axtar/Nixie-Calculator/Docs/Flashing the bootloader and the firmware.pdf

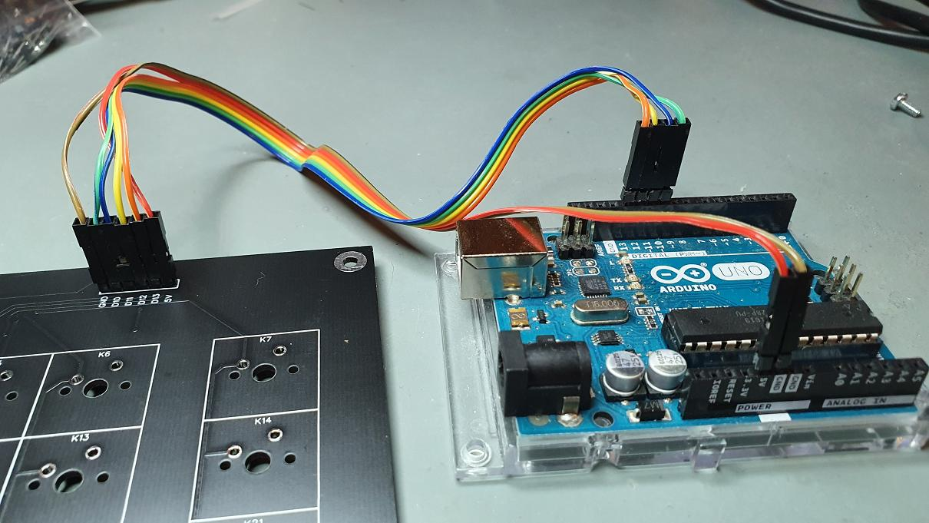
[picture p14: figure]

August 27, 2026 | Draft - Version 0.6 | Page 1 of 3

## Flashing the bootloader and the firmware

Note: the pictures are only intended for a better understanding of the instructions and may not correspond to the latest hardware revision.

### Burning the keyboard bootloader

The keyboard uses an ATmega328p-AU. The bootloader must be burned before flashing the firmware. With an Arduino UNO and the Arduino IDE, the bootloader can be burned directly on the keyboard. I recommend doing this before soldering the switches.

Remove all connections from the keyboard. Then connect the BOOTLOADER header pins to the Arduino UNO (see silkscreen).

Connect the Arduino UNO to your PC and start the Arduino IDE.

Select the Arduino UNO board:

Tools->Board

Select the com port:

Tools->Port->(your com port)

Open the ArduinoISP example:

File->Examples->11ArduinoISP->ArduinoISP

Upload the sketch to the Arduino UNO:

Sketch->Upload

Select the programmer:

Tools->Programmer->Arduino as ISP

Flash the bootloader:

Tools->Burn Bootloader

Check output for errors

### Flashing the keyboard firmware

For the keyboard I use either the Arduino IDE or Visual Studio Code with the PlatformIO extension.

(see Firmware/Keyboard/README_HowToBuild.md).

Power off the calculator and connect a 3.3V or 5V FTDI adapter to the FTDI header on the keyboard. Make sure you connect your adapter the correct way around by checking the ground pin (GND). Then compile and flash the firmware. Check output for errors.

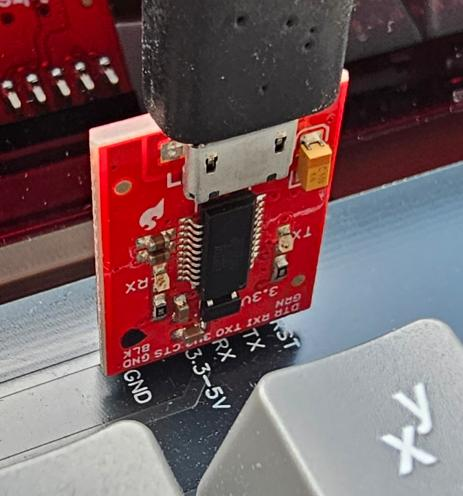
[picture p15: figure]

### Flashing the controller firmware

For the controller, I use Visual Studio Code with the ESP-IDF extension.

(see Firmware/Controller/README_HowToBuild.md)

Power off the calculator and connect a 3.3V FTDI adapter to the controller board. Make sure you connect your adapter the correct way around by checking the ground pin (GND).

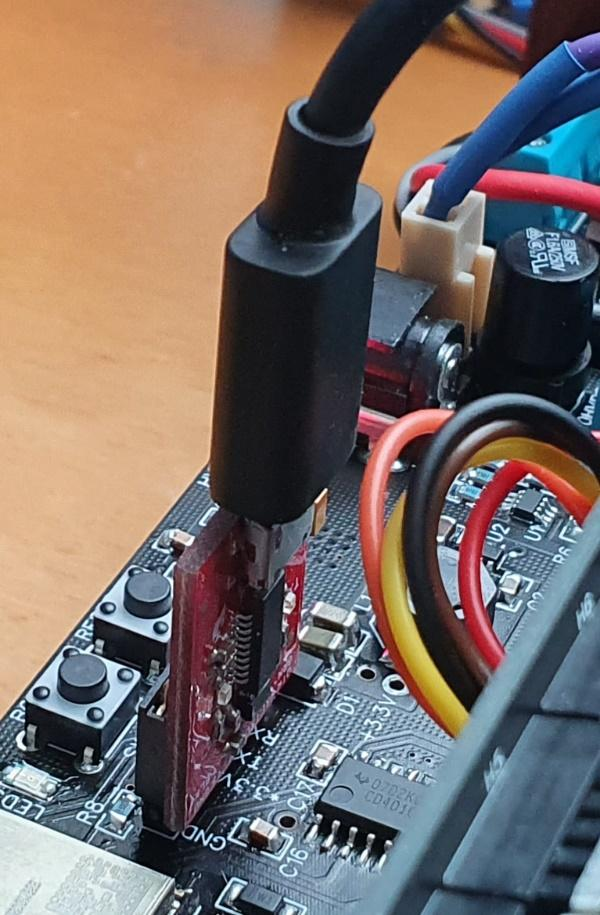
[picture p16: figure]

Build and start flashing the firmware. Once you get the “Connecting…” message, press and hold the “boot” button on the controller board, then press and release the “reset” button and finally release the “boot” button. This should start the flash process. Check output for errors.

### Check firmware versions

After flashing the controller and the keyboard firmware, remove the FTDI adapter and power on the calculator. During start-up, the calculator briefly shows the controller firmware version on the left and the keyboard firmware version on the right.
