axtar/Nixie-Calculator/Docs/Gerber and EasyEDA project files.pdf

August 27, 2026 | Draft – Version 0.3 | Page 1 of 1

## Gerber and EasyEDA project files

Please note that the Gerber files have been regenerated and are untested!

If you use the EasyEDA project files you can make changes and generate your own Gerber files.

You can open the project zip files directly in the EasyEDA designer (Std Edition)

File->Open->EasyEDA

You will get a schematic and a PCB and you can save them to a new project.

You can also import the project zip file into Kicad (8.0.6 or higher) and continue from there.

The case has been designed for 1.6mm boards. For this project I recommend ENIG black for the label board and lead-free (RoHS) black for the other boards. Black boards look better behind the acrylic panel.
