axtar/Nixie-Calculator/Docs/High Voltage Power Supply.pdf

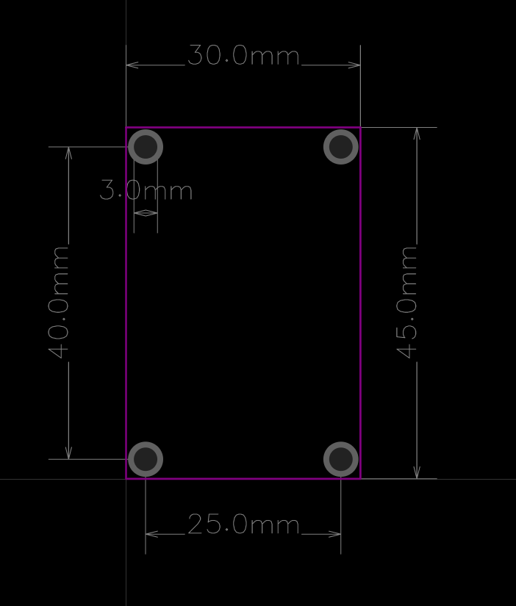
[picture p17: figure]

August 27, 2026 | Draft – Version 0.6 | Page 1 of 2

## High Voltage Power Supply

Although an experimental design for a high-voltage power supply is provided, the use of a good quality and well-tested commercial HV PSU is strongly recommended. Make sure to use genuine power supplies only!

If you decide to design your own HV PSU, you can find the suggested dimensions below.

The HV PSU must be able to deliver at least 50 mA at 170V DC with an input voltage of 12V DC without generating a lot of heat.

Add an appropriate fuse for the HV rail to protect your device from overcurrent!

The voltage should be stable for the entire current range. A calculator is not like a clock, the number of turned-on nixies is not constant. Also check the PSU for audible noise - you don’t want to have a noisy device on your desk.

You may need to change the firmware to correctly drive the enable/shutdown pin of your HV PSU. Currently the firmware sets the HVENABLE pin to HIGH (+3.3V) to enable the HV.

Suggested dimensions:

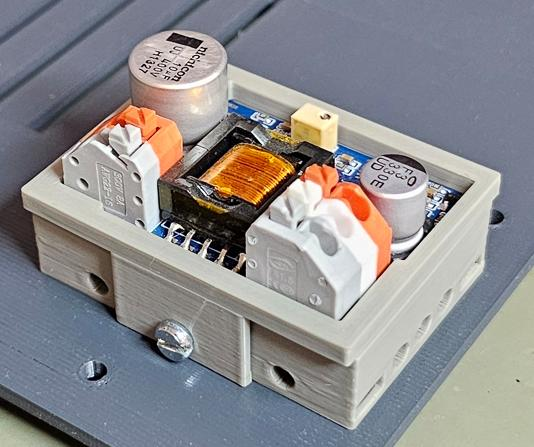
[picture p18: figure]

August 27, 2026 | Draft – Version 0.6 | Page 2 of 2

I’ve designed a 3D printed adapter for the popular NCH6300HV nixie power supply from Omnixie. Maybe the adapter is useful for someone, it provides the missing mounting holes. Use at your own risk.

The adapter consists of 2 parts: 3DPrints/STL/HVFIX Part 1.stl and 3DPrints/STL/HVFIX Part 2.stl. Additionally, you will need 6 x M3 square nuts and 6 x M3 6mm screws.
