axtar/Nixie-Calculator/Docs/Keyboard layout and keycaps.pdf

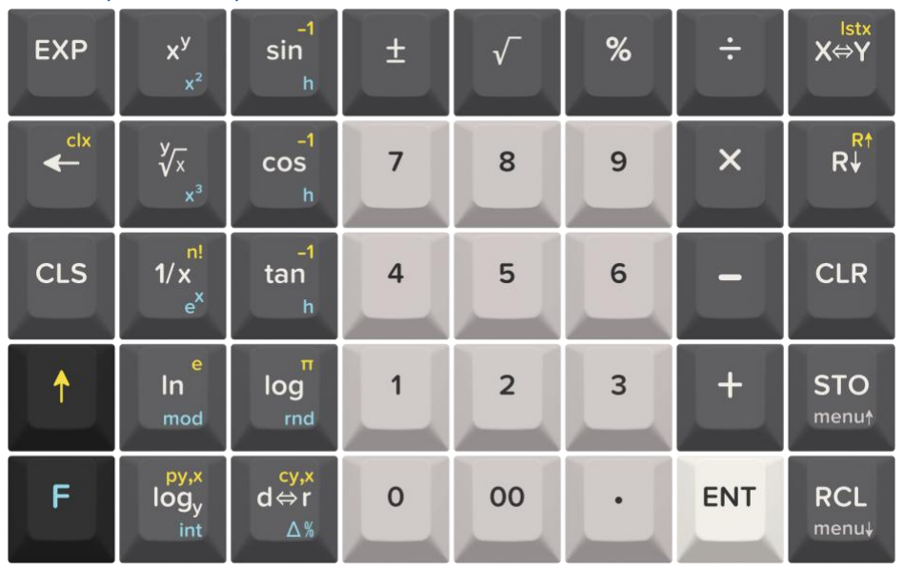
[picture p19: figure]
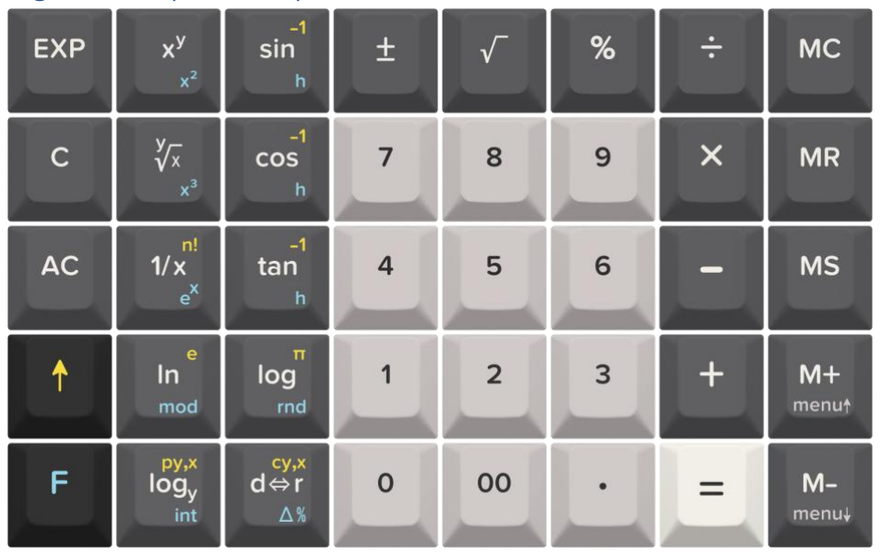
[picture p20: figure]

July 12, 2026 | Draft - Version 0.8 | Page 1 of 1

## Keyboard layout and keycaps

For this project we need some custom Cherry MX keycaps. I came up with the keyboard layouts as shown in the pictures. All keycaps are 1x1.

### RPN keyboard layout

### Algebraic keyboard layout

### Keycaps

If you prefer commercial keycaps, you may use the json design files in the Keycaps directory as a starting point for your own design. You can import the “tf” file into the Thockfactory configurator or the “yz” files into the Yuzu Keycaps advanced editor.

You can also use transparent keycaps (e.g. from X-keys) and print your own legends. I created the Keycaps/keycaps.svg file with Inkscape, then printed the “Legends” and the “Background” layers on glossy photo paper and finally cut out the “Keys” layer with a cutting plotter.
