axtar/Nixie-Calculator/Docs/Mounting the  nixies.pdf

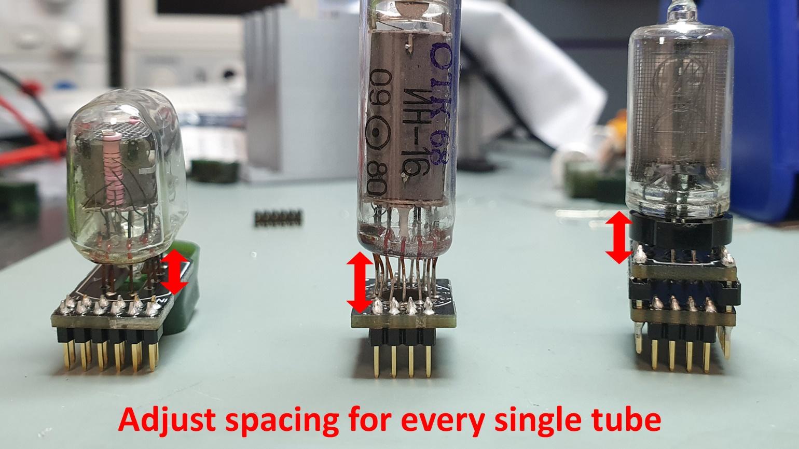
[picture p21: figure]

July 1, 2025 | Draft – Version 0.2 | Page 1 of 10

## Mounting the nixies

Note: the pictures are only intended for a better understanding of the instructions and may not correspond to the latest hardware revision.

The dimensions of tubes of the same type, as well as the position of the digits within the tube, can vary significantly. There are also different spacers for the B-5870. For this reason, I cannot provide the exact spacing for mounting the nixies on the socket boards.

- For the IN-16, IN-17 and B-5870 versions, don’t use nixies wider than 13mm if you cannot compensate the difference with the adjacent tubes. Also check, that the exhaust tips are not too long to fit in the case.
However, I haven't had any problems with any of my (unmatched) tubes so far.
- Correctly adjust the distance between the end of the tube and the top of the socket board to have all digits at the same level and to make sure that they fit into the case. A good starting point is 5mm for the IN-16 and 4mm for the IN-17. For the B-5870, I just used the plastic spacer, my tubes have a small one. However, it is up to you to find the correct spacing.
- Always check that everything is correct before soldering the nixies to the socket boards.
- Don’t stress the leads/pins of the nixies.

### IN-12/IN-15A version

The nixies are mounted on appropriate socket pins.

- Display board with the socket pins

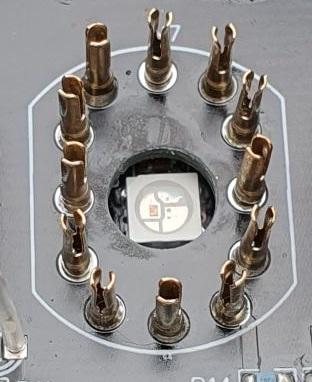
[picture p22: figure]

- Insert the nixie and check orientation, pin order and alignment

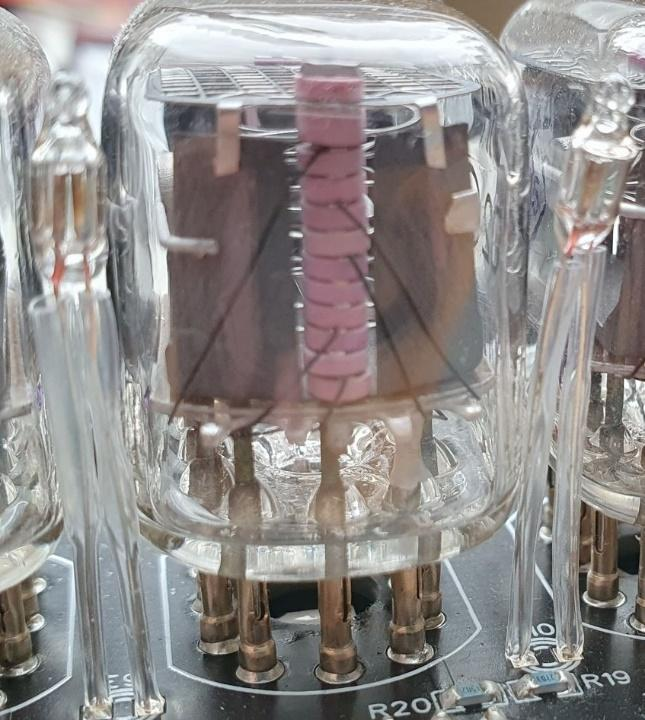
[picture p23: figure]

### IN-16 version

The nixies are soldered on a socket board without the plastic spacer to allow underlighting. The calculator uses the right decimal point of the nixie. A = anode.

- IN-16 socket board

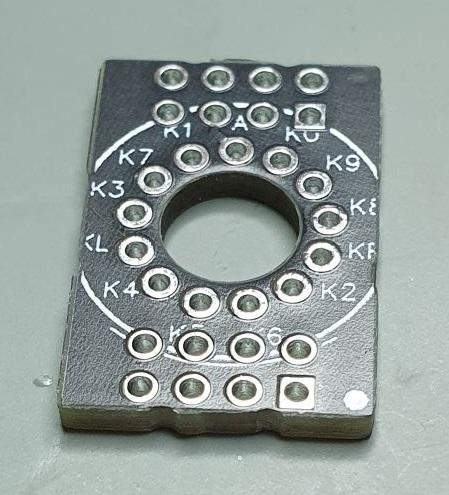
[picture p24: figure]

- Insert the nixie leads into the socket board

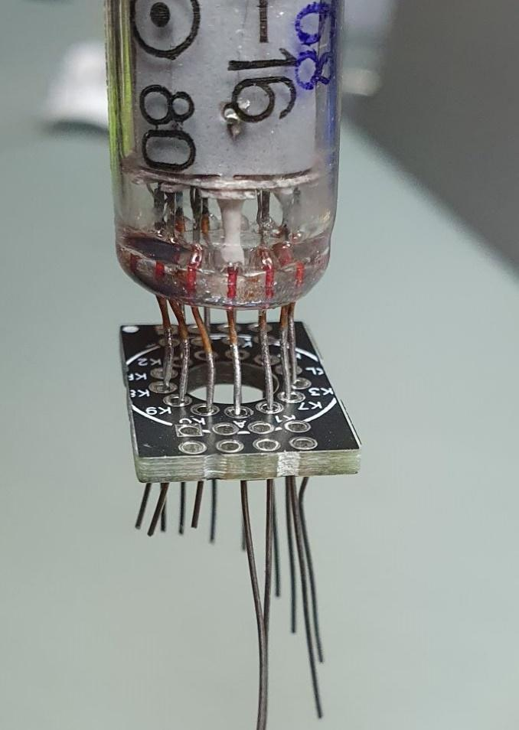
[picture p25: figure]

- Check orientation, pin order, alignment and spacing
- Solder the nixie leads and cut off the excess

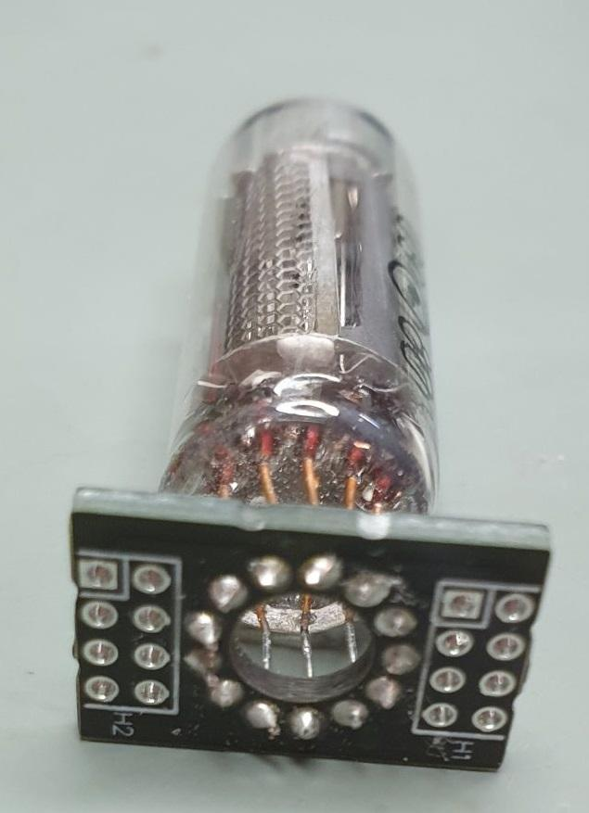
[picture p26: figure]

- Mount and solder the headers

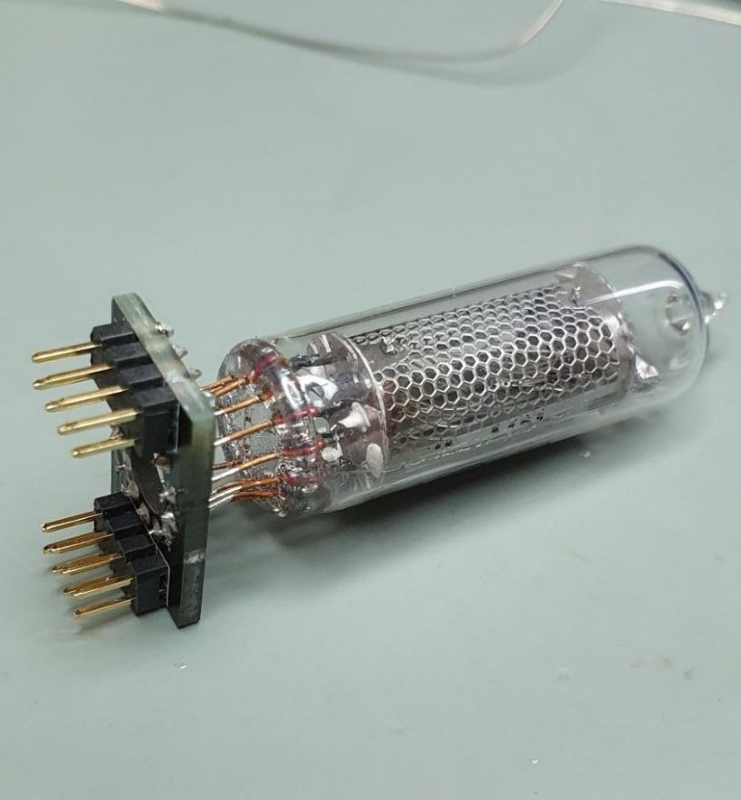
[picture p27: figure]

### IN-17 version

The IN-17 nixies are soldered on a socket board without the plastic spacer to allow backlighting. A = anode.

- IN-17 socket board

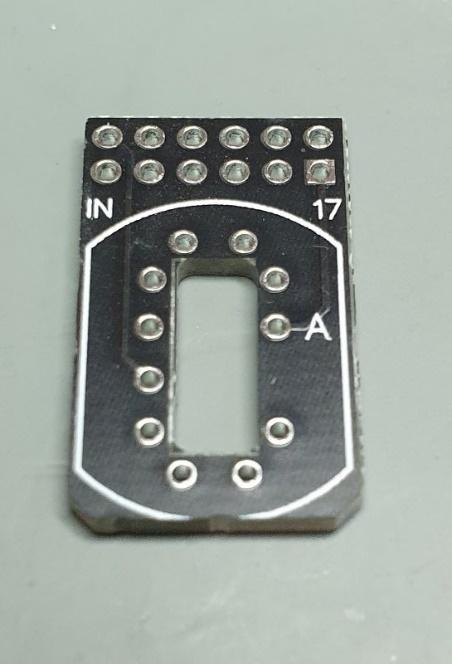
[picture p28: figure]

- Insert the nixie leads into the socket board

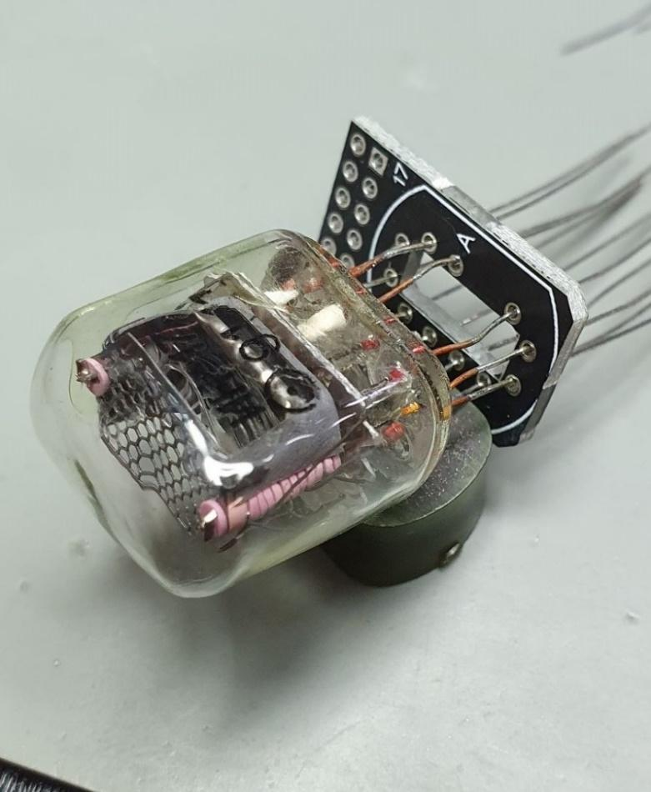
[picture p29: figure]

- Check orientation, pin order, alignment and spacing
- Solder the nixie leads and cut off the excess

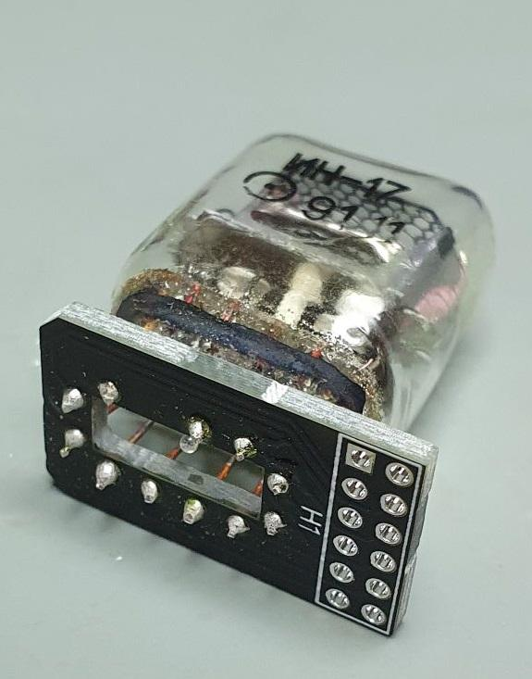
[picture p30: figure]

- Mount and solder the header

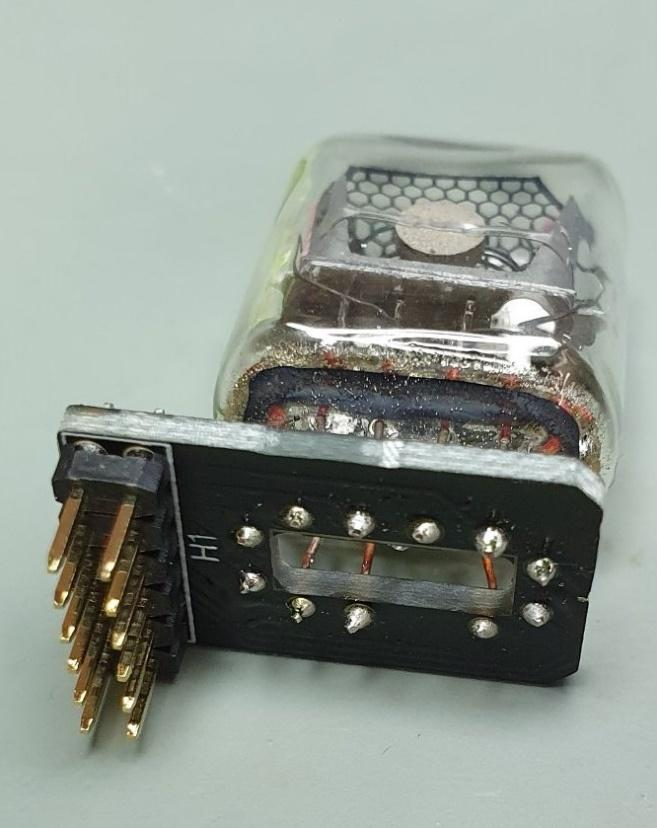
[picture p31: figure]

### B-5870 version

The nixies are soldered on a socket board. Since there is no underlighting available for the B-5870 version, it is up to you to decide whether you use the plastic spacer or not. Please note that there are different sizes of spacers for these tubes. The socket board is mounted on an additional adaptor board. The calculator uses the right decimal point of the nixie.

- B-5870 socket board

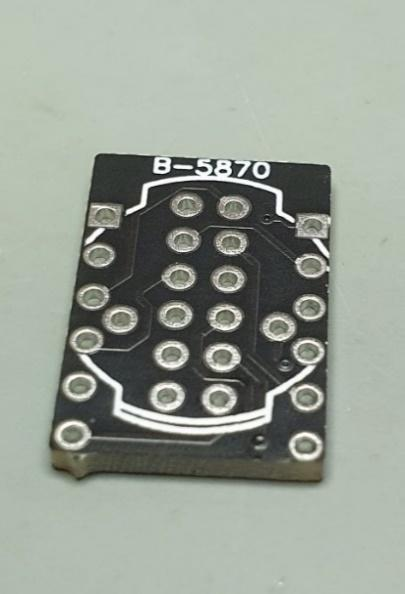
[picture p32: figure]

- Mount and solder the headers

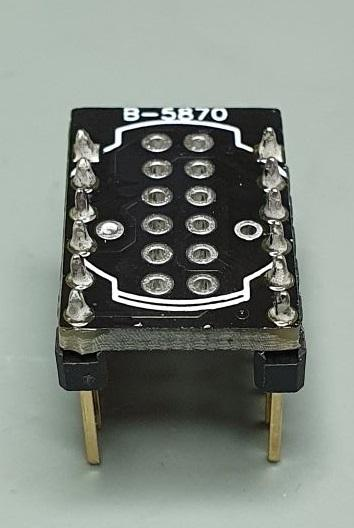
[picture p33: figure]

- Insert the nixie leads into the socket board

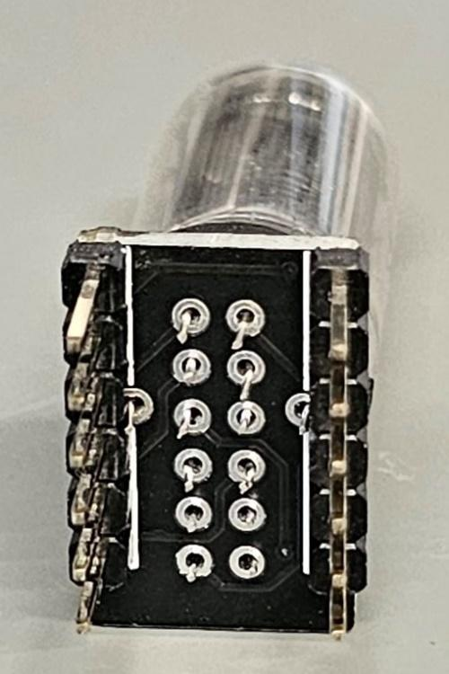
[picture p34: figure]

- Check orientation, pin order, alignment and spacing
- Solder the nixie leads and cut off the excess

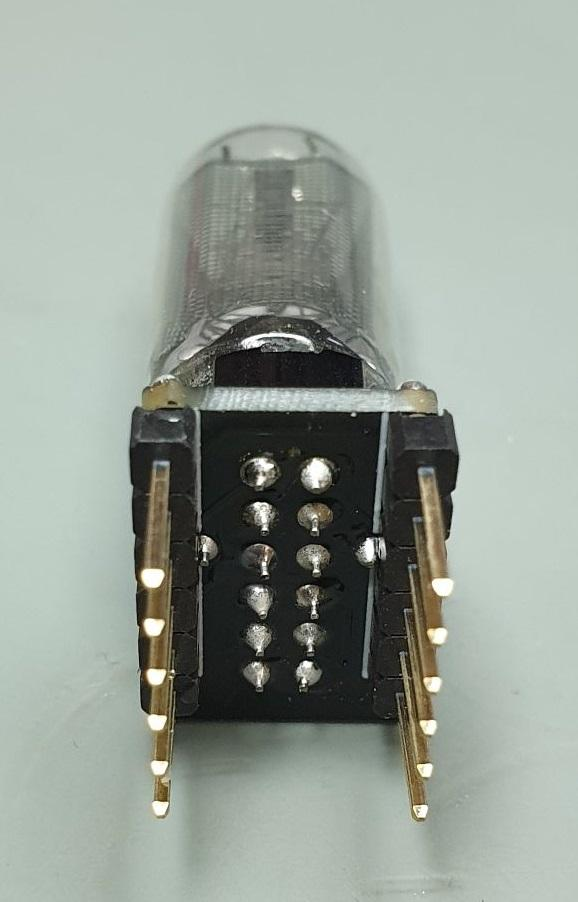
[picture p35: figure]

- B-5870 socket adaptor board

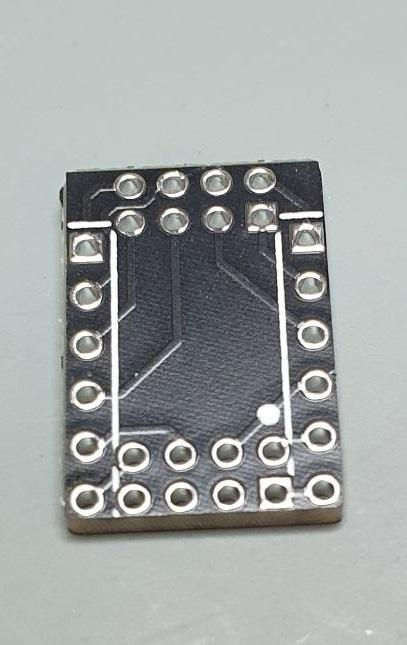
[picture p36: figure]

- Mount and solder the headers

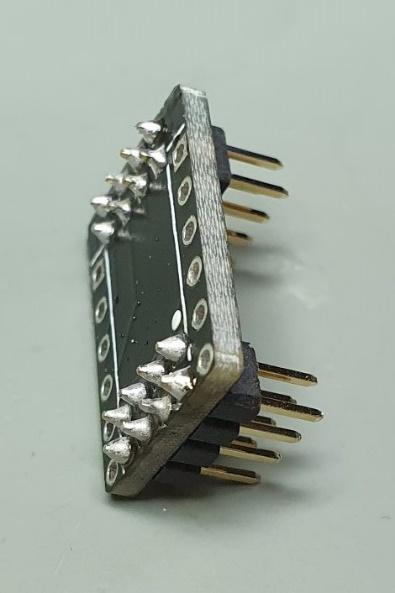
[picture p37: figure]

- Solder the socket board to the socket adaptor board leaving a gap between them

Make sure, that there are no shorts between the socket board and the adaptor board!

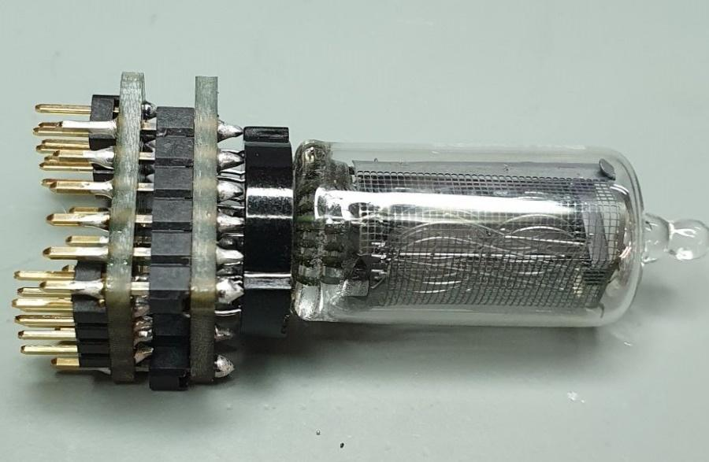
[picture p38: figure]
