axtar/Nixie-Calculator/Docs/PCB List.pdf

September 1, 2026 | Draft – Version 0.3 | Page 1 of 2

## PCB List

IN-12 Version
Qty | Board | Comment
1 | Controller_Rev2a
1 | Keyboard_Rev2
1 | IN-12_Display_Rev2
1 | IN-12_Driver_Rev2
1 | IN-12_LEDs_Rev2
1 | High_Voltage_PSU_Rev2 | only required if not using a commercial PSU
1 | Label_Rev2

IN-16 Version
Qty | Board | Comment
1 | Controller_Rev2a
1 | Keyboard_Rev2
1 | IN-16_Display_Rev2
1 | IN-16_Driver_Rev2
1 | IN-16_LEDs_Rev2 | for underlighting only (recommended)
14 | IN-16_Socket_Rev2
1 | High_Voltage_PSU_Rev2 | only required if not using a commercial PSU
1 | Label_Rev2

IN-17 Version
Qty | Board | Comment
1 | Controller_Rev2a
1 | Keyboard_Rev2
1 | IN-17_Display_and_Driver_Rev2
14 | IN-17_Socket_Rev2
1 | High_Voltage_PSU_Rev2 | only required if not using a commercial PSU
1 | Label_Rev2

B-5870 Version
Qty | Board | Comment
1 | Controller_Rev2a
1 | Keyboard_Rev2
1 | IN-16_Display_Rev2
1 | IN-16_Driver_Rev2
14 | B-5870_Socket_Rev2
14 | B-5870_Socket_Adaptor_Rev2
1 | High_Voltage_PSU_Rev2 | only required if not using a commercial PSU
1 | Label_Rev2

September 1, 2026 | Draft – Version 0.3 | Page 2 of 2

7-seg LED version
Qty | Board | Comment
1 | Controller_Rev2a
1 | Keyboard_Rev2
1 | LED7SEG_Display_Rev1
1 | LED7SEG_Driver_Rev1
1 | Label_Rev2

Peripherals
Qty | Board | Comment
1 | Peripherals_Rev2
