axtar/Nixie-Calculator/BOM/BOM_Nixie_Calculator_7SEGLED_Display_Rev1.pdf

BOM Nixie Calculator 7SEGLED Display Rev.1 | 30/06/2025
ID | Quantity | Value | Additional | Designator | Footprint | Type | Manufacturer Part | Manufacturer
1 | 2 | SC36-11SURKWA | | LED0,LED15 | | 7-seg LED display | SC36-11SURKWA | Kingbright
2 | 14 | SC56-11SURKWA | | LED1-LED14 | | 7-seg LED display | SC56-11SURKWA | Kingbright
3 | 1 | 2x17 box header, 2.54mm | | P1 | | Box header
