axtar/Nixie-Calculator/BOM/BOM_Nixie_Calculator_7SEGLED_Driver_Rev1.pdf

BOM Nixie Calculator 7SEGLED Driver Rev.1 | 30/06/2025
ID | Quantity | Value | Additional | Designator | Footprint | Type | Manufacturer Part | Manufacturer
1 | 2 100n | | 50V | C1,C2 | 0805 | Capacitor | C0805C104M5RACTU | KEMET
2 | 2 39k | | | R1,R2 | 0805 | Resistor | RK73H2ATTD3902F | KOA Speer
3 | 2 MAX7219CWG+ | | | U0,U1 | SOIC-24 | LED driver | MAX7219CWG+ | Analog Devices
4 | 1 1x6 header, 2.54mm | | | J1 | | Locking header
5 | 1 2x17 box header, 2.54mm | | | P1 | | Box header
