axtar/Nixie-Calculator/BOM/BOM_Nixie_Calculator_IN-12_Display_Rev2.pdf

BOM Nixie Calculator IN-12 Display Rev.2 | 19/07/2025
ID | Quantity | Value | Additional | Designator | Footprint | Type | Manufacturer Part | Manufacturer
1 | 16 | 15k | 1/4W | R0-R15 | 0805 | Resistor | RK73H2ATTD1502F | KOA Speer
2 | *14 | 270k | 1/4W | R16-R29 | 0805 | Resistor | RK73H2ATTD2703F | KOA Speer
3 | **14 | 82k | 1/4W | R30-R43 | 0805 | Resistor | RK73H2ATTD8202F | KOA Speer
4 | 2 | IN-15A Nixie | | N0,N15 | | Nixie tube
5 | 14 | IN-12A or IN-12B Nixie | | N1-N14 | | Nixie tube
6 | *14 | Neon 4mm | | E1-14 | | Neon lamp
7 | 1 | 2 poles terminal block | | HV | | Fixed Terminal Block | TB006-508-02BE | CUI Devices
8 | 32 | 1x6 Header | female, 200V | H1-H32 | | Header
9 | 192 | Single receptacle contacts | for 1mm pins
* if using neon bulbs as decimal point
** if using IN-12B decimal point
