axtar/Nixie-Calculator/BOM/BOM_Nixie_Calculator_IN-12_Driver_Rev2.pdf

BOM Nixie Calculator IN-12 Driver Rev.2 | 30/06/2025
ID | Quantity | Value | Additional | Designator | Footprint | Type | Manufacturer Part | Manufacturer
1 | 6 | 100n | 50V | C1-C6 | 0805 | Capacitor | C0805C104M5RACTU | KEMET
2 | 6 | HV5622 | | U1-U6 | PQFP-44 | IC | HV5622PG-G | Microchip Technology
3 | 32 | 1x6 header 2.54mm | male, 200V | J1-J32 | | Header
4 | 1 | 1x6 header, 2.54mm | male, right angle | H1 | | Locking header
