axtar/Nixie-Calculator/BOM/BOM_Nixie_Calculator_IN-12_LEDs_Rev2.pdf

BOM Nixie Calculator IN-12 LEDs Rev.2 | 30/06/2025
ID | Quantity | Value | Additional | Designator | Footprint | Type | Manufacturer Part | Manufacturer
1 | 1 | 330 | 1/4W | R1 | 0805 | Resistor | RK73H2ATTD3300F | KOA Speer
2 | 16 | 100n | 50V | C1-C16 | 0805 | Capacitor | C0805C104M5RACTU | KEMET
3 | 1 | 47uF | 25V | C17 | 1206 | Capacitor | C3216X5R1E476M160AC | TDK
4 | 16 | Neopixel RGB SK6812 | | D1-D16 | 5050 | RGB LED | SK6812
5 | 1 | 1x3 header, 2.54mm | male, right angle | H1 | | Locking header
