axtar/Nixie-Calculator/BOM/BOM_Nixie_Calculator_IN-16_LEDs_Rev2.pdf

BOM Nixie Calculator IN-16 LEDs Rev.2 | 30/06/2025
ID | Quantity | Value | Additional | Designator | Footprint | Type | Manufacturer Part | Manufacturer
1 | 1 | 330 | 1/4W | R1 | 0805 | Resistor | RK73H2ATTD3300F | KOA Speer
2 | 1 | 47uF | 25V | C1 | 1206 | Capacitor | C3216X5R1E476M160AC | TDK
3 | 14 | Neopixel RGB SK6812 | | D1-D14 | 5050 | RGB LED | SK6812
* | H1: there is no space for a header, solder the wires directly to the board
