axtar/Nixie-Calculator/3DPrints/STL/Nixie Calculator Keyboard Cover.stl

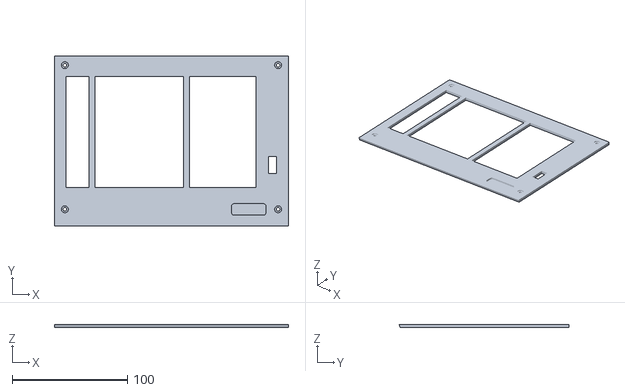
[picture p55: CAD file, 2026-09-16]
3DPrints/STL/Nixie Calculator Keyboard Cover.stl
203.0 x 147.5 x 3.00
