axtar/Nixie-Calculator/3DPrints/STL/Nixie Calculator IN-12 Back Shield.stl

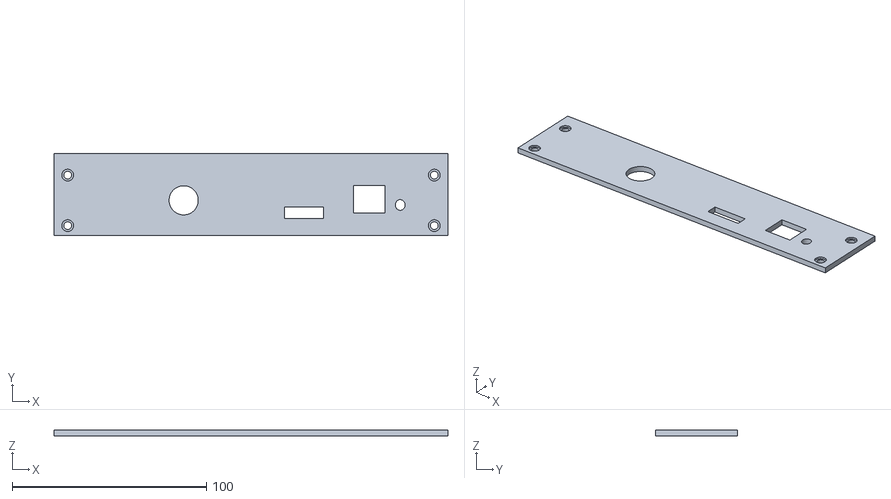
[picture p56: CAD file, 2026-09-16]
3DPrints/STL/Nixie Calculator IN-12 Back Shield.stl
202.8 x 42.0 x 3.00
