axtar/Nixie-Calculator/3DPrints/STL/Nixie Calculator IN-12 Tube Holder Part 2.stl

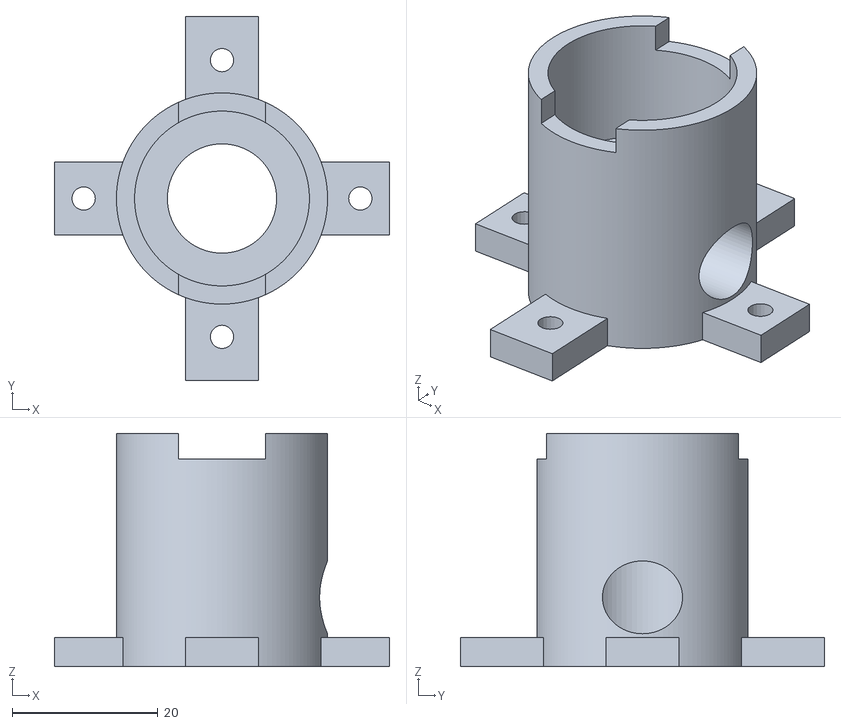
[picture p57: CAD file, 2026-09-16]
3DPrints/STL/Nixie Calculator IN-12 Tube Holder Part 2.stl
46.0 x 50.0 x 32.0
