axtar/Nixie-Calculator/3DPrints/STL/Nixie Calculator IN-12 Top.stl

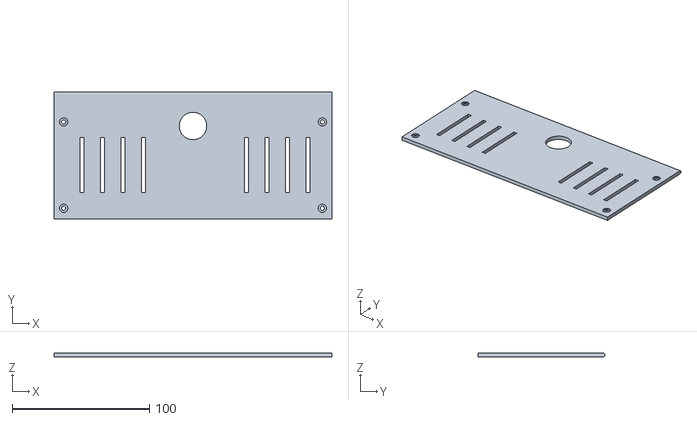
[picture p58: CAD file, 2026-09-16]
3DPrints/STL/Nixie Calculator IN-12 Top.stl
202.8 x 93.0 x 3.00
