axtar/Nixie-Calculator/3DPrints/STL/Nixie Calculator IN-12 Left.stl

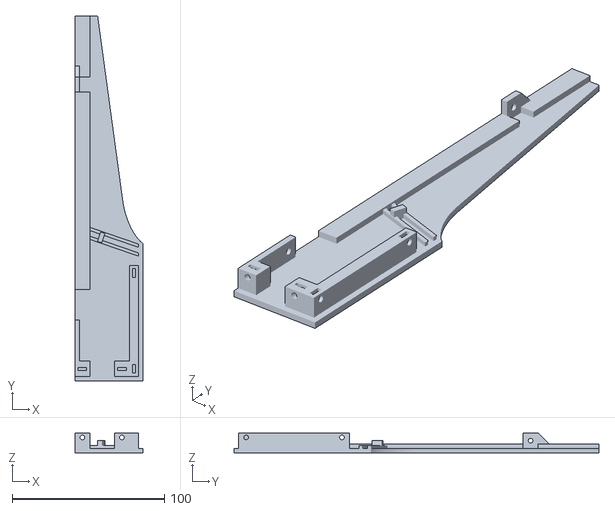
[picture p59: CAD file, 2026-09-16]
3DPrints/STL/Nixie Calculator IN-12 Left.stl
45.0 x 240.0 x 13.0
