axtar/Nixie-Calculator/3DPrints/STL/Nixie Peripherals RJ45 Part3.stl

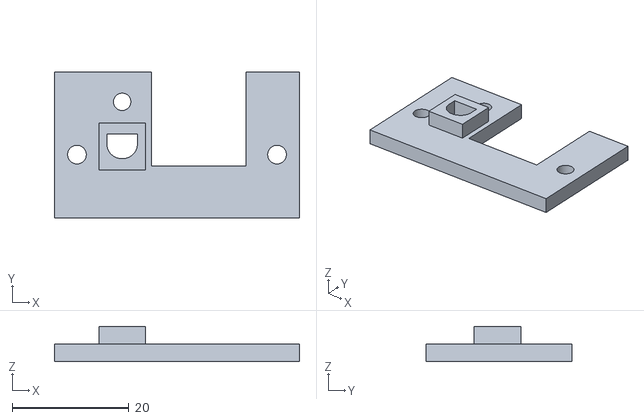
[picture p60: CAD file, 2026-09-16]
3DPrints/STL/Nixie Peripherals RJ45 Part3.stl
42.0 x 25.0 x 6.00
