axtar/Nixie-Calculator/3DPrints/STL/Nixie Calculator Back Shield.stl

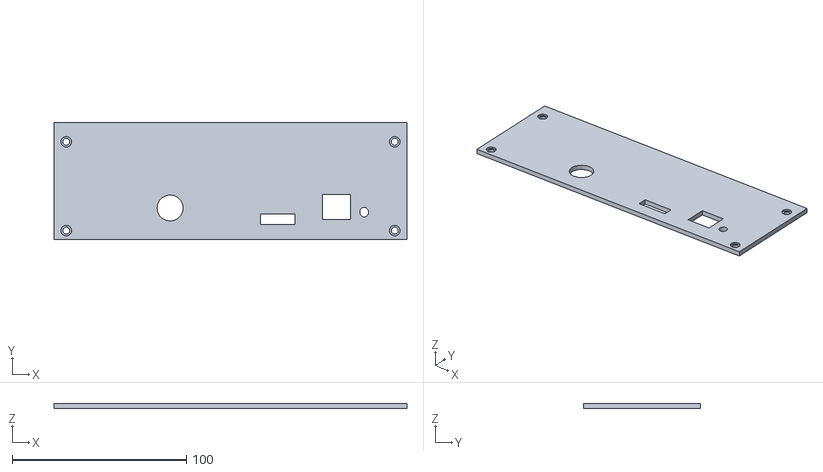
[picture p61: CAD file, 2026-09-16]
3DPrints/STL/Nixie Calculator Back Shield.stl
202.8 x 67.0 x 3.00
