axtar/Nixie-Calculator/3DPrints/STL/Nixie Peripherals RJ45 Part 2.stl

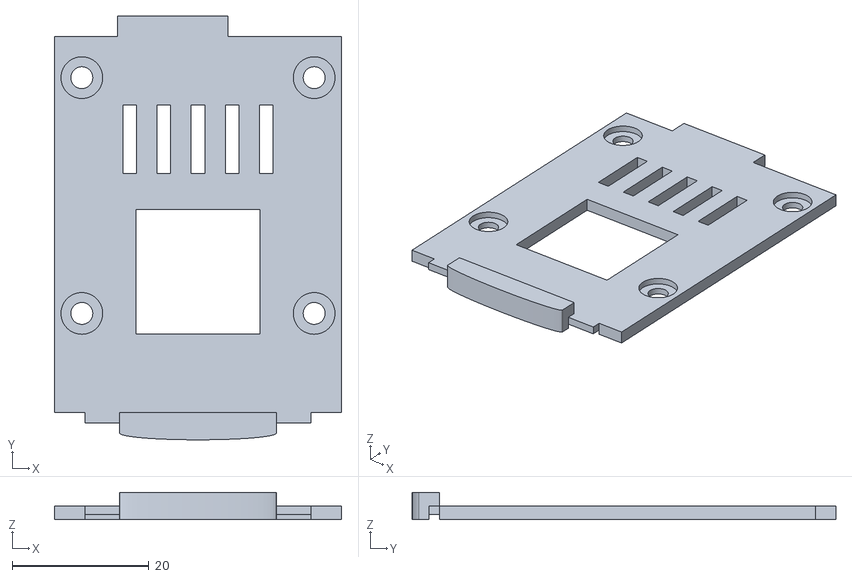
[picture p62: CAD file, 2026-09-16]
3DPrints/STL/Nixie Peripherals RJ45 Part 2.stl
42.0 x 62.0 x 4.00
