axtar/Nixie-Calculator/3DPrints/STL/Nixie Calculator Front V2.stl

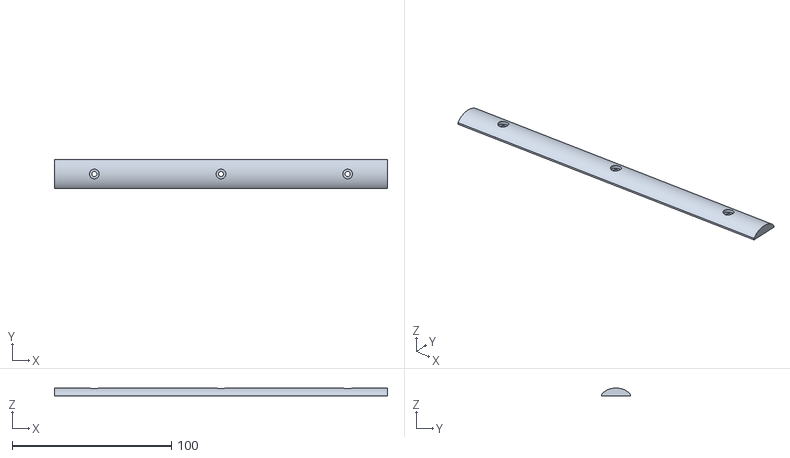
[picture p63: CAD file, 2026-09-16]
3DPrints/STL/Nixie Calculator Front V2.stl
209.0 x 18.0 x 5.00
