axtar/Nixie-Calculator/3DPrints/STL/HVFIX Part 2.stl

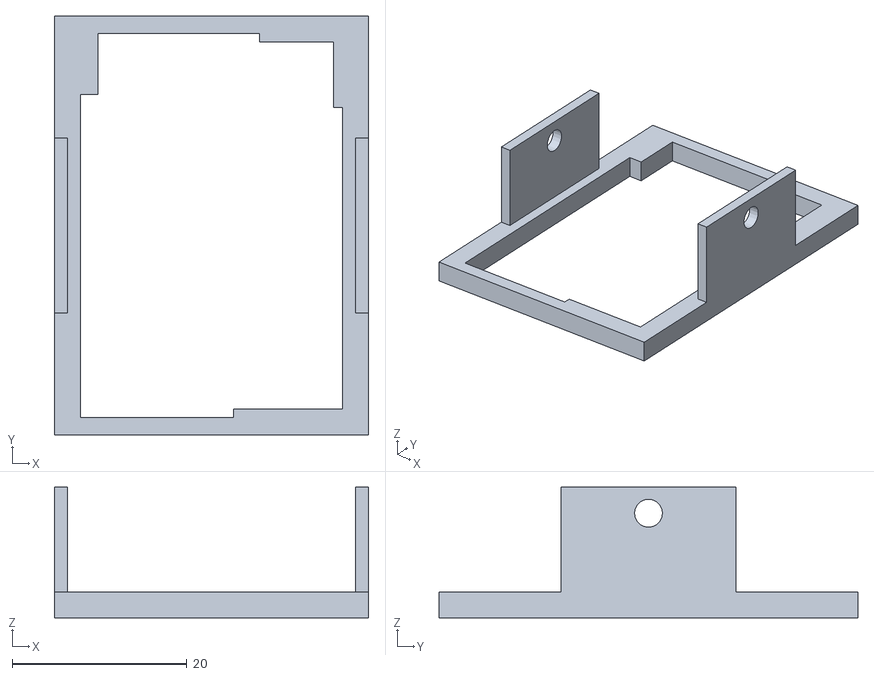
[picture p64: CAD file, 2026-09-16]
3DPrints/STL/HVFIX Part 2.stl
36.0 x 48.0 x 15.0
