axtar/Nixie-Calculator/3DPrints/STL/Nixie Calculator IN-17 Display Frame.stl

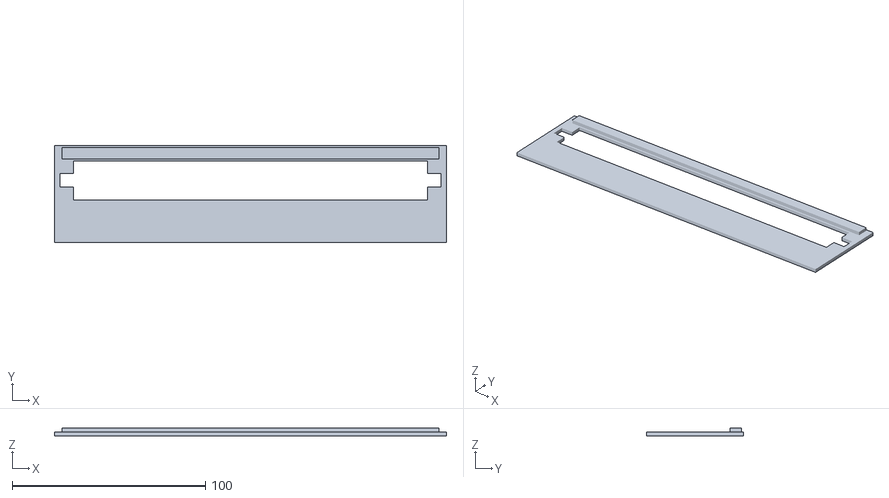
[picture p65: CAD file, 2026-09-16]
3DPrints/STL/Nixie Calculator IN-17 Display Frame.stl
203.0 x 50.0 x 4.00
