axtar/Nixie-Calculator/3DPrints/STL/Nixie Calculator Top.stl

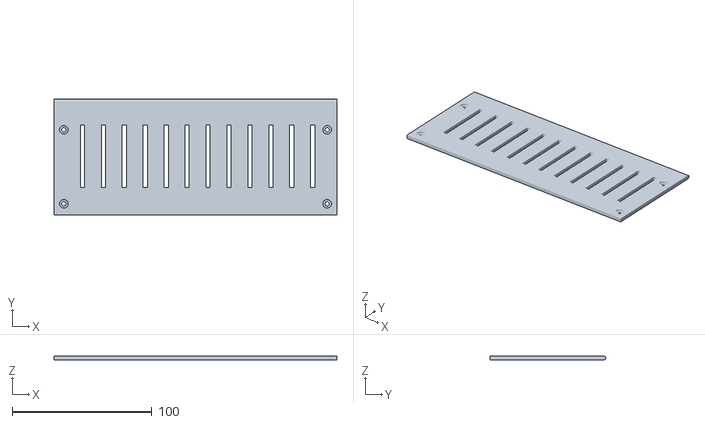
[picture p66: CAD file, 2026-09-16]
3DPrints/STL/Nixie Calculator Top.stl
202.8 x 83.0 x 3.00
