axtar/Nixie-Calculator/3DPrints/STL/Nixie Calculator B-5870 Socket Cover.stl

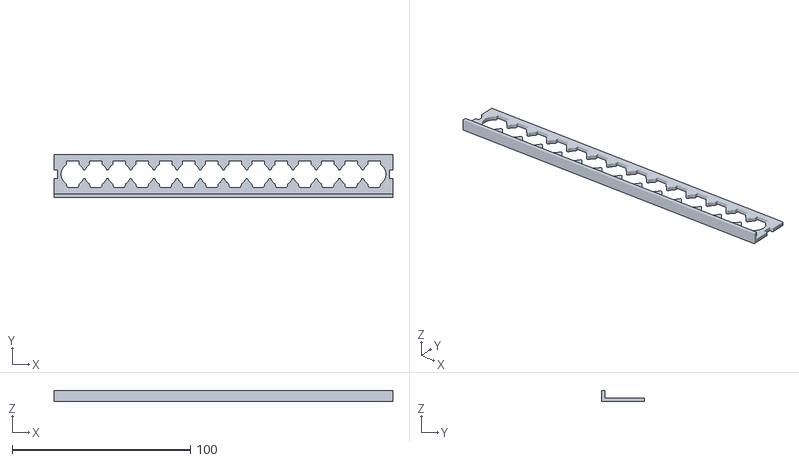
[picture p67: CAD file, 2026-09-16]
3DPrints/STL/Nixie Calculator B-5870 Socket Cover.stl
190.0 x 24.0 x 6.00
