axtar/Nixie-Calculator/3DPrints/STL/Nixie Peripherals RJ45 Part 1.stl

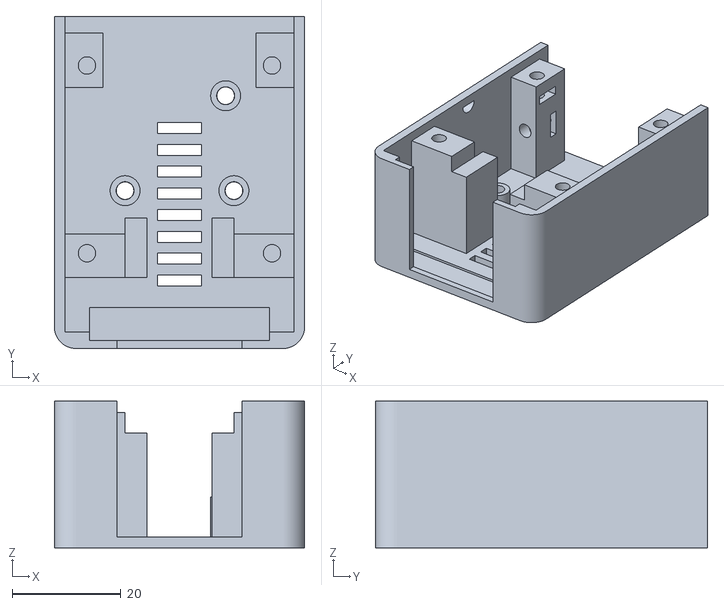
[picture p68: CAD file, 2026-09-16]
3DPrints/STL/Nixie Peripherals RJ45 Part 1.stl
46.0 x 61.0 x 27.0
