axtar/Nixie-Calculator/3DPrints/STL/Nixie Calculator IN-12 Union Tube V2.stl

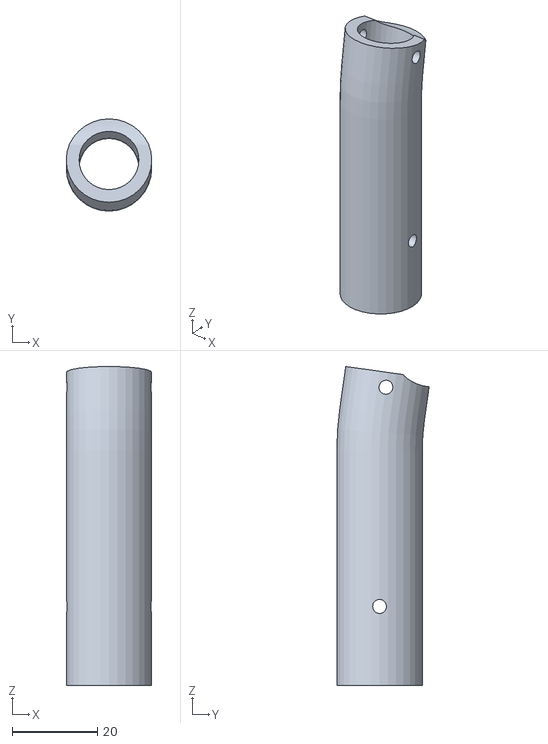
[picture p69: CAD file, 2026-09-16]
3DPrints/STL/Nixie Calculator IN-12 Union Tube V2.stl
20.0 x 21.6 x 74.6
