axtar/Nixie-Calculator/Docs/Assembling the calculator - 7-seg LED - version.pdf

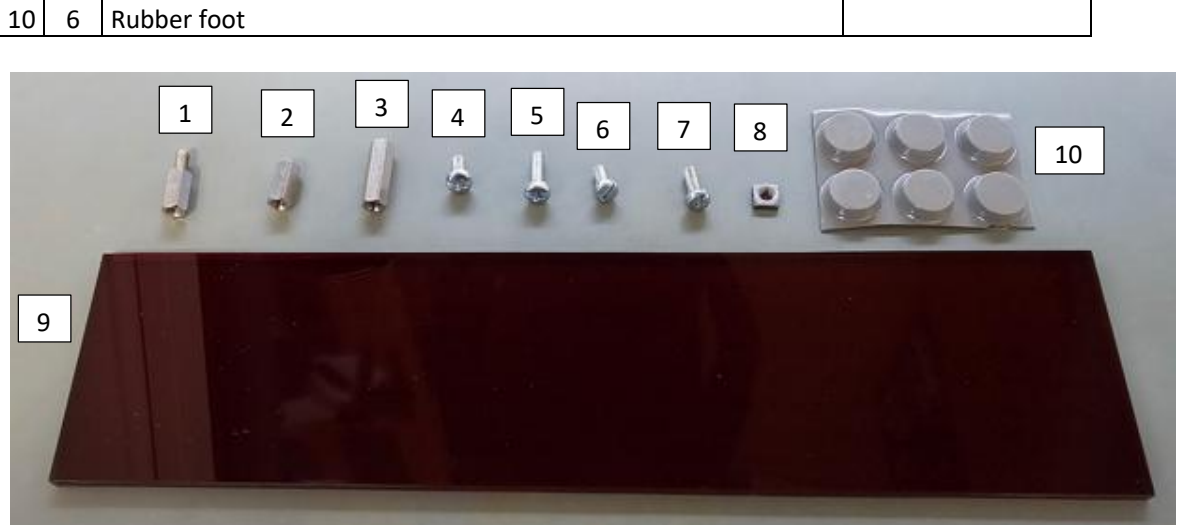
[picture p70: figure]
Rubber foot

August 27, 2026 | Draft - Version 0.5 | Page 1 of 9

## Assembling the calculator – 7-seg LED - version

Note: the pictures are only intended for a better understanding of the instructions and may not correspond to the latest hardware revision.

### Things you will need

- Assembled boards
- Keycaps
- Cables and connectors:
ID | Qty | Wires | Mode | Comment
SWITCH | 1 | 2 | straight | Mount connectors on both ends
KEYBOARD | 1 | 5 | straight | Mount connectors on both ends
DRIVER | 1 | 6 | straight | Mount connectors on both ends
P1 | 1 | 34 | straight | Ribbon cable, mount connectors on both ends
Double-check the pin order and polarity of all connections before you power up the device.
- 3D printed case parts
- Additional parts:
ID | Qty | Description | Comment
1 | 6 | Standoff, 10mm, female/male
2 | 10 | Standoff, 10mm, M3, female/female
3 | 3 | Standoff, 16mm, M3, female/female
4 | 4 | Pan head screw, 6mm, M3
5 | 11 | Pan head screw, 10mm, M3
6 | 17 | Screw, 6mm, M3
7 | 10 | Screw, 8mm, M3
8 | 16 | Square nut, M3, 5.5 x 5.5 x 1.8mm, DIN562
9 | 1 | Piece of transparent acrylic 203mm x 50mm x 3mm (red)

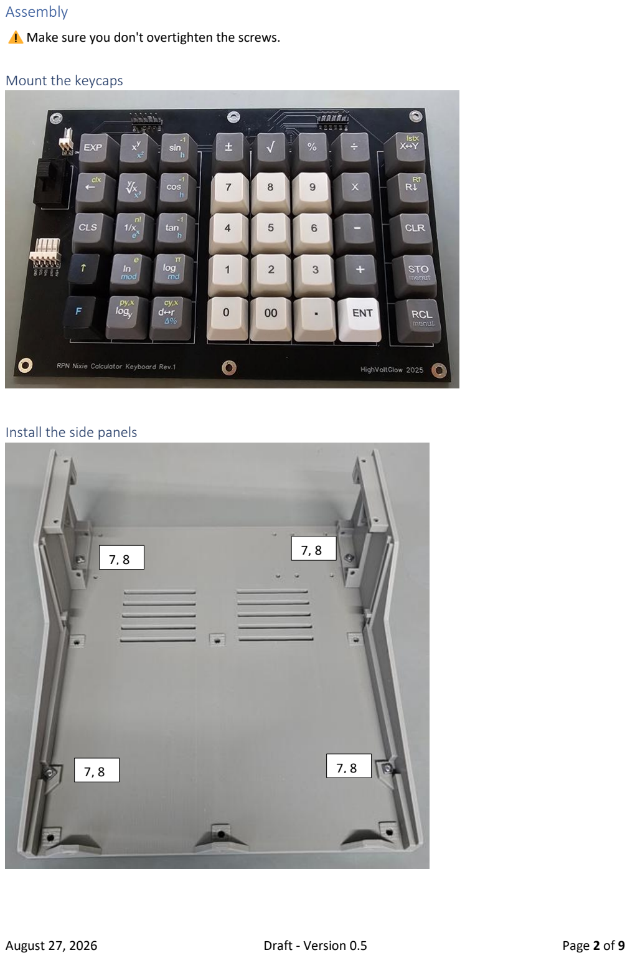
[picture p71: page 2]

### Assembly

Make sure you don't overtighten the screws.

Mount the keycaps

Install the side panels

7, 8

7, 8 | 7, 8

7, 8

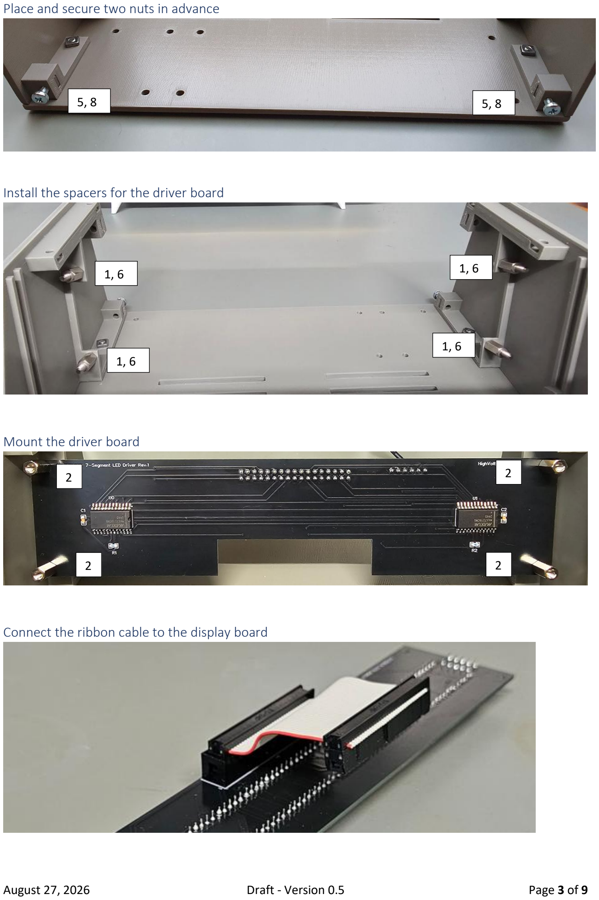
[picture p72: page 3]

Place and secure two nuts in advance

Install the spacers for the driver board

Mount the driver board

Connect the ribbon cable to the display board

5, 8 | 5, 8
1, 6 | 1, 6

1, 6

1, 6

2

2

2 | 2

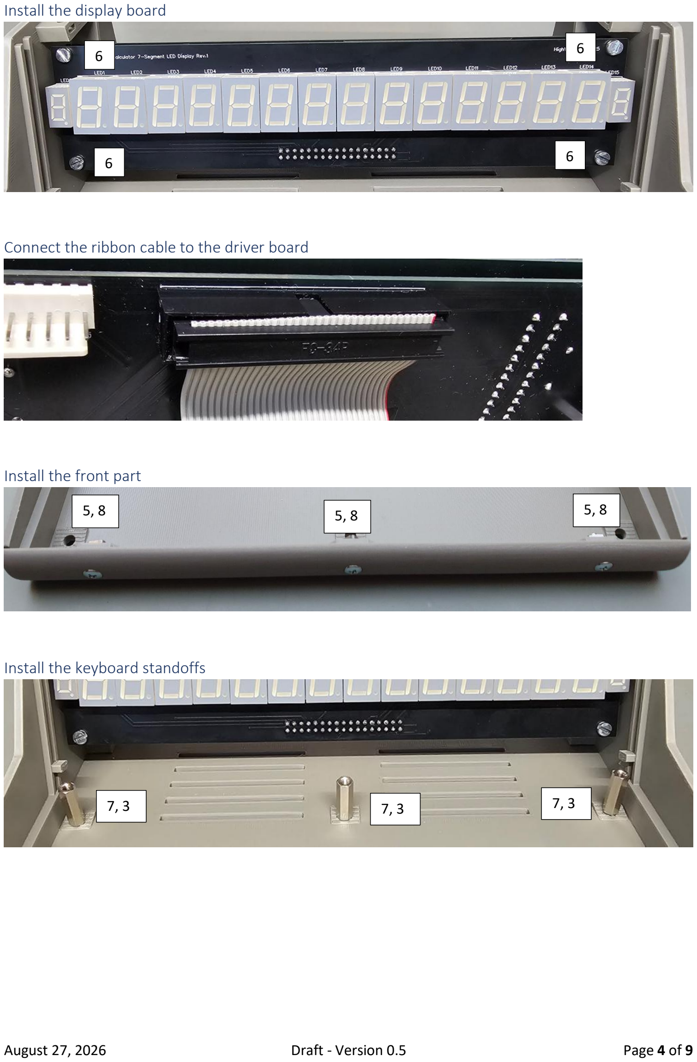
[picture p73: page 4]

Install the display board

Connect the ribbon cable to the driver board

Install the front part

Install the keyboard standoffs

5, 8 | 5, 8 | 5, 8
7, 3 | 7, 3 | 7, 3

6

6

6
6

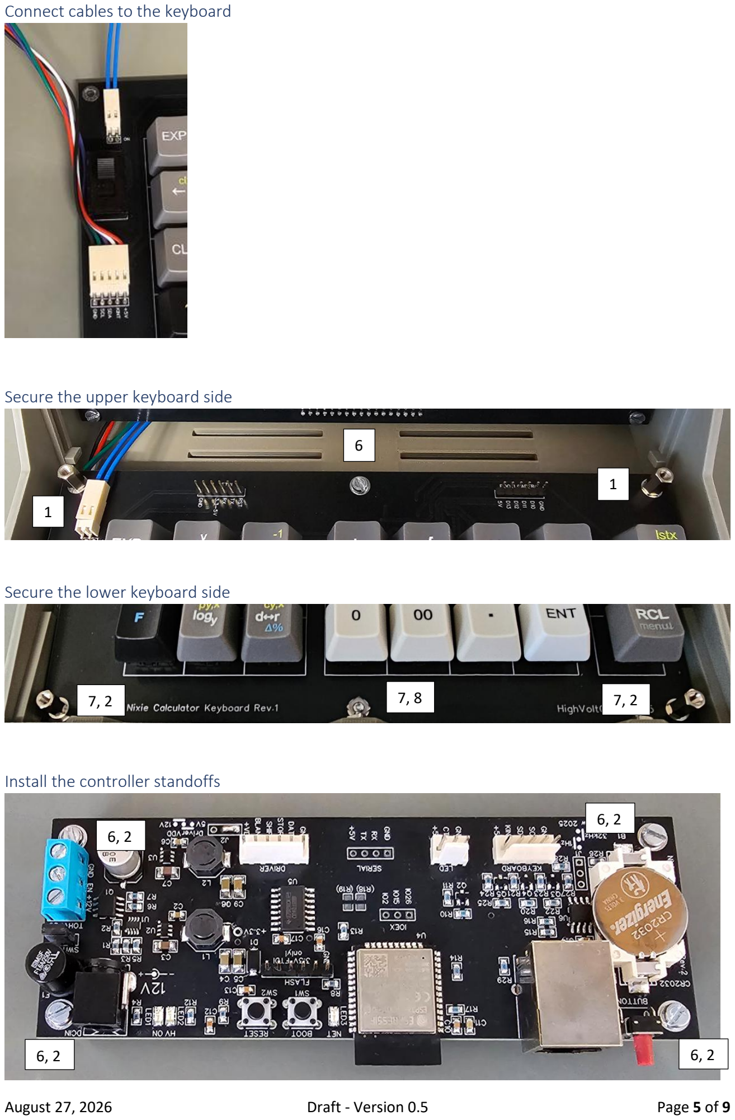
[picture p74: page 5]

Connect cables to the keyboard

Secure the upper keyboard side

Secure the lower keyboard side

Install the controller standoffs

1

1

6

7, 2 | 7, 8 | 7, 2

6, 2

6, 2

6, 2

6, 2

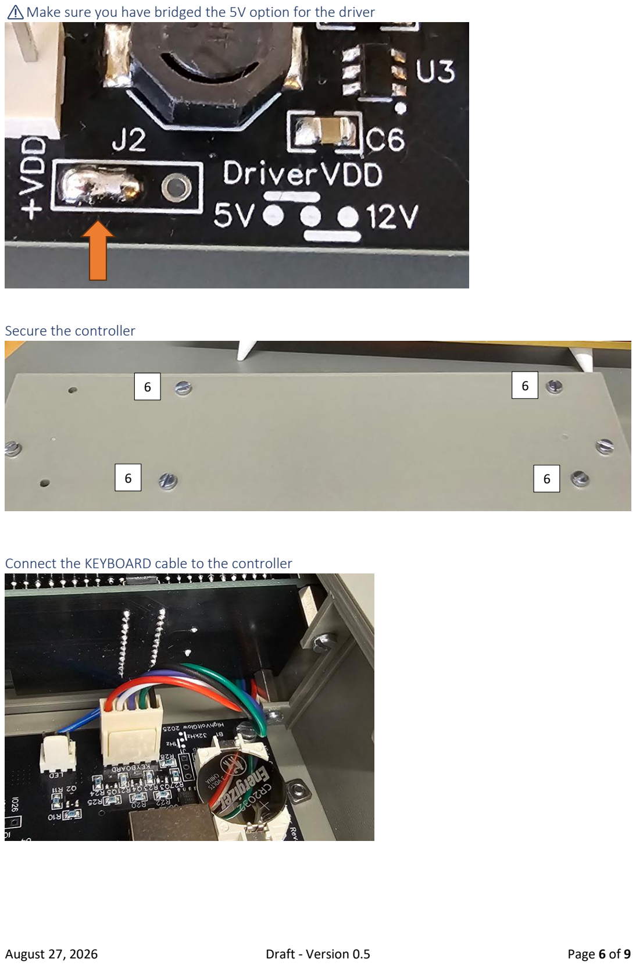
[picture p75: page 6]

⚠️Make sure you have bridged the 5V option for the driver

Secure the controller

Connect the KEYBOARD cable to the controller

6 | 6
6 | 6

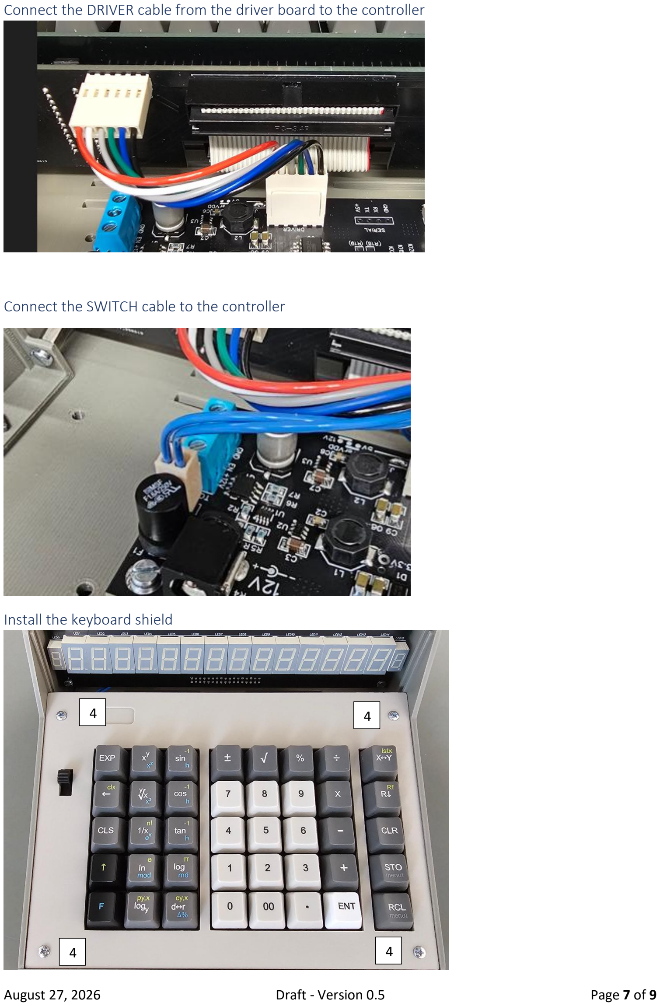
[picture p76: page 7]

Connect the DRIVER cable from the driver board to the controller

Connect the SWITCH cable to the controller

Install the keyboard shield

4 | 4
4 | 4

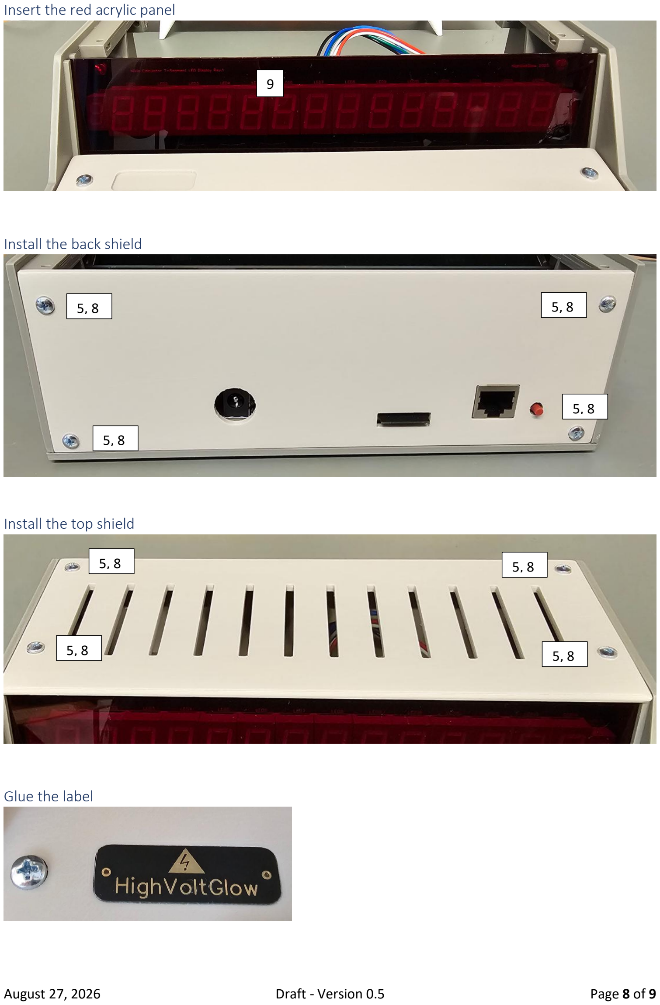
[picture p77: page 8]

Insert the red acrylic panel

Install the back shield

Install the top shield

Glue the label

5, 8 | 5, 8

5, 8

5, 8

5, 8 | 5, 8

5, 8 5, 8

9

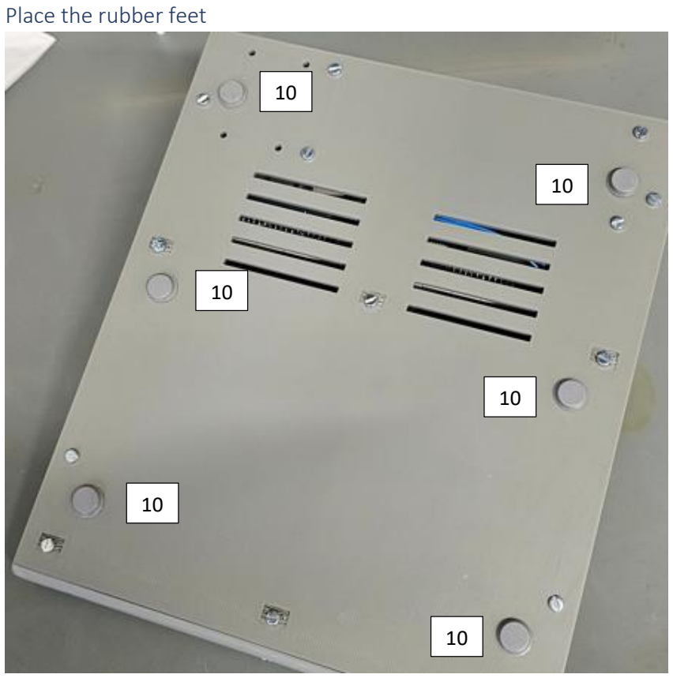
[picture p78: figure]
Place the rubber feet
