axtar/Nixie-Calculator/Docs/Assembling the PCBs.pdf

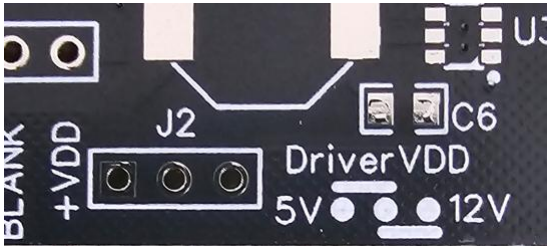
[picture p123: figure]

August 27, 2026 | Draft – Version 0.5 | Page 1 of 5

## Assembling the PCBs

### General information

Note: the pictures are only intended for a better understanding of the instructions and may not correspond to the latest hardware revision.

Since I cannot recommend this project for beginners, I will skip all the basic stuff and explain just a few things that might be of interest.

### Controller

Start assembling the input protection section including the LED and the fuse. Install a jumper on the SWITCH header. According to the datasheet the circuit should protect against overvoltage up to 60V and against reverse voltage down to -40V.

Connect the board to a variable power supply. Start with 12V - the LED should turn on. If you increase the voltage, the LED should turn off at around 13.5V. If you decrease the voltage, the LED should turn off at around 10V. These are only approximate values.

Then assemble the +3.3V and the +5V supplies and check that all voltages are correct.

Don’t populate the SERIAL, IOEX, J1 and J2 headers.

Select the VDD voltage for the display driver. For all nixie displays use a solder blob to connect the right pad to the middle pad of J2 (12V). For the 7-seg LED display connect the left pad to the middle pad of J2 (5V).

### Display and driver boards

IN-16 / B-5870 Versions
Please note that the B-5870 version also uses the IN-16 driver and the IN-16 display board.

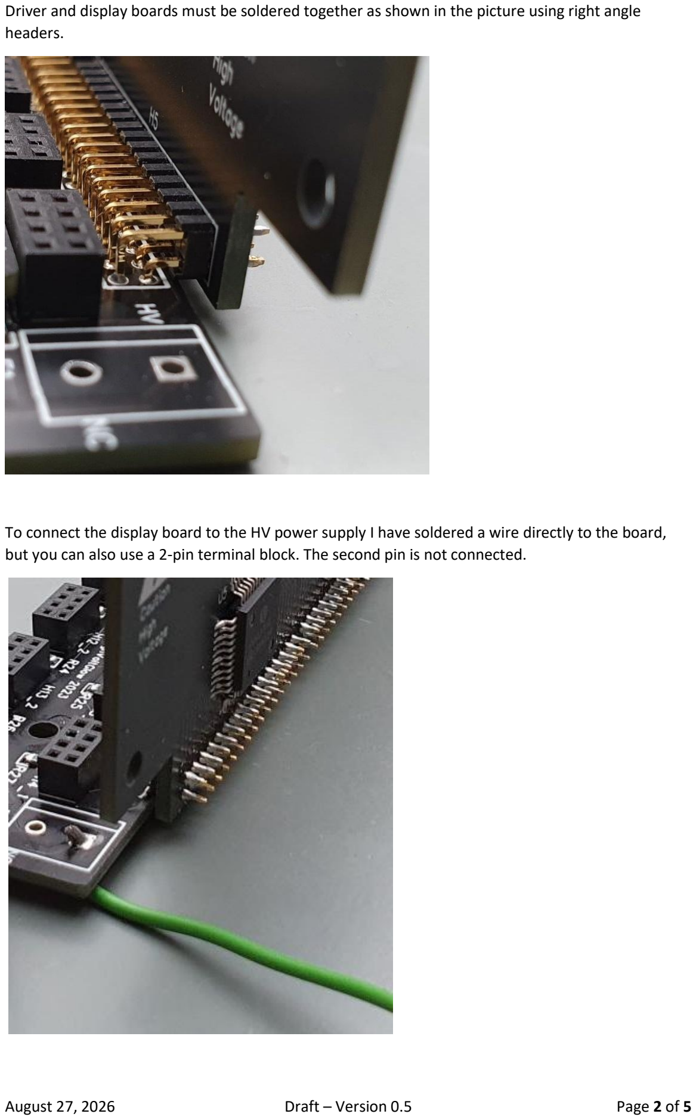
[picture p124: page 2]

Driver and display boards must be soldered together as shown in the picture using right angle headers.

To connect the display board to the HV power supply I have soldered a wire directly to the board, but you can also use a 2-pin terminal block. The second pin is not connected.

Use heat shrink tube (black recommended) for the neons (minus signs). I had to extend the wires a little bit to get the correct height.

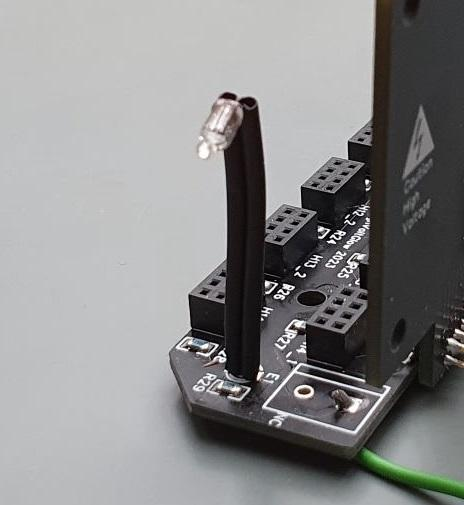
[picture p125: figure]

For the IN-16 version there are two options: LED backlighting or underlighting (recommended). For the B-5870 only backlighting is available.

For the IN-16 underlighting you must use the additional IN-16 LED board. Solder the 3-wire cable directly to the board. Use some black heat shrink tube to hide the cables behind the acrylic. Don’t populate the LEDs and the LED connector on the driver board.

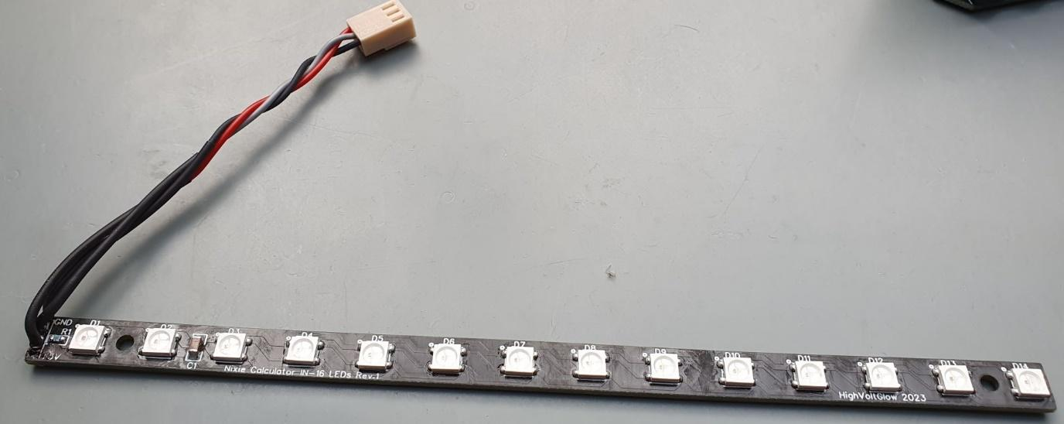
[picture p126: figure]
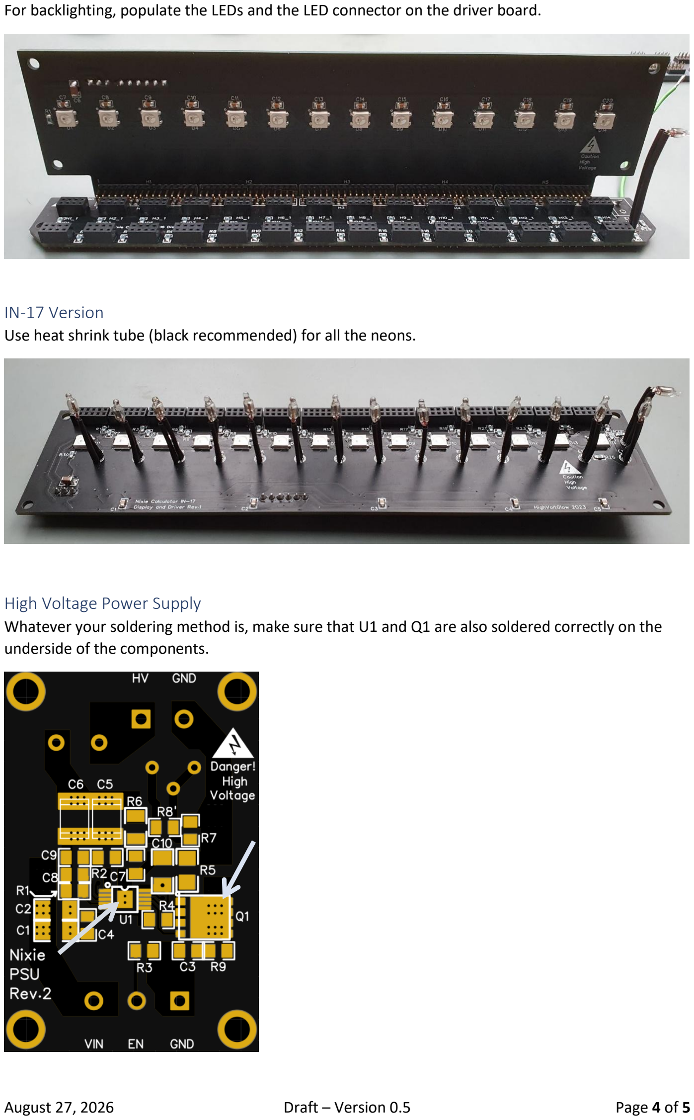
[picture p127: page 4]

For backlighting, populate the LEDs and the LED connector on the driver board.

IN-17 Version
Use heat shrink tube (black recommended) for all the neons.

High Voltage Power Supply
Whatever your soldering method is, make sure that U1 and Q1 are also soldered correctly on the underside of the components.

Peripherals module
Use heat shrink tube for the LED. Solder the cables directly to the board.

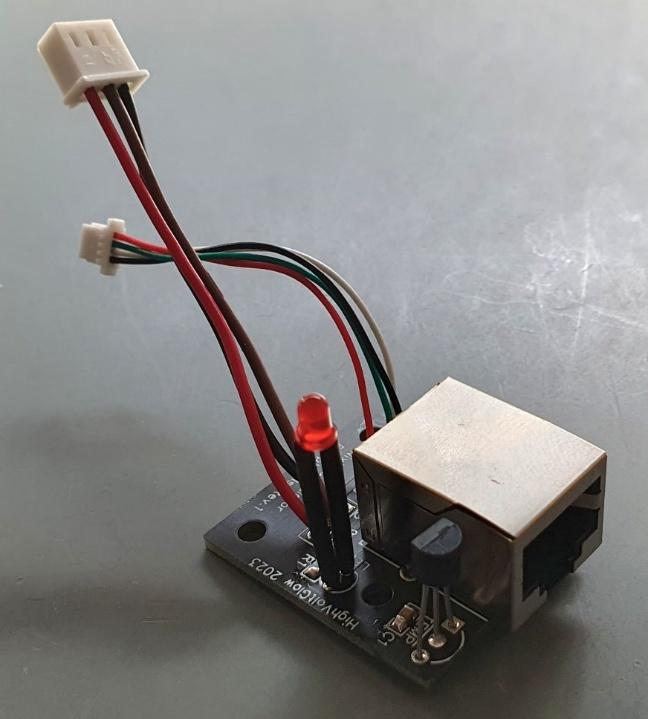
[picture p128: figure]
