axtar/Nixie-Calculator/Schematics/Schematic_Nixie_Calculator_IN-17_Display_and_Driver_Rev2.pdf

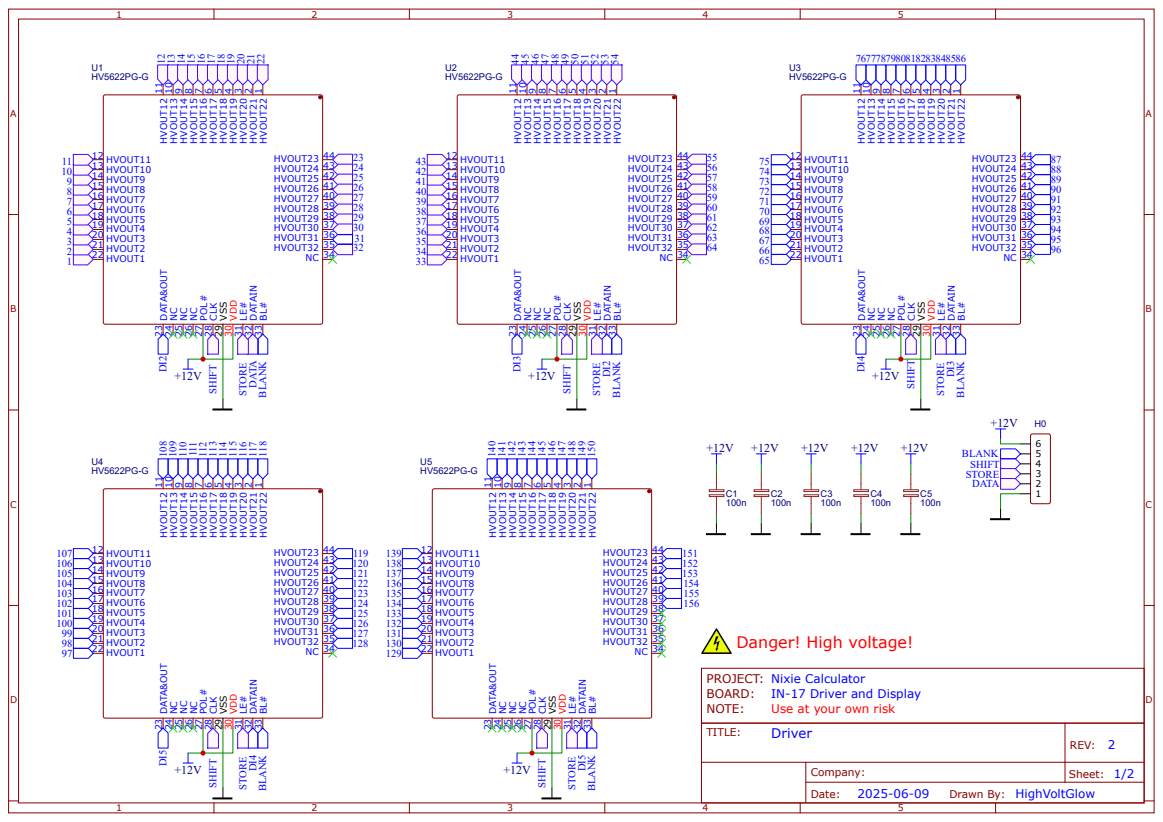
[picture p152: page 1]

PROJECT: Nixie Calculator
BOARD: IN-17 Driver and Display

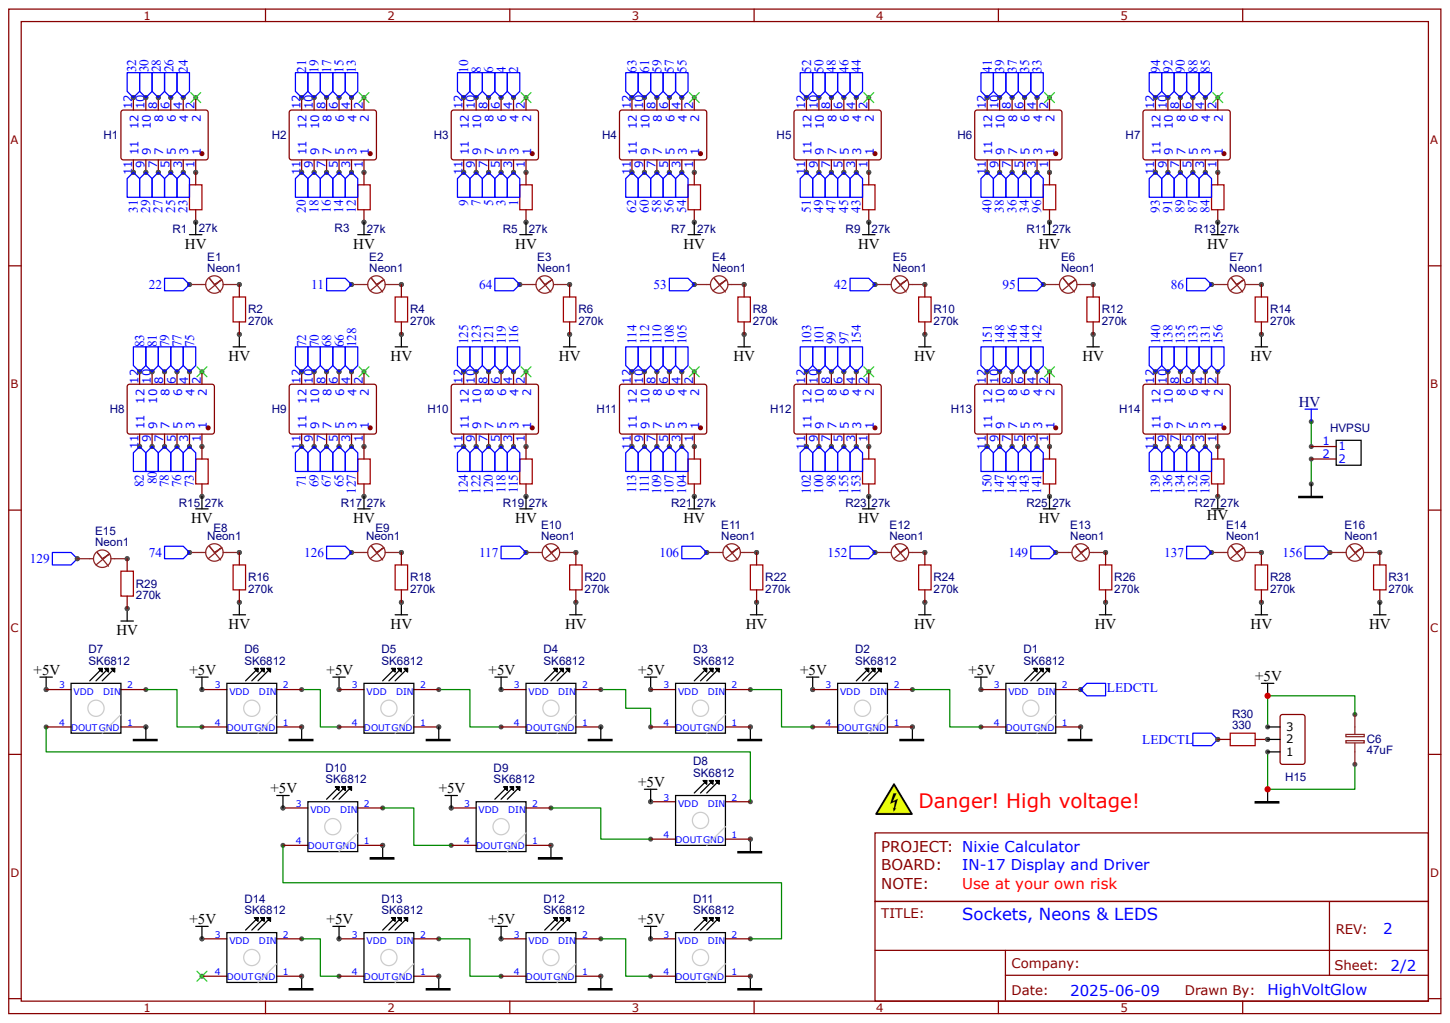
[picture p153: page 2]

PROJECT: Nixie Calculator
BOARD: IN-17 Display and Driver
