axtar/Nixie-Calculator/Schematics/Schematic_Nixie_Calculator_Peripherals_Rev2.pdf

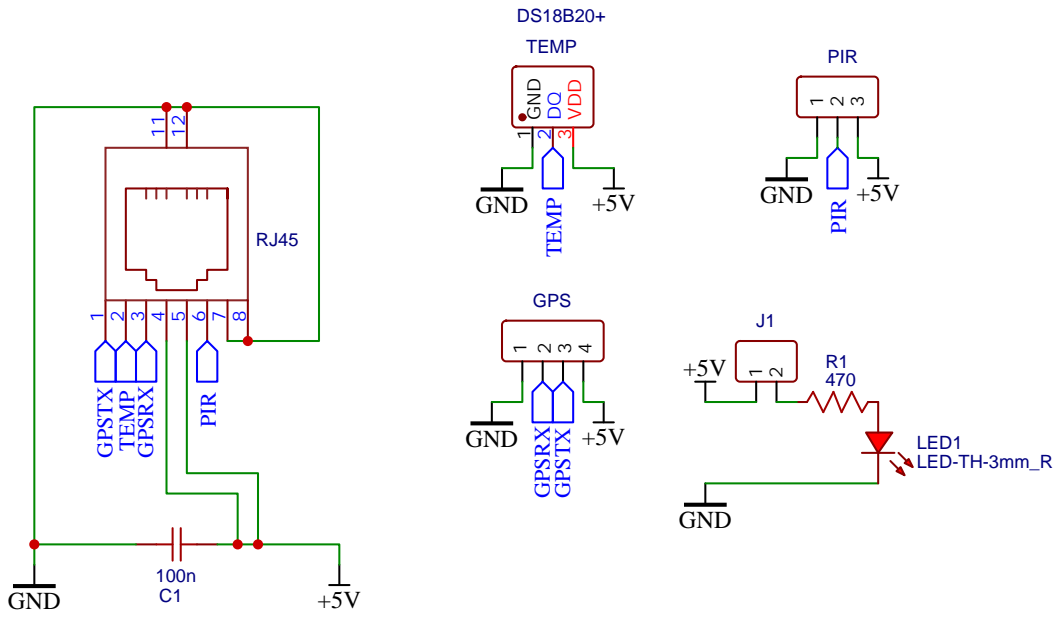
[picture p154: page 1]
TITLE:; Peripherals; REV: 2; Date:; Sheet: 1/1; Drawn By:; Company:; GND; DS18B20+ TEMP GND; VDD 3 TEMP; PIR; GPS; +5V GPSRX GPSTX; NOTE:; Use at your own risk; TEMP; GPSTX; GPSRX; PIR+5V; LED-TH-3mm_R; LED1; HighVoltGlow

PROJECT: Nixie Calculator
BOARD: Peripherals
