axtar/Nixie-Calculator/Schematics/Schematic_Nixie_Calculator_IN-16_Socket_Rev2.pdf

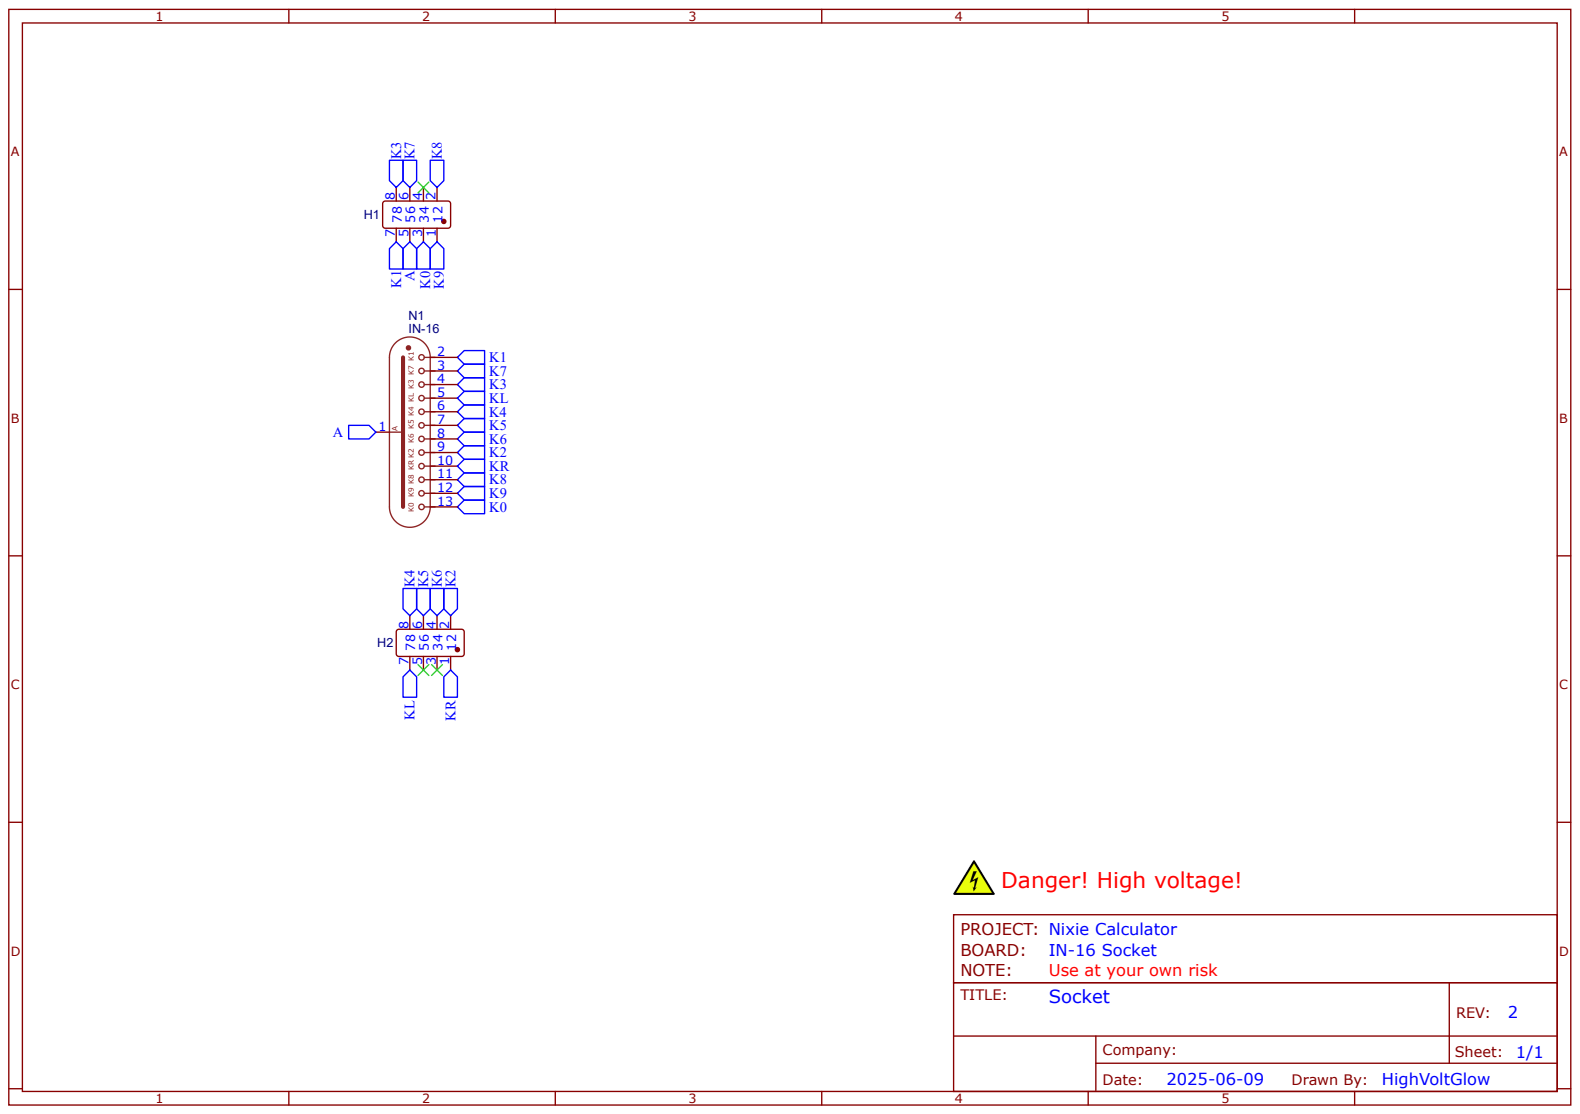
[picture p158: page 1]
TITLE:; REV: 2; Date:; Sheet:; awn By:; Company:; OAR; ris; T: Nixie; alc; ula; Hig; olt; Glo; r! Hig
