axtar/Nixie-Calculator/Schematics/Schematic_Nixie_Calculator_Keyboard_Rev2.pdf

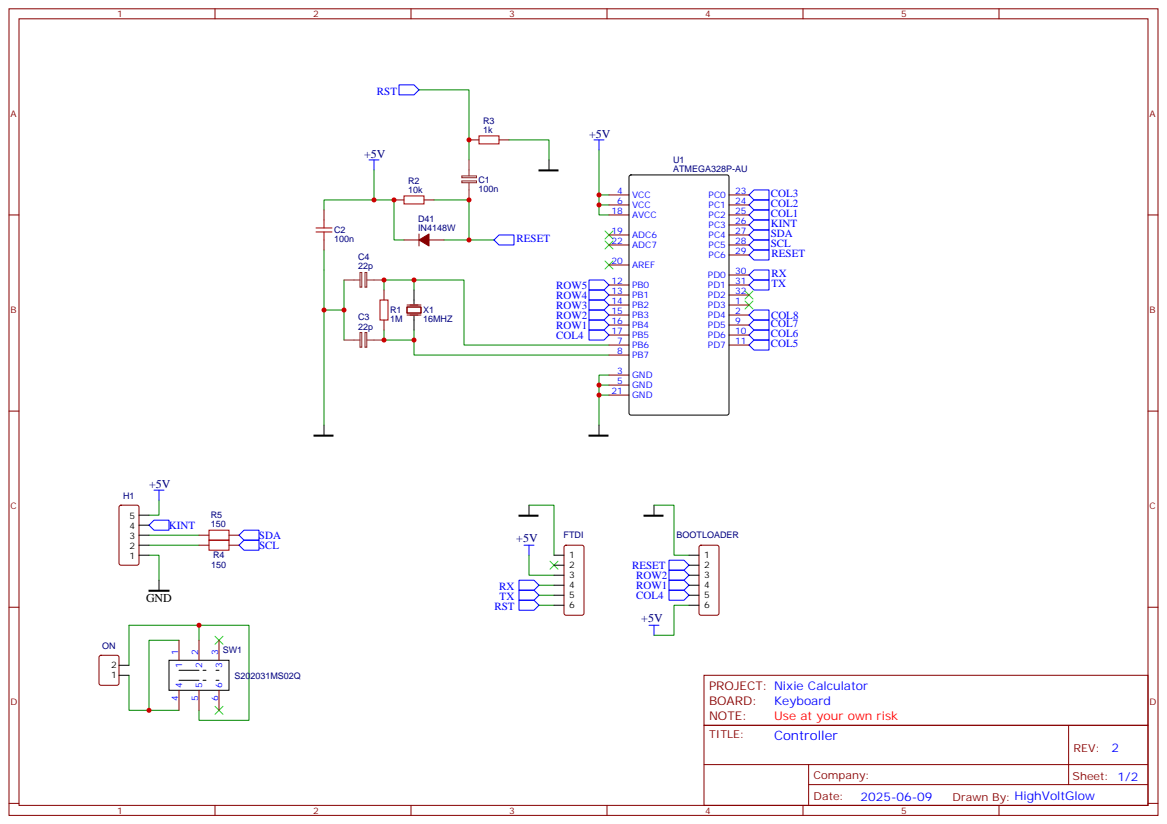
[picture p159: page 1]

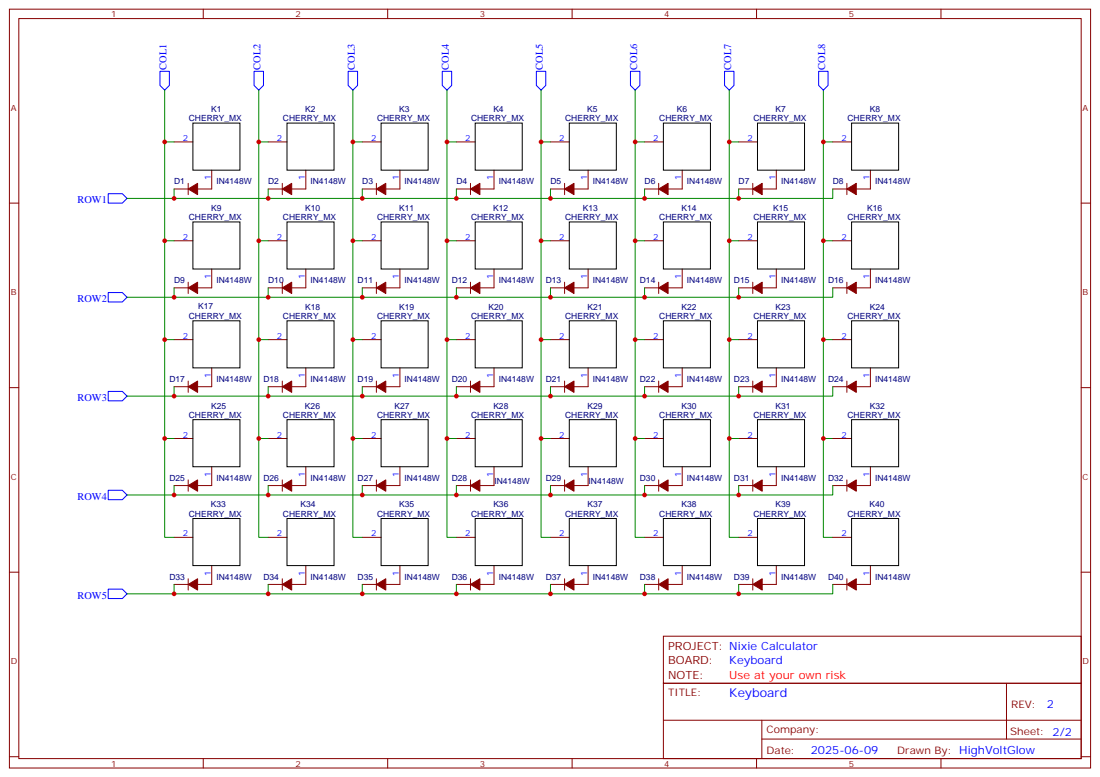
[picture p160: page 2]
