axtar/Nixie-Calculator/Schematics/Schematic_Nixie_Calculator_LED7SEG_Display_Rev1.pdf

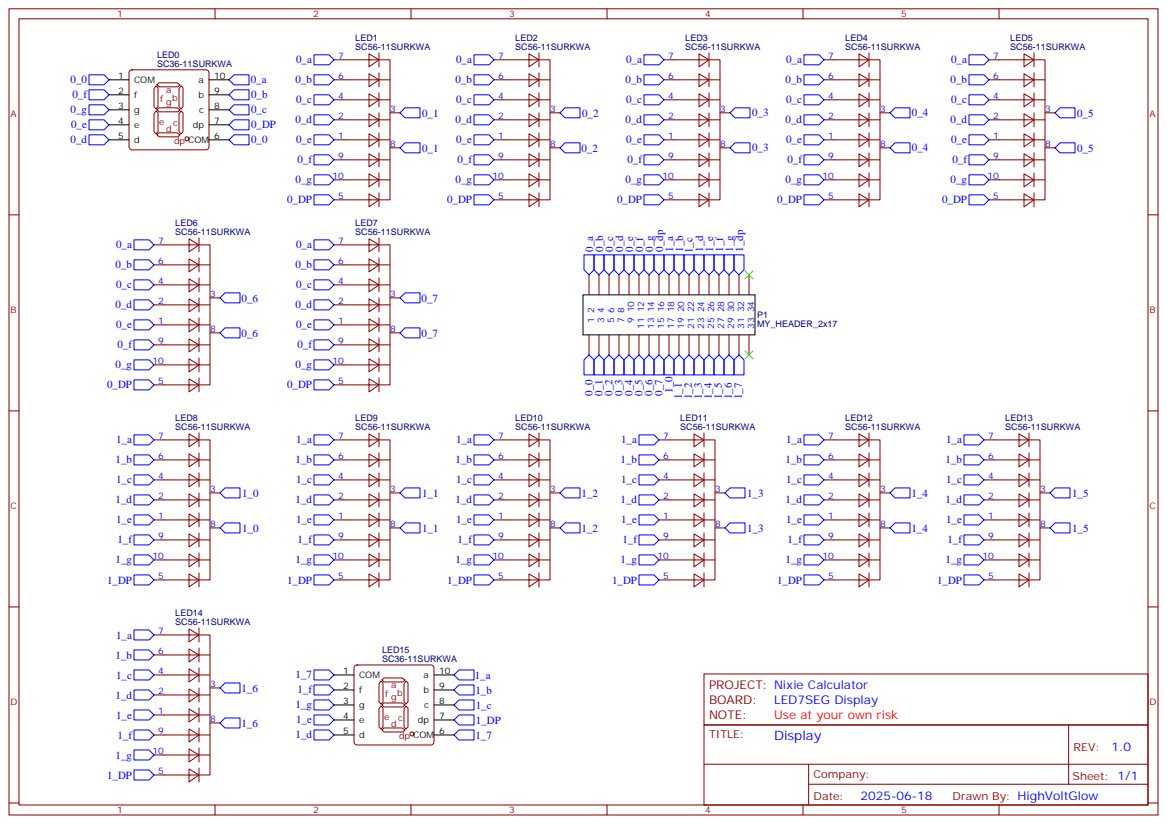
[picture p161: page 1]
