axtar/Nixie-Calculator/Schematics/Schematic_Nixie_Calculator_LED7SEG_Driver_Rev1.pdf

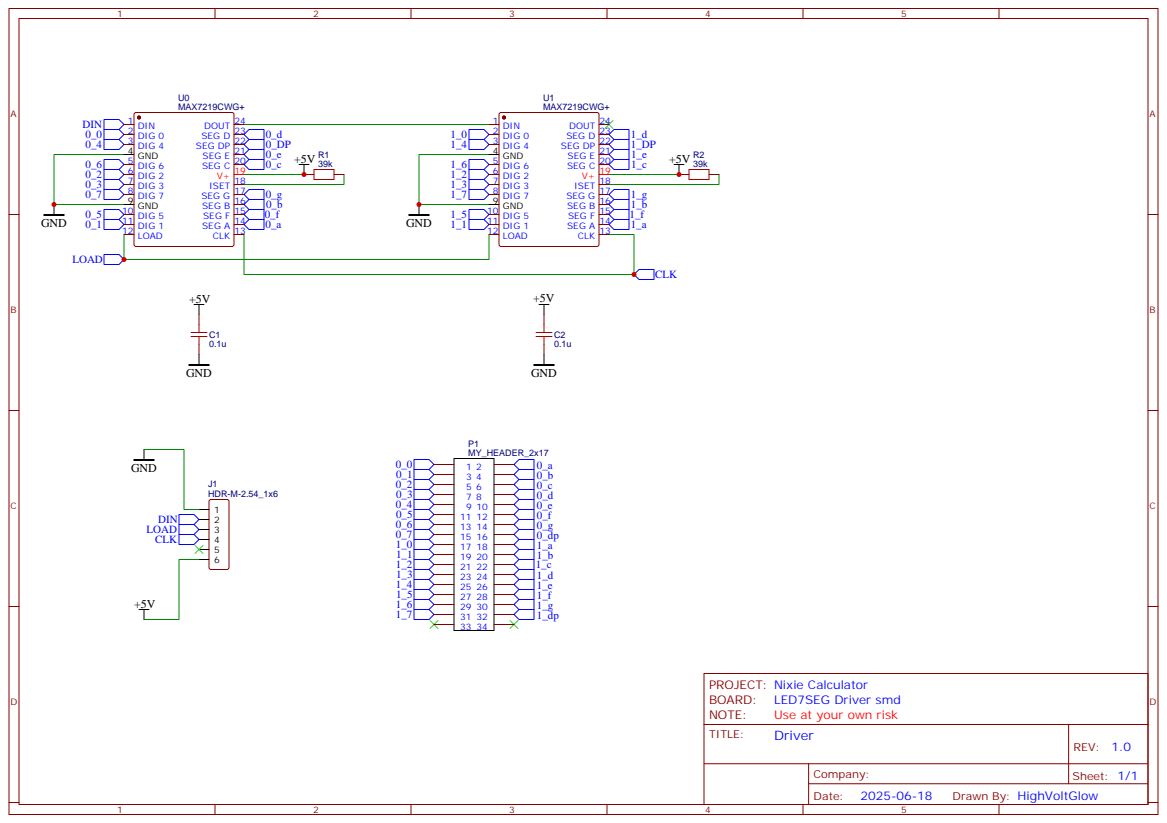
[picture p162: page 1]
