axtar/Nixie-Calculator/Firmware/Controller/main/Clock.hpp

// Clock.hpp

// provides clock mode functionality

// Copyright (C) 2020-2026 highvoltglow
// Licensed under the MIT License

#pragma once

#include <Arduino.h>
#include <time.h>
#include <sys/time.h>
#include <Timezone.hpp>
#include <RTC.hpp>
#include <DisplayHandler.hpp>
#include <Settings.hpp>
#include <SettingsCache.hpp>
#include <KeyboardHandler.hpp>
#include <KeyboardDecoder.hpp>
#include <SettingsCache.hpp>
#include <Temperature.hpp>

constexpr uint32_t MAX_TIMER_INPUT = 8;
constexpr unsigned long MAX_TIMER_INTERVAL = (99 * 86400) + (23 * 3600) + (59 * 60) + 59;
constexpr unsigned long TIMER_NOTIFY_ON_INTERVAL = 200;     // ms
constexpr unsigned long TIMER_NOTIFY_OFF_INTERVAL = 1000;   // ms
constexpr unsigned long TIME_SYNC_INTERVAL = 5 * 60 * 1000; // ms
constexpr time_t SECONDS_PER_MONTH = 30 * 86400;            // used to scale the RTC drift correction setting

enum class stopwatch_mode : uint8_t
{
  zero,
  stopped,
  running
};

enum class timer_mode : uint8_t
{
  zero,
  set,
  stopped,
  running
};

enum class input_mode : uint8_t
{
  none,
  time,
  timer
};

class Clock
{
public:
  Clock(DisplayHandler *displayHandler, Settings *settings)
      : _settings(settings),
        _displayHandler(displayHandler)
  {
    _timeZone = new Timezone(SettingsCache::dstRule, SettingsCache::stdRule);
    _timeZone2 = new Timezone(SettingsCache::dstRule2, SettingsCache::stdRule2);
    _stopwatchMode = stopwatch_mode::zero;
    _timerMode = timer_mode::zero;
    _inputMode = input_mode::none;
    _timerMode = timer_mode::zero;
    _refreshLighting = false;
    _temperature = TEMP_UNDEFINED;
    _showDateSecond = random(1, 55);
    _hourParamSet = false;
    _timerEnded = false;
    _timerNotifyOn = false;
  }

  virtual ~Clock()
  {
    delete (_timeZone);
    delete (_timeZone2);
  }

  // initialize the clock
  void begin()
  {
    setTimeZones();
    _rtc.begin();
    // seed the system clock from the RTC immediately
    syncTimeFromRTC(true);
  }

  // return the real-time clock object
  RTC *getRTC()
  {
    return (&_rtc);
  }

  // reload time zone rules from settings; call after settings are changed
  void setTimeZones()
  {
    _timeZone->defineRules(SettingsCache::dstRule, SettingsCache::stdRule);
    _timeZone2->defineRules(SettingsCache::dstRule2, SettingsCache::stdRule2);
  }

  // periodically re-sync the system clock from the RTC
  void syncTimeFromRTC(bool force = false)
  {
    if (force || millis() - _lastTimeSyncMillis > TIME_SYNC_INTERVAL)
    {
      time_t t = _rtc.get();
      if (t != 0)
      {
        t += driftCorrection(t);
        struct timeval tv = {.tv_sec = t, .tv_usec = 0};
        settimeofday(&tv, nullptr);
        _centiSecondStartUs = esp_timer_get_time();
      }
      _lastTimeSyncMillis = millis();
    }
  }

  // called from the main loop
  bool process(const struct tm *tm, const struct tm *tm2)
  {
    // set random show date second once an hour
    if (tm->tm_min == 0)
    {
      if (!_hourParamSet)
      {
        _showDateSecond = random(1, 55);
        _hourParamSet = true;
      }
    }
    else
    {
      _hourParamSet = false;
    }
    switch (_inputMode)
    {
    case input_mode::none:
      checkColorChangeTrigger(tm);
      displayTime(tm, tm2);
      break;

    default:
      showInput();
      break;
    }
    return (true);
  }

  // get if timer has ended
  bool getTimerEnded() const
  {
    return (_timerEnded);
  }

  // stop end of timer notification
  void resetTimerEnded()
  {
    _timerEnded = false;
  }

  // calculate remaining time and notify end of timer if timer ended
  void processTimer()
  {
    if (_timerMode == timer_mode::running)
    {
      _remainingMillis = (_timerSetMillis - _timerElapsedMillis) - ((esp_timer_get_time() / 1000LL) - _timerStartMillis);
      if (_remainingMillis <= 0)
      {
        _timerMode = timer_mode::zero;
        _remainingMillis = 0;
        _timerEnded = true;
      }
    }
    if (_timerEnded || _timerNotifyOn)
    {
      if (SettingsCache::notifyTimer == notify_timer::on || _timerNotifyOn)
      {
        notifyTimer();
      }
    }
  }

  // notify end of timer
  void notifyTimer()
  {
    if (_timerNotifyOn)
    {
      // check if it's time to set notification off
      if (millis() - _timerNotifyChangeMillis > TIMER_NOTIFY_ON_INTERVAL)
      {
        _displayHandler->restoreLEDColors();
        _displayHandler->updateLEDs();
        _timerNotifyOn = false;
        _timerNotifyChangeMillis = millis();
      }
    }
    else
    {
      if (millis() - _timerNotifyChangeMillis > TIMER_NOTIFY_OFF_INTERVAL)
      {
        _displayHandler->saveLEDColors();
        _displayHandler->setAllLED(SettingsCache::timerColor.red, SettingsCache::timerColor.green, SettingsCache::timerColor.blue);
        _displayHandler->updateLEDs();
        _timerNotifyOn = true;
        _timerNotifyChangeMillis = millis();
      }
    }
  }

  // the temperature is displayed in some clock modes
  void setTemperature(float temperature)
  {
    _temperature = temperature;
  }

  // update the RTC time
  void setSystemAndRTCTime(time_t utc, bool updateDriftReference = true)
  {
    struct timeval tv = {.tv_sec = utc, .tv_usec = 0};
    settimeofday(&tv, nullptr);
    _rtc.set(utc);
    if (updateDriftReference)
    {
      // remember when the RTC was deliberately set, used as the reference point for drift correction
      _settings->setRtcRefEpoch(utc);
    }
  }

  // get the temperature of the RTC IC
  float getBoardTemperature()
  {
    return (static_cast<float>(_rtc.temperature() / 4.0f));
  }

  // called if a key has been pressed
  void onKeyboardEvent(uint8_t keyCode, key_state keyState, bool functionKeyPressed, bool shiftKeyPressed)
  {

    operation op;
    uint8_t digit;
    key_function_type function;

    if (keyState == key_state::pressed)
    {
      KeyboardDecoder::decode(keyCode, functionKeyPressed, shiftKeyPressed, &function, &op, &digit);

      switch (function)
      {
      case key_function_type::numeric:
        numericInput(digit);
        break;

      case key_function_type::numericx2:
        if (_inputMode == input_mode::none)
        {
          numericInput(clock_mode::stopwatch);
        }
        else
        {
          numericInput(digit);
          numericInput(digit);
        }
        break;

      case key_function_type::control:
      case key_function_type::operation:
        operationInput(op);
        break;

      default: // avoid warning
        break;
      }
    }
  }

  // return current time
  void getCurrentTime(struct tm *tm, struct tm *tm2) const
  {
    time_t utc, local;
    utc = time(nullptr);
    // convert to local time
    local = _timeZone->toLocal(utc);
    // to time elements
    gmtime_r(&local, tm);
    // convert to dual time
    local = _timeZone2->toLocal(utc);
    // to time elements
    gmtime_r(&local, tm2);
  }

  // adjust time by +/- seconds
  void adjustTime(int seconds)
  {
    time_t t = _rtc.get() + seconds;
    setSystemAndRTCTime(t);
  }

  // return the value of the refresh lighting flag
  bool getRefreshLighting() const
  {
    return (_refreshLighting);
  }

  // reset the refresh lighting flag
  void resetRefreshLighting()
  {
    _refreshLighting = false;
  }

private:
  RTC _rtc;
  Settings *_settings;
  Timezone *_timeZone;
  Timezone *_timeZone2; // time zone for dual time
  DisplayHandler *_displayHandler;
  String _display;
  stopwatch_mode _stopwatchMode;
  timer_mode _timerMode;
  input_mode _inputMode;
  float _temperature;
  bool _refreshLighting;
  long _showDateSecond;
  bool _hourParamSet;
  unsigned long _lastTimeSyncMillis = 0;
  bool _timerEnded;
  bool _timerNotifyOn;
  int _lastColorChangeSecond = -1;
  int _lastColorChangeMinute = -1;
  int _lastColorChangeHour = -1;
  int _lastTimerColorSecond = -1;
  int _lastTimerColorMinute = -1;
  int _lastTimerColorHour = -1;
  int _lastStopwatchColorSecond = -1;
  int _lastStopwatchColorMinute = -1;
  int _lastStopwatchColorHour = -1;
  int _centiLastSecond = -1;
  int64_t _centiSecondStartUs = 0;

  // some state variables
  int _movingLastSecond = 0;
  bool _movingLeftDirection = true;
  int _movingPosition = 3;
  bool _scrollingIsDate = false;
  int _scrollingTimePosition = 2;
  int _scrollingDatePosition = 13;
  unsigned long _scrollingLastMillis = millis();
  uint64_t _swStartMillis = 0;
  uint64_t _swElapsedMillis = 0;
  bool _swRunning = false;
  unsigned long _inputLastMillis = millis();
  bool _inputShow = true;
  int64_t _timerSetMillis = 0;
  int64_t _timerStartMillis = 0;
  int64_t _timerElapsedMillis = 0;
  int64_t _remainingMillis = 0;
  unsigned long _timerNotifyChangeMillis = 0;

  // compute the drift correction, in seconds, to apply to an RTC reading
  time_t driftCorrection(time_t rtcNow) const
  {
    if (SettingsCache::rtcDriftCorr == 0)
    {
      return (0);
    }
    time_t refEpoch = _settings->getRtcRefEpoch();
    if ((refEpoch == 0) || (rtcNow <= refEpoch))
    {
      return (0);
    }
    time_t elapsed = rtcNow - refEpoch;
    return (static_cast<time_t>((static_cast<int64_t>(SettingsCache::rtcDriftCorr) * static_cast<int64_t>(elapsed)) / SECONDS_PER_MONTH));
  }

  // set the time from user input
  void setTimeFromInput()
  {
    time_t local, utc;
    struct tm tm = {};

    if (_display.length() == _displayHandler->getDigitCount())
    {
      int temp = 0;
      temp = _display.substring(0, 4).toInt();
      tm.tm_year = temp - 1900;
      temp = _display.substring(4, 6).toInt();
      tm.tm_mon = temp - 1;
      temp = _display.substring(6, 8).toInt();
      tm.tm_mday = temp;
      temp = _display.substring(8, 10).toInt();
      tm.tm_hour = temp;
      temp = _display.substring(10, 12).toInt();
      tm.tm_min = temp;
      temp = _display.substring(12, 14).toInt();
      tm.tm_sec = temp;
      local = timegmCompat(&tm);
      // convert user input to UTC
      utc = _timeZone->toUTC(local);
      // set time
      setSystemAndRTCTime(utc);
    }
  }

  // true if a color-change trigger should fire at all right now
  bool colorChangeTriggerActive() const
  {
    if (SettingsCache::trigColorChange == trig_color_change::off)
    {
      return false;
    }

    switch (SettingsCache::clockRGBMode)
    {
    case clock_rgb_mode::random_on_only:
    case clock_rgb_mode::full_random_on_only:
    case clock_rgb_mode::random_all:
    case clock_rgb_mode::full_random_all:
      return true;

    default:
      return false;
    }
  }

  // trigger a lighting refresh when a random RGB mode is active
  void checkColorChangeTrigger(const struct tm *tm)
  {
    if (!colorChangeTriggerActive())
    {
      return;
    }

    switch (SettingsCache::clockMode)
    {
    case clock_mode::time:
    case clock_mode::time_no_seconds:
    case clock_mode::time_or_date:
    case clock_mode::time_and_date:
    case clock_mode::time_and_temp:
    case clock_mode::time_and_date_and_temp:
    case clock_mode::time_centiseconds:
    case clock_mode::date_and_time_raw:
    case clock_mode::dual_time:
      break;

    default:
      return;
    }

    if (SettingsCache::trigColorChange == trig_color_change::every_second)
    {
      if (tm->tm_sec != _lastColorChangeSecond)
      {
        _lastColorChangeSecond = tm->tm_sec;
        _refreshLighting = true;
      }
    }
    else if (SettingsCache::trigColorChange == trig_color_change::every_minute)
    {
      if (tm->tm_min != _lastColorChangeMinute)
      {
        _lastColorChangeMinute = tm->tm_min;
        _refreshLighting = true;
      }
    }
    else if (SettingsCache::trigColorChange == trig_color_change::every_hour)
    {
      if (tm->tm_hour != _lastColorChangeHour)
      {
        _lastColorChangeHour = tm->tm_hour;
        _refreshLighting = true;
      }
    }
  }

  // trigger on elapsed second/minute/hour boundaries used by timer and stopwatch,
  void checkElapsedColorChangeTrigger(bool isRunning, unsigned long second, unsigned long minute, unsigned long hour,
                                      int &lastSecond, int &lastMinute, int &lastHour)
  {
    if (!isRunning || !colorChangeTriggerActive())
    {
      return;
    }

    if (SettingsCache::trigColorChange == trig_color_change::every_second)
    {
      if (static_cast<int>(second) != lastSecond)
      {
        lastSecond = second;
        _refreshLighting = true;
      }
    }
    else if (SettingsCache::trigColorChange == trig_color_change::every_minute)
    {
      if (static_cast<int>(minute) != lastMinute)
      {
        lastMinute = minute;
        _refreshLighting = true;
      }
    }
    else if (SettingsCache::trigColorChange == trig_color_change::every_hour)
    {
      if (static_cast<int>(hour) != lastHour)
      {
        lastHour = hour;
        _refreshLighting = true;
      }
    }
  }

  // display the time according to the selected clock mode
  void displayTime(const struct tm *tm, const struct tm *tm2)
  {
    switch (SettingsCache::clockMode)
    {
    case clock_mode::time:
      showTimeDefault(tm);
      break;

    case clock_mode::time_no_seconds:
      showTimeNoSeconds(tm);
      break;

    case clock_mode::time_moving:
      showMovingTime(tm);
      break;

    case clock_mode::time_or_date:
      showDateOrTime(tm);
      break;

    case clock_mode::time_and_date:
      showTimeAndDate(tm);
      break;

    case clock_mode::time_and_temp:
      showTimeAndTemp(tm);
      break;

    case clock_mode::time_and_date_and_temp:
      showTimeAndDateAndTemp(tm);
      break;

    case clock_mode::time_centiseconds:
      showTimeCentiseconds(tm);
      break;

    case clock_mode::date_and_time_raw:
      showDateTimeRaw(tm);
      break;

    case clock_mode::dual_time:
      showDualTime(tm, tm2);
      break;

    case clock_mode::timer:
      showTimer();
      break;

    case clock_mode::stopwatch:
      showStopWatch();
      break;
    }
  }

  // display the time, clock mode 0 = time
  void showTimeDefault(const struct tm *tm) const
  {
    _displayHandler->showTime(tm, 3, SettingsCache::hourMode, SettingsCache::leadingZero, true, true, SettingsCache::timeSeparator);
  }

  // display the time, clock mode 1 = time, no seconds
  void showTimeNoSeconds(const struct tm *tm) const
  {
    _displayHandler->showTime(tm, 4, SettingsCache::hourMode, SettingsCache::leadingZero, false, true, SettingsCache::timeSeparator);
  }

  // display the time, clock mode 2
  void showMovingTime(const struct tm *tm)
  {
    // relative offsets showTime() writes with showSeconds=true, space=true (+2/+5 are ":" gaps)
    constexpr uint8_t MOVING_TIME_OFFSETS[6] = {0, 1, 3, 4, 6, 7};

    if (tm->tm_sec != _movingLastSecond)
    {
      int oldPosition = _movingPosition;
      _refreshLighting = true;
      _movingLastSecond = tm->tm_sec;
      if (_movingLeftDirection)
      {
        if (_movingPosition == 6)
        {
          _movingLeftDirection = false;
          _movingPosition--;
        }
        else
        {
          _movingPosition++;
        }
      }
      else
      {
        int final = 0;
        if ((SettingsCache::leadingZero == leading_zero::off) && ((tm->tm_hour) / 10 == 0))
        {
          final = (-1);
        }

        if (_movingPosition == final)
        {
          _movingLeftDirection = true;
          _movingPosition++;
        }
        else
        {
          _movingPosition--;
        }
      }

      // blank every tube written in the old window but not in the new one, so nothing lingers
      for (uint8_t offset : MOVING_TIME_OFFSETS)
      {
        int oldPos = oldPosition + offset;
        bool stillUsed = false;
        for (uint8_t newOffset : MOVING_TIME_OFFSETS)
        {
          if (_movingPosition + newOffset == oldPos)
          {
            stillUsed = true;
            break;
          }
        }
        if (!stillUsed && (oldPos >= 0) && (oldPos < _displayHandler->getDigitCount()))
        {
          _displayHandler->setDigit(oldPos, DIGIT_OFF);
        }
      }
    }
    _displayHandler->showTime(tm, _movingPosition, SettingsCache::hourMode, SettingsCache::leadingZero, true, true, SettingsCache::timeSeparator);
  }

  // display date or time, clock mode 3
  void showDateOrTime(const struct tm *tm)
  {
    if ((tm->tm_sec > _showDateSecond) && (tm->tm_sec < _showDateSecond + 5))
    {
      if (!_scrollingIsDate)
      {
        if (millis() - _scrollingLastMillis > 75)
        {
          _displayHandler->clearDisplay();
          _displayHandler->showTime(tm, _scrollingTimePosition, SettingsCache::hourMode, SettingsCache::leadingZero, true, true, SettingsCache::timeSeparator);
          _displayHandler->showDate(tm, _scrollingDatePosition, SettingsCache::dateFormat, year_type::full, true);
          _displayHandler->show();
          _scrollingTimePosition--;
          _scrollingDatePosition--;
          _refreshLighting = true;
          if (_scrollingDatePosition == (1))
          {
            _scrollingIsDate = true;
            _scrollingTimePosition = -9;
            _scrollingDatePosition = 3;
            _refreshLighting = true;
          }
          _scrollingLastMillis = millis();
        }
      }
    }
    else
    {
      if (_scrollingIsDate)
      {
        if (millis() - _scrollingLastMillis > 75)
        {
          _displayHandler->clearDisplay();
          _displayHandler->showDate(tm, _scrollingDatePosition, SettingsCache::dateFormat, year_type::full, true);
          _displayHandler->showTime(tm, _scrollingTimePosition, SettingsCache::hourMode, SettingsCache::leadingZero, true, true, SettingsCache::timeSeparator);
          _displayHandler->show();
          _scrollingDatePosition++;
          _scrollingTimePosition++;
          _refreshLighting = true;
          if (_scrollingTimePosition == 3)
          {
            _refreshLighting = true;
            _scrollingIsDate = false;
            _scrollingTimePosition = 2;
            _scrollingDatePosition = 13;
          }
          _scrollingLastMillis = millis();
        }
      }
      else
      {
        // clean up if no time to full scroll date
        if (_scrollingLastMillis != 2)
        {
          _scrollingLastMillis = 2;
          _displayHandler->clearDisplay();
          _refreshLighting = true;
        }
        _displayHandler->showTime(tm, 3, SettingsCache::hourMode, SettingsCache::leadingZero, true, true, SettingsCache::timeSeparator);
      }
    }
  }

  // display date and time, clock mode 4
  void showTimeAndDate(const struct tm *tm) const
  {
    _displayHandler->showTime(tm, 0, SettingsCache::hourMode, SettingsCache::leadingZero, true, false, SettingsCache::timeSeparator);
    _displayHandler->showDate(tm, 8, SettingsCache::dateFormat, year_type::partial, false);
  }

  // display time and temperature, clock mode 5
  void showTimeAndTemp(const struct tm *tm)
  {
    _displayHandler->showTime(tm, 0, SettingsCache::hourMode, SettingsCache::leadingZero, true, true, SettingsCache::timeSeparator);
    showTemp(11);
  }

  // display time, date and temperature, clock mode 6
  void showTimeAndDateAndTemp(const struct tm *tm)
  {
    _displayHandler->showTime(tm, 0, SettingsCache::hourMode, SettingsCache::leadingZero, false, false, SettingsCache::timeSeparator);
    _displayHandler->showDate(tm, 5, SettingsCache::dateFormat, year_type::none, false);
    showTemp(11);
  }

  // display the temperature
  void showTemp(uint8_t position)
  {
    digit_content content = _displayHandler->getDigitContent(11);
    if (_temperature != TEMP_UNDEFINED)
    {
      if (content != digit_content::temp)
      {
        _refreshLighting = true;
      }
      _displayHandler->showTemperature(position, _temperature);
    }
    else
    {
      if (content == digit_content::temp)
      {
        _refreshLighting = true;
      }
      _displayHandler->clearTemperature(position);
    }
  }

  // display the time with hundredths of a second
  void showTimeCentiseconds(const struct tm *tm)
  {
    int64_t nowUs = esp_timer_get_time();
    if (tm->tm_sec != _centiLastSecond)
    {
      _centiLastSecond = tm->tm_sec;
      _centiSecondStartUs = nowUs;
    }
    int64_t hundredths = (nowUs - _centiSecondStartUs) / 10000;
    if (hundredths > 99)
    {
      // the next second is late, hold at 99
      hundredths = 99;
    }
    _displayHandler->showTime(tm, 1, SettingsCache::hourMode, SettingsCache::leadingZero, true, true, SettingsCache::timeSeparator);
    _displayHandler->setDigit(10, hundredths / 10, digit_content::time);
    _displayHandler->setDigit(11, hundredths % 10, digit_content::time);
  }

  // display date and time in the format YYYYMMDDhhmmss
  void showDateTimeRaw(const struct tm *tm) const
  {
    int year = tm->tm_year + 1900;
    int month = tm->tm_mon + 1;
    uint8_t day10 = tm->tm_mday / 10;
    uint8_t day01 = tm->tm_mday % 10;
    uint8_t month10 = month / 10;
    uint8_t month01 = month % 10;
    uint8_t year0001 = year % 10;
    year /= 10;
    uint8_t year0010 = year % 10;
    year /= 10;
    uint8_t year0100 = year % 10;
    uint8_t year1000 = year / 10;
    uint8_t seconds10 = tm->tm_sec / 10;
    uint8_t seconds01 = tm->tm_sec % 10;
    uint8_t minutes10 = tm->tm_min / 10;
    uint8_t minutes01 = tm->tm_min % 10;
    uint8_t hours10 = tm->tm_hour / 10;
    uint8_t hours01 = tm->tm_hour % 10;
    _displayHandler->setDigit(0, year1000, digit_content::date);
    _displayHandler->setDigit(1, year0100, digit_content::date);
    _displayHandler->setDigit(2, year0010, digit_content::date);
    _displayHandler->setDigit(3, year0001, digit_content::date);
    _displayHandler->setDigit(4, month10, digit_content::date);
    _displayHandler->setDigit(5, month01, digit_content::date);
    _displayHandler->setDigit(6, day10, digit_content::date);
    _displayHandler->setDigit(7, day01, digit_content::date);
    _displayHandler->setDigit(8, hours10, digit_content::time);
    _displayHandler->setDigit(9, hours01, digit_content::time);
    _displayHandler->setDigit(10, minutes10, digit_content::time);
    _displayHandler->setDigit(11, minutes01, digit_content::time);
    _displayHandler->setDigit(12, seconds10, digit_content::time);
    _displayHandler->setDigit(13, seconds01, digit_content::time);
  }

  // display local and dual time, clock mode 8
  void showDualTime(const struct tm *tm, const struct tm *tm2) const
  {
    _displayHandler->showTime(tm, 0, SettingsCache::hourMode, SettingsCache::leadingZero, true, false, SettingsCache::timeSeparator);
    _displayHandler->showTime(tm2, 8, SettingsCache::hourMode, SettingsCache::leadingZero, true, false, SettingsCache::timeSeparator, true);
  }

  // display the timer, clock mode 9
  void showTimer()
  {
    uint8_t position = 1;

    switch (_timerMode)
    {
    case timer_mode::set:
      _remainingMillis = _timerSetMillis;
      _timerElapsedMillis = 0;
      break;

    case timer_mode::zero:
      _remainingMillis = 0;
      break;

    case timer_mode::running:
      // do nothing
      break;

    case timer_mode::stopped:
      _remainingMillis = _timerSetMillis - _timerElapsedMillis;
      break;
    }

    unsigned long ts = (_remainingMillis / 1000) % 60;
    unsigned long tm = (_remainingMillis / 60000) % 60;
    unsigned long th = (_remainingMillis / 3600000) % 24;
    unsigned long td = (_remainingMillis / 86400000) % 100;

    _displayHandler->setDigit(position + 0, td / 10, digit_content::time);
    _displayHandler->setDigit(position + 1, td % 10, digit_content::time);
    _displayHandler->setDigit(position + 3, th / 10, digit_content::time);
    _displayHandler->setDigit(position + 4, th % 10, digit_content::time);
    _displayHandler->setDigit(position + 6, tm / 10, digit_content::time);
    _displayHandler->setDigit(position + 7, tm % 10, digit_content::time);
    _displayHandler->setDigit(position + 9, ts / 10, digit_content::time);
    _displayHandler->setDigit(position + 10, ts % 10, digit_content::time);

    checkElapsedColorChangeTrigger(_timerMode == timer_mode::running, ts, tm, th,
                                   _lastTimerColorSecond, _lastTimerColorMinute, _lastTimerColorHour);
  }

  // display the stopwatch
  void showStopWatch()
  {
    int position = 1;

    switch (_stopwatchMode)
    {
    case stopwatch_mode::zero:
      _swElapsedMillis = 0;
      _swStartMillis = 0;
      _swRunning = false;
      break;

    case stopwatch_mode::running:
      if (_swRunning)
      {
        _swElapsedMillis = (esp_timer_get_time() / 1000ULL) - _swStartMillis;
      }
      else
      {
        _swRunning = true;
        if (_swStartMillis == 0)
        {
          _swStartMillis = (esp_timer_get_time() / 1000ULL);
          _swElapsedMillis = 0;
        }
      }
      break;

    case stopwatch_mode::stopped:
      if (_swRunning)
      {
        _swRunning = false;
        _swElapsedMillis = (esp_timer_get_time() / 1000ULL) - _swStartMillis;
      }
      break;
    }

    // show elapsed
    unsigned long tc = _swElapsedMillis % 1000;
    unsigned long ts = (_swElapsedMillis / 1000) % 60;
    unsigned long tm = (_swElapsedMillis / 60000) % 60;
    unsigned long th = (_swElapsedMillis / 3600000) % 24;

    _displayHandler->setDigit(position, th / 10, digit_content::time);
    _displayHandler->setDigit(position + 1, th % 10, digit_content::time);
    _displayHandler->setDigit(position + 3, tm / 10, digit_content::time);
    _displayHandler->setDigit(position + 4, tm % 10, digit_content::time);
    _displayHandler->setDigit(position + 6, ts / 10, digit_content::time);
    _displayHandler->setDigit(position + 7, ts % 10, digit_content::time);
    _displayHandler->setDigit(position + 9, (tc / 10) / 10, digit_content::time);
    _displayHandler->setDigit(position + 10, (tc / 10) % 10, digit_content::time);

    checkElapsedColorChangeTrigger(_swRunning, ts, tm, th,
                                   _lastStopwatchColorSecond, _lastStopwatchColorMinute, _lastStopwatchColorHour);
  }

  // display blinking user input for the timer
  void showInput()
  {
    if (SettingsCache::inputBlinking == input_blinking::on)
    {
      if (millis() - _inputLastMillis > 250)
      {
        _inputShow = !_inputShow;
        _inputLastMillis = millis();
      }
      if (_inputShow)
      {
        _displayHandler->show(_display);
      }
      else
      {
        _displayHandler->clearDisplay();
      }
    }
    else
    {
      _displayHandler->show(_display);
    }
  }

  // called if a numeric key is pressed in timer input mode
  void numericInput(uint8_t digit)
  {
    // during time input, process numeric input
    switch (_inputMode)
    {
    case input_mode::time:
      // avoid leading zeros
      if (_display.equals("0"))
      {
        _display = static_cast<char>(digit + 48);
      }
      else
      {
        if (_display.length() < _displayHandler->getDigitCount())
        {
          _display += static_cast<char>(digit + 48);
        }
      }
      break;

    case input_mode::timer:
      if (_display.equals("0"))
      {
        _display = static_cast<char>(digit + 48);
      }
      else
      {
        if (_display.length() < MAX_TIMER_INPUT)
        {
          _display += static_cast<char>(digit + 48);
        }
      }
      break;

    case input_mode::none:
      switch (digit)
      {
      case clock_mode::time:
      case clock_mode::time_no_seconds:
      case clock_mode::time_moving:
      case clock_mode::time_or_date:
      case clock_mode::time_and_date:
      case clock_mode::time_and_temp:
      case clock_mode::time_and_date_and_temp:
      case clock_mode::time_centiseconds:
      case clock_mode::dual_time:
      case clock_mode::date_and_time_raw:
      case clock_mode::stopwatch: // reached with [00]
        selectClockMode(static_cast<clock_mode::clock_mode>(digit));
        break;
      }
      break;
    }
  }

  // switch to a clock mode
  void selectClockMode(clock_mode::clock_mode mode)
  {
    _displayHandler->clearDisplay();
    SettingsCache::clockMode = mode;
    _refreshLighting = true;
  }

  // called if a operator key is pressed in clock mode
  void operationInput(operation op)
  {
    switch (op)
    {
    case operation::decimal_separator:
      // [.] selects the timer
      if (_inputMode == input_mode::none)
      {
        selectClockMode(clock_mode::timer);
      }
      break;

#if RPN_MODE
    case operation::clear_stack:
#else
    case operation::allclear:
#endif
      switch (SettingsCache::clockMode)
      {
      case clock_mode::stopwatch:
        break;

      case clock_mode::timer:
        if (_inputMode == input_mode::none)
        {
          _inputMode = input_mode::timer;
          _display = "0";
          _displayHandler->show(_display);
          _refreshLighting = true;
        }
        else
        {
          _inputMode = input_mode::none;
          _displayHandler->clearDigits();
        }
        break;

        break;

      default:
        if (_inputMode == input_mode::none)
        {
          _inputMode = input_mode::time;
          _display = "0";
          _displayHandler->show(_display);
          _refreshLighting = true;
        }
        else
        {
          _inputMode = input_mode::none;
          _displayHandler->clearDigits();
        }
        break;
      }
      break;

#if RPN_MODE
    case operation::backspace:
#else
    case operation::clear:
#endif
      switch (SettingsCache::clockMode)
      {
      case clock_mode::stopwatch:
        _stopwatchMode = stopwatch_mode::zero;
        break;

      case clock_mode::timer:
        if (_inputMode != input_mode::none)
        {
          _display.remove(_display.length() - 1);
          if (_display.length() == 0)
          {
            _display = "0";
          }
          _displayHandler->show(_display);
        }
        else
        {
          _timerMode = timer_mode::set;
          _timerElapsedMillis = 0;
        }
        break;

      default:
        if (_inputMode != input_mode::none)
        {
          _display.remove(_display.length() - 1);
          if (_display.length() == 0)
          {
            _display = "0";
          }
          _displayHandler->show(_display);
        }
        break;
      }
      break;

#if RPN_MODE
    case operation::enter:
#else
    case operation::equals:
#endif
      switch (SettingsCache::clockMode)
      {
      case clock_mode::stopwatch:
        if (_stopwatchMode == stopwatch_mode::running)
        {
          _stopwatchMode = stopwatch_mode::stopped;
        }
        else
        {
          _stopwatchMode = stopwatch_mode::running;
        }
        break;

      case clock_mode::timer:
        if (_inputMode == input_mode::timer)
        {
          _inputMode = input_mode::none;
          _displayHandler->clearDigits();
          setTimer();
        }
        else
        {
          switch (_timerMode)
          {
          case timer_mode::running:
            _timerMode = timer_mode::stopped;
            _timerElapsedMillis += (esp_timer_get_time() / 1000LL) - _timerStartMillis;
            break;

          case timer_mode::set:
          case timer_mode::stopped:
            _timerMode = timer_mode::running;
            _timerStartMillis = esp_timer_get_time() / 1000LL;
            break;

          case timer_mode::zero:
            // do nothing
            break;
          }
        }
        break;

      default:
        switch (_inputMode)
        {
        case input_mode::time:
          _inputMode = input_mode::none;
          _displayHandler->clearDigits();
          setTimeFromInput();
          break;

        default: // avoid warning
          break;
        }
        break;
      }
    default: // avoid warning
      break;
    }
  }

  // set the timer according user input
  void setTimer()
  {
    int64_t interval = 0;
    if (_display.length() <= MAX_TIMER_INPUT)
    {
      int count = MAX_TIMER_INPUT - _display.length();
      for (int i = 0; i < count; i++)
      {
        _display = "0" + _display;
      }
      int temp = 0;
      temp = _display.substring(0, 2).toInt();
      interval += temp * 86400;
      temp = _display.substring(2, 4).toInt();
      interval += temp * 3600;
      temp = _display.substring(4, 6).toInt();
      interval += temp * 60;
      temp = _display.substring(6, 8).toInt();
      interval += temp;
      if (interval <= MAX_TIMER_INTERVAL)
      {
        interval *= 1000;
        interval += 999;
        _timerSetMillis = interval;
        _timerElapsedMillis = 0;
        _timerMode = timer_mode::set;
      }
    }
  }
};
