axtar/Nixie-Calculator/Firmware/Controller/main/CalcMath.hpp

// CalcMath.hpp

// provides higher level math operations
// uses arbitrary-precision arithmetic (experimental)

// Copyright (C) 2020-2026 highvoltglow
// Licensed under the MIT License

#pragma once

#include <Arduino.h>
#include <ratpak.h>
#include <CalcDefs.h>
#include <CalcError.hpp>

class CalcMath
{
public:
  CalcMath() = delete;

  // do the math and store the result in px
  // maxTrig and angletype are needed for trigonometric operations
  static operation_return_code calculate(PRAT *px, PRAT py, operation op, uint32_t radix, int32_t precision, PRAT maxTrig = rat_zero, angle_type angleType = angle_type::deg)
  {
    operation_return_code result = operation_return_code::success;
    PRAT p = nullptr;
    PRAT q = nullptr;
    switch (op)
    {
    case operation::ln: // natural logarithm
      try
      {
        lograt(px, precision);
      }
      catch (uint32_t error)
      {
        result = CalcError::toOperationReturnCode(error);
      }
      break;

    case operation::log10: // logarithm base 10
      try
      {
        log10rat(px, precision);
      }
      catch (uint32_t error)
      {
        result = CalcError::toOperationReturnCode(error);
      }
      break;

    case operation::logy: // logarithm base y
      try
      {
        DUPRAT(p, py);
        DUPRAT(q, *px);
        lograt(&p, precision);
        lograt(&q, precision);
        divrat(&p, q, precision);
        DUPRAT(*px, p);
      }
      catch (uint32_t error)
      {
        result = CalcError::toOperationReturnCode(error);
      }
      break;

    case operation::integer: // remove fract part
      try
      {
        intrat(px, radix, precision);
      }
      catch (uint32_t error)
      {
        result = CalcError::toOperationReturnCode(error);
      }
      break;

    case operation::square_root: // square root
    {
      try
      {
        if (SIGN(*px) == 1)
        {
          rootrat(px, rat_two, radix, precision);
        }
        else
        {
          throw(CALC_E_DOMAIN);
        }
      }
      catch (uint32_t error)
      {
        result = CalcError::toOperationReturnCode(error);
      }
    }
    break;

    case operation::yroot: // y-th root
      try
      {
        DUPRAT(p, py);
        rootrat(&p, *px, radix, precision);
        DUPRAT(*px, p);
      }
      catch (uint32_t error)
      {
        result = CalcError::toOperationReturnCode(error);
      }
      break;

    case operation::exp: // exponential
      try
      {
        DUPRAT(p, rat_exp);
        powrat(&p, *px, radix, precision);
        DUPRAT(*px, p);
      }
      catch (uint32_t error)
      {
        result = CalcError::toOperationReturnCode(error);
      }
      break;

    case operation::pow: // power
      try
      {
        DUPRAT(p, py);
        powrat(&p, *px, radix, precision);
        DUPRAT(*px, p);
      }
      catch (uint32_t error)
      {
        result = CalcError::toOperationReturnCode(error);
      }
      break;

    case operation::pow2: // square
      try
      {
        powrat(px, rat_two, radix, precision);
      }
      catch (uint32_t error)
      {
        result = CalcError::toOperationReturnCode(error);
      }
      break;

    case operation::pow3: // cubic
      try
      {
        p = i32torat(3);
        powrat(px, p, radix, precision);
      }
      catch (uint32_t error)
      {
        result = CalcError::toOperationReturnCode(error);
      }
      break;

    case operation::factorial: // factorial
      try
      {
        factrat(px, radix, precision);
      }
      catch (uint32_t error)
      {
        result = CalcError::toOperationReturnCode(error);
      }
      break;

    case operation::modulo: // modulo
      try
      {
        DUPRAT(p, py);
        modrat(&p, *px);
        DUPRAT(*px, p);
      }
      catch (uint32_t error)
      {
        result = CalcError::toOperationReturnCode(error);
      }
      break;

    case operation::addition: // addition
      try
      {
        addrat(px, py, precision);
      }
      catch (uint32_t error)
      {
        result = CalcError::toOperationReturnCode(error);
      }
      break;

    case operation::subtraction: // subtraction
      try
      {
        DUPRAT(p, py);
        subrat(&p, *px, precision);
        DUPRAT(*px, p);
      }
      catch (uint32_t error)
      {
        result = CalcError::toOperationReturnCode(error);
      }
      break;

    case operation::multiplication: // multiplication
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
        }
        else
        {
          throw(CALC_E_DOMAIN);
        }
      }
      catch (uint32_t error)
      {
        result = CalcError::toOperationReturnCode(error);
      }
      break;

    case operation::atan: // arctangent
      try
      {
        if (isInTrigRange(*px, maxTrig, precision))
        {
          atananglerat(px, angleType == angle_type::deg ? AngleType::Degrees : AngleType::Radians, radix, precision);
        }
        else
        {
          throw(CALC_E_DOMAIN);
        }
      }
      catch (uint32_t error)
      {
        result = CalcError::toOperationReturnCode(error);
      }
      break;

    case operation::tanh: // hyperbolic tangent
      try
      {
        if (isInTrigRange(*px, maxTrig, precision))
        {
          tanhrat(px, radix, precision);
        }
        else
        {
          throw(CALC_E_DOMAIN);
        }
      }
      catch (uint32_t error)
      {
        result = CalcError::toOperationReturnCode(error);
      }
      break;

    case operation::permutations: // permutations
      try
      {
        // check for positive integers and y > x
        DUPRAT(p, *px);
        fracrat(&p, radix, precision);
        DUPRAT(q, py);
        fracrat(&q, radix, precision);
        if (!zerrat(p) || !zerrat(q))
        {
          throw(CALC_E_DOMAIN);
        }
        if ((SIGN(*px) == (-1)) || (SIGN(py) == (-1)) || (rat_lt(py, *px, precision)))
        {
          throw(CALC_E_DOMAIN);
        }

        // calculate permutations,
        int32_t r = rattoi32(*px, radix, precision);
        // we have to put a limit to the loop, calculation is slow on a MC
        if (r > 1000 || r < 0)
        {
          throw(CALC_E_DOMAIN);
        }
        DUPRAT(*px, rat_one);
        for (int32_t i = 0; i < r; i++)
        {
          DUPRAT(q, py);
          destroyrat(p);
          p = i32torat(i);
          subrat(&q, p, precision);
          mulrat(px, q, precision);
        }
      }
      catch (uint32_t error)
      {
        result = CalcError::toOperationReturnCode(error);
      }
      break;

    case operation::combinations: // combinations
      try
      {
        // check for positive integers and y > x
        DUPRAT(p, *px);
        fracrat(&p, radix, precision);
        DUPRAT(q, py);
        fracrat(&q, radix, precision);
        if (!zerrat(p) || !zerrat(q))
        {
          throw(CALC_E_DOMAIN);
        }
        if ((SIGN(*px) == (-1)) || (SIGN(py) == (-1)) || (rat_lt(py, *px, precision)))
        {
          throw(CALC_E_DOMAIN);
        }

        // optimize loop
        int32_t r1 = rattoi32(*px, radix, precision);
        DUPRAT(p, py);
        subrat(&p, *px, precision);
        int32_t r2 = rattoi32(p, radix, precision);
        int32_t r = std::min(r1, r2);

        // we have to put a limit to the loop, calculation is slow on a MC
        if (r > 5000 || r < 0)
        {
          throw(CALC_E_DOMAIN);
        }

        // calculate
        DUPRAT(*px, rat_one);
        for (int32_t i = 0; i < r; i++)
        {
          DUPRAT(q, py);
          destroyrat(p);
          p = i32torat(i);
          subrat(&q, p, precision);
          mulrat(px, q, precision);
          destroyrat(p);
          p = i32torat(i + 1);
          divrat(px, p, precision);
        }
      }
      catch (uint32_t error)
      {
        result = CalcError::toOperationReturnCode(error);
      }
      break;

    default:
      result = operation_return_code::unknownoperation;
      break;
    }
    destroyrat(p);
    destroyrat(q);
    return (result);
  }

  // get some special values
  static void getSpecialValue(PRAT *px, operation op, uint32_t radix, int32_t precision)
  {
    switch (op)
    {
    case operation::pi:
      DUPRAT(*px, pi);
      break;

    case operation::e:
      DUPRAT(*px, rat_exp);
      break;

    case operation::rnd:
      getRandomPrat(px, radix, precision);
      break;

    default:
      break;
    }
  }

  // generate a random number
  static void getRandomPrat(PRAT *px, uint32_t radix, int32_t precision)
  {
    String s("0.");
    for (int i = 0; i < precision; i++)
    {
      long r = random(0, 10);
      s += String(r);
    }
    std::string_view sm(s.c_str());
    std::string_view se("0");
    destroyrat(*px);
    *px = StringToRat(false, sm, false, se, radix, precision);
  }

private:
  // check range to prevent slow loops
  static bool isInTrigRange(PRAT px, PRAT maxTrig, int32_t precision)
  {
    bool result = false;
    if (rat_lt(px, maxTrig, precision))
    {
      PRAT negMaxTrig = nullptr;
      DUPRAT(negMaxTrig, maxTrig);
      negMaxTrig->pp->sign *= -1;
      result = rat_gt(px, negMaxTrig, precision);
      destroyrat(negMaxTrig);
    }
    return result;
  }
};
