axtar/Nixie-Calculator/Firmware/Controller/main/DisplayHAL_IN12.hpp

// displayHAL_IN12.hpp

// implements the hardware abstraction layer interface
// for the IN-12 display

// Copyright (C) 2020-2026 highvoltglow
// Licensed under the MIT License

#pragma once

#include <Arduino.h>
#include <displayHAL.hpp>

constexpr uint8_t IN12_REGISTERCOUNT = 192;
constexpr uint8_t IN12_DIGITCOUNT = 14;
constexpr uint8_t IN12_DECIMALSEPARATORCOUNT = 14;
constexpr uint8_t IN12_LEDCOUNT = 16;

class DisplayHAL_IN12 : public DisplayHAL
{
public:
  DisplayHAL_IN12()
  {
    initTranslationTable();
    _dsp = decimal_separator_position::right;
  }

  virtual ~DisplayHAL_IN12()
  {
    free(_translationTable);
  }

  uint8_t getRegisterCount() const
  {
    return (IN12_REGISTERCOUNT);
  }

  uint8_t getDigitCount() const
  {
    return (IN12_DIGITCOUNT);
  }

  uint8_t getDecimalSeparatorCount() const
  {
    return (IN12_DECIMALSEPARATORCOUNT);
  }

  uint8_t getLEDCount() const
  {
    return (IN12_LEDCOUNT);
  }

  bool hasPlusSign() const
  {
    return (true);
  }

  bool hasExpMinusSign() const
  {
    return (true);
  }

  bool hasExpPlusSign() const
  {
    return (true);
  }

  bool hasMenuSign() const
  {
    return (true);
  }

  led_type getLedType() const
  {
    return (led_type::smd);
  }

  // return information about what is connected to a specific shift register output
  register_type getRegisterInfo(uint8_t registerNumber, uint8_t *digit, uint8_t *number) const
  {
    *digit = 0;
    *number = 0;

    register_type regType;

    if ((registerNumber < 1) || (registerNumber > IN12_REGISTERCOUNT))
    {
      regType = register_type::unknown;
    }
    else
    {
      regType = _translationTable[registerNumber - 1].rt;
      *digit = _translationTable[registerNumber - 1].digit;
      *number = _translationTable[registerNumber - 1].number;
    }
    return (regType);
  }

  // not used for nixies
  void getDigitAddress(uint8_t digit, uint8_t *index, uint8_t *position) const
  {
    *index = 0;
    *position = 0;
  }

  // return the decimal separator position
  decimal_separator_position getDecimalSeparatorPosition() const
  {
    return (_dsp);
  }

  // left for IN-12B, right for IN-12A
  void setDecimalSeparatorPosition(decimal_separator_position dsp)
  {
    _dsp = dsp;
  }

private:
  TRANSLATION_TABLE_ENTRY *_translationTable;
  decimal_separator_position _dsp;

  // translation table
  // Nixie   Digit
  // -----   -----
  // N0  --> base sign
  // N1  --> 0
  // N2  --> 1
  // N3  --> 2
  // N4  --> 3
  // N5  --> 4
  // N6  --> 5
  // N7  --> 6
  // N8  --> 7
  // N9  --> 8
  // N10 --> 9
  // N11 --> 10
  // N12 --> 11
  // N13 --> 12
  // N14 --> 13
  // N15 --> exponent sign

  // this table contains the connection between the shift register outputs and the nixie and neon pins
  // this was introduced to simplify the routing of the driver and display PCBs
  void initTranslationTable()
  {
    _translationTable = (TRANSLATION_TABLE_ENTRY *)calloc(IN12_REGISTERCOUNT, sizeof(TRANSLATION_TABLE_ENTRY));

    // digit 0, N1
    _translationTable[24] = {register_type::number, 0, 0};
    _translationTable[23] = {register_type::number, 0, 1};
    _translationTable[22] = {register_type::number, 0, 2};
    _translationTable[11] = {register_type::number, 0, 3};
    _translationTable[10] = {register_type::number, 0, 4};
    _translationTable[9] = {register_type::number, 0, 5};
    _translationTable[8] = {register_type::number, 0, 6};
    _translationTable[7] = {register_type::number, 0, 7};
    _translationTable[6] = {register_type::number, 0, 8};
    _translationTable[25] = {register_type::number, 0, 9};
    _translationTable[26] = {register_type::decimal_separator, 0, 0};

    // digit 1, N2
    _translationTable[29] = {register_type::number, 1, 0};
    _translationTable[28] = {register_type::number, 1, 1};
    _translationTable[27] = {register_type::number, 1, 2};
    _translationTable[5] = {register_type::number, 1, 3};
    _translationTable[4] = {register_type::number, 1, 4};
    _translationTable[3] = {register_type::number, 1, 5};
    _translationTable[2] = {register_type::number, 1, 6};
    _translationTable[1] = {register_type::number, 1, 7};
    _translationTable[0] = {register_type::number, 1, 8};
    _translationTable[30] = {register_type::number, 1, 9};
    _translationTable[31] = {register_type::decimal_separator, 1, 0};

    // digit 2, N3
    _translationTable[52] = {register_type::number, 2, 0};
    _translationTable[51] = {register_type::number, 2, 1};
    _translationTable[50] = {register_type::number, 2, 2};
    _translationTable[49] = {register_type::number, 2, 3};
    _translationTable[48] = {register_type::number, 2, 4};
    _translationTable[47] = {register_type::number, 2, 5};
    _translationTable[46] = {register_type::number, 2, 6};
    _translationTable[45] = {register_type::number, 2, 7};
    _translationTable[44] = {register_type::number, 2, 8};
    _translationTable[53] = {register_type::number, 2, 9};
    _translationTable[54] = {register_type::decimal_separator, 2, 0};

    // digit 3, N4
    _translationTable[57] = {register_type::number, 3, 0};
    _translationTable[56] = {register_type::number, 3, 1};
    _translationTable[55] = {register_type::number, 3, 2};
    _translationTable[43] = {register_type::number, 3, 3};
    _translationTable[42] = {register_type::number, 3, 4};
    _translationTable[41] = {register_type::number, 3, 5};
    _translationTable[40] = {register_type::number, 3, 6};
    _translationTable[39] = {register_type::number, 3, 7};
    _translationTable[38] = {register_type::number, 3, 8};
    _translationTable[58] = {register_type::number, 3, 9};
    _translationTable[59] = {register_type::decimal_separator, 3, 0};

    // digit 4, N5
    _translationTable[62] = {register_type::number, 4, 0};
    _translationTable[61] = {register_type::number, 4, 1};
    _translationTable[60] = {register_type::number, 4, 2};
    _translationTable[37] = {register_type::number, 4, 3};
    _translationTable[36] = {register_type::number, 4, 4};
    _translationTable[35] = {register_type::number, 4, 5};
    _translationTable[34] = {register_type::number, 4, 6};
    _translationTable[33] = {register_type::number, 4, 7};
    _translationTable[32] = {register_type::number, 4, 8};
    _translationTable[63] = {register_type::number, 4, 9};
    _translationTable[84] = {register_type::decimal_separator, 4, 0};

    // digit 5, N6
    _translationTable[88] = {register_type::number, 5, 0};
    _translationTable[87] = {register_type::number, 5, 1};
    _translationTable[86] = {register_type::number, 5, 2};
    _translationTable[75] = {register_type::number, 5, 3};
    _translationTable[74] = {register_type::number, 5, 4};
    _translationTable[73] = {register_type::number, 5, 5};
    _translationTable[72] = {register_type::number, 5, 6};
    _translationTable[71] = {register_type::number, 5, 7};
    _translationTable[70] = {register_type::number, 5, 8};
    _translationTable[89] = {register_type::number, 5, 9};
    _translationTable[90] = {register_type::decimal_separator, 5, 0};

    // digit 6, N7
    _translationTable[93] = {register_type::number, 6, 0};
    _translationTable[92] = {register_type::number, 6, 1};
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
    _translationTable[129] = {register_type::number, 11, 7};
    _translationTable[128] = {register_type::number, 11, 8};
    _translationTable[158] = {register_type::number, 11, 9};
    _translationTable[159] = {register_type::decimal_separator, 11, 0};

    // digit 12, N13
    _translationTable[180] = {register_type::number, 12, 0};
    _translationTable[179] = {register_type::number, 12, 1};
    _translationTable[178] = {register_type::number, 12, 2};
    _translationTable[177] = {register_type::number, 12, 3};
    _translationTable[176] = {register_type::number, 12, 4};
    _translationTable[175] = {register_type::number, 12, 5};
    _translationTable[174] = {register_type::number, 12, 6};
    _translationTable[173] = {register_type::number, 12, 7};
    _translationTable[172] = {register_type::number, 12, 8};
    _translationTable[181] = {register_type::number, 12, 9};
    _translationTable[182] = {register_type::decimal_separator, 12, 0};

    // digit 13, N14
    _translationTable[185] = {register_type::number, 13, 0};
    _translationTable[184] = {register_type::number, 13, 1};
    _translationTable[183] = {register_type::number, 13, 2};
    _translationTable[171] = {register_type::number, 13, 3};
    _translationTable[170] = {register_type::number, 13, 4};
    _translationTable[169] = {register_type::number, 13, 5};
    _translationTable[168] = {register_type::number, 13, 6};
    _translationTable[167] = {register_type::number, 13, 7};
    _translationTable[166] = {register_type::number, 13, 8};
    _translationTable[186] = {register_type::number, 13, 9};
    _translationTable[187] = {register_type::decimal_separator, 13, 0};

    // left IN-15A, N0
    _translationTable[12] = {register_type::minus_sign, 0, 0};   // -
    _translationTable[13] = {register_type::plus_sign, 0, 1};    // +
    _translationTable[15] = {register_type::menu_sign, 0, 2};    // M
    _translationTable[14] = {register_type::special_char, 0, 3}; // m
    _translationTable[17] = {register_type::special_char, 0, 4}; // N
    _translationTable[19] = {register_type::special_char, 0, 5}; // n
    _translationTable[21] = {register_type::special_char, 0, 6}; // P
    _translationTable[20] = {register_type::special_char, 0, 7}; // µ
    _translationTable[18] = {register_type::special_char, 0, 8}; // %
    _translationTable[16] = {register_type::special_char, 0, 9}; // k

    // right IN-15A, N15
    _translationTable[160] = {register_type::exp_minus_sign, 1, 0}; // -
    _translationTable[161] = {register_type::exp_plus_sign, 1, 1};  // +
    _translationTable[163] = {register_type::special_char, 1, 2};   // M
    _translationTable[162] = {register_type::special_char, 1, 3};   // m
    _translationTable[165] = {register_type::special_char, 1, 4};   // N
    _translationTable[189] = {register_type::special_char, 1, 5};   // n
    _translationTable[191] = {register_type::special_char, 1, 6};   // P
    _translationTable[190] = {register_type::special_char, 1, 7};   // µ
    _translationTable[188] = {register_type::special_char, 1, 8};   // %
    _translationTable[164] = {register_type::special_char, 1, 9};   // k

    // not connect registers
    _translationTable[76] = {register_type::not_connected, 0, 0};
    _translationTable[77] = {register_type::not_connected, 0, 0};
    _translationTable[78] = {register_type::not_connected, 0, 0};
    _translationTable[79] = {register_type::not_connected, 0, 0};
    _translationTable[80] = {register_type::not_connected, 0, 0};
    _translationTable[81] = {register_type::not_connected, 0, 0};
    _translationTable[82] = {register_type::not_connected, 0, 0};
    _translationTable[83] = {register_type::not_connected, 0, 0};
    _translationTable[85] = {register_type::not_connected, 0, 0};
    _translationTable[108] = {register_type::not_connected, 0, 0};
    _translationTable[109] = {register_type::not_connected, 0, 0};
    _translationTable[110] = {register_type::not_connected, 0, 0};
    _translationTable[111] = {register_type::not_connected, 0, 0};
    _translationTable[112] = {register_type::not_connected, 0, 0};
    _translationTable[113] = {register_type::not_connected, 0, 0};
    _translationTable[114] = {register_type::not_connected, 0, 0};
    _translationTable[115] = {register_type::not_connected, 0, 0};
    _translationTable[126] = {register_type::not_connected, 0, 0};
  }
};
