axtar/Nixie-Calculator/Firmware/Controller/main/DisplayHAL_IN17.hpp

// displayHAL_IN17.hpp

// implements the hardware abstraction layer interface
// for the IN-17 display

// Copyright (C) 2020-2026 highvoltglow
// Licensed under the MIT License

#pragma once

#include <Arduino.h>
#include <displayHAL.hpp>

constexpr uint8_t IN17_REGISTERCOUNT = 160;
constexpr uint8_t IN17_DIGITCOUNT = 14;
constexpr uint8_t IN17_DECIMALSEPARATORCOUNT = 14;
constexpr uint8_t IN17_LEDCOUNT = 14;
constexpr auto IN17_DSP = decimal_separator_position::right;

class DisplayHAL_IN17 : public DisplayHAL
{
public:
  DisplayHAL_IN17()
  {
    initTranslationTable();
  }

  virtual ~DisplayHAL_IN17()
  {
    free(_translationTable);
  }

  uint8_t getRegisterCount() const
  {
    return (IN17_REGISTERCOUNT);
  }

  uint8_t getDigitCount() const
  {
    return (IN17_DIGITCOUNT);
  }

  uint8_t getDecimalSeparatorCount() const
  {
    return (IN17_DECIMALSEPARATORCOUNT);
  }

  uint8_t getLEDCount() const
  {
    return (IN17_LEDCOUNT);
  }

  bool hasPlusSign() const
  {
    return (false);
  }

  bool hasExpMinusSign() const
  {
    return (true);
  }

  bool hasExpPlusSign() const
  {
    return (false);
  }

  bool hasMenuSign() const
  {
    return (false);
  }

  led_type getLedType() const
  {
    return (led_type::smd);
  }

  // return information about what is connected to a specific shift register output
  register_type getRegisterInfo(uint8_t registerNumber, uint8_t *digit, uint8_t *number) const
  {
    *digit = 0;
    *number = 0;

    register_type regType;

    if ((registerNumber < 1) || (registerNumber > IN17_REGISTERCOUNT))
    {
      regType = register_type::unknown;
    }
    else
    {
      regType = _translationTable[registerNumber - 1].rt;
      *digit = _translationTable[registerNumber - 1].digit;
      *number = _translationTable[registerNumber - 1].number;
    }
    return (regType);
  }

  // not used for nixies
  void getDigitAddress(uint8_t digit, uint8_t *index, uint8_t *position) const
  {
    *index = 0;
    *position = 0;
  }

  // return the decimal separator position
  decimal_separator_position getDecimalSeparatorPosition() const
  {
    return (IN17_DSP);
  }

  // not used
  void setDecimalSeparatorPosition(decimal_separator_position dsp)
  {
  }

private:
  TRANSLATION_TABLE_ENTRY *_translationTable;

  // translation table
  // Nixie   Digit
  // -----   -----
  // N1  --> 0
  // N2  --> 1
  // N3  --> 2
  // N4  --> 3
  // N5  --> 4
  // N6  --> 5
  // N7  --> 6
  // N8  --> 7
  // N9  --> 8
  // N10 --> 9
  // N11 --> 10
  // N12 --> 11
  // N13 --> 12
  // N14 --> 13

  // this table contains the connection between the shift register outputs and the nixie and neon pins
  // this was introduced to simplify the routing of the driver and display PCBs
  void initTranslationTable()
  {
    _translationTable = (TRANSLATION_TABLE_ENTRY *)calloc(IN17_REGISTERCOUNT, sizeof(TRANSLATION_TABLE_ENTRY));
    _translationTable[25] = {register_type::number, 0, 0};
    _translationTable[26] = {register_type::number, 0, 1};
    _translationTable[27] = {register_type::number, 0, 2};
    _translationTable[28] = {register_type::number, 0, 3};
    _translationTable[29] = {register_type::number, 0, 4};
    _translationTable[31] = {register_type::number, 0, 5};
    _translationTable[30] = {register_type::number, 0, 6};
    _translationTable[22] = {register_type::number, 0, 7};
    _translationTable[23] = {register_type::number, 0, 8};
    _translationTable[24] = {register_type::number, 0, 9};
    _translationTable[21] = {register_type::decimal_separator, 0, 0};
    _translationTable[14] = {register_type::number, 1, 0};
    _translationTable[15] = {register_type::number, 1, 1};
    _translationTable[16] = {register_type::number, 1, 2};
    _translationTable[17] = {register_type::number, 1, 3};
    _translationTable[18] = {register_type::number, 1, 4};
    _translationTable[20] = {register_type::number, 1, 5};
    _translationTable[19] = {register_type::number, 1, 6};
    _translationTable[11] = {register_type::number, 1, 7};
    _translationTable[12] = {register_type::number, 1, 8};
    _translationTable[13] = {register_type::number, 1, 9};
    _translationTable[10] = {register_type::decimal_separator, 1, 0};
    _translationTable[3] = {register_type::number, 2, 0};
    _translationTable[4] = {register_type::number, 2, 1};
    _translationTable[5] = {register_type::number, 2, 2};
    _translationTable[6] = {register_type::number, 2, 3};
    _translationTable[7] = {register_type::number, 2, 4};
    _translationTable[9] = {register_type::number, 2, 5};
    _translationTable[8] = {register_type::number, 2, 6};
    _translationTable[0] = {register_type::number, 2, 7};
    _translationTable[1] = {register_type::number, 2, 8};
    _translationTable[2] = {register_type::number, 2, 9};
    _translationTable[63] = {register_type::decimal_separator, 2, 0};
    _translationTable[56] = {register_type::number, 3, 0};
    _translationTable[57] = {register_type::number, 3, 1};
    _translationTable[58] = {register_type::number, 3, 2};
    _translationTable[59] = {register_type::number, 3, 3};
    _translationTable[60] = {register_type::number, 3, 4};
    _translationTable[62] = {register_type::number, 3, 5};
    _translationTable[61] = {register_type::number, 3, 6};
    _translationTable[53] = {register_type::number, 3, 7};
    _translationTable[54] = {register_type::number, 3, 8};
    _translationTable[55] = {register_type::number, 3, 9};
    _translationTable[52] = {register_type::decimal_separator, 3, 0};
    _translationTable[45] = {register_type::number, 4, 0};
    _translationTable[46] = {register_type::number, 4, 1};
    _translationTable[47] = {register_type::number, 4, 2};
    _translationTable[48] = {register_type::number, 4, 3};
    _translationTable[49] = {register_type::number, 4, 4};
    _translationTable[51] = {register_type::number, 4, 5};
    _translationTable[50] = {register_type::number, 4, 6};
    _translationTable[42] = {register_type::number, 4, 7};
    _translationTable[43] = {register_type::number, 4, 8};
    _translationTable[44] = {register_type::number, 4, 9};
    _translationTable[41] = {register_type::decimal_separator, 4, 0};
    _translationTable[34] = {register_type::number, 5, 0};
    _translationTable[35] = {register_type::number, 5, 1};
    _translationTable[36] = {register_type::number, 5, 2};
    _translationTable[37] = {register_type::number, 5, 3};
    _translationTable[38] = {register_type::number, 5, 4};
    _translationTable[40] = {register_type::number, 5, 5};
    _translationTable[39] = {register_type::number, 5, 6};
    _translationTable[95] = {register_type::number, 5, 7};
    _translationTable[32] = {register_type::number, 5, 8};
    _translationTable[33] = {register_type::number, 5, 9};
    _translationTable[94] = {register_type::decimal_separator, 5, 0};
    _translationTable[87] = {register_type::number, 6, 0};
    _translationTable[88] = {register_type::number, 6, 1};
    _translationTable[89] = {register_type::number, 6, 2};
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
    _translationTable[149] = {register_type::number, 12, 6};
    _translationTable[140] = {register_type::number, 12, 7};
    _translationTable[141] = {register_type::number, 12, 8};
    _translationTable[142] = {register_type::number, 12, 9};
    _translationTable[148] = {register_type::decimal_separator, 12, 0};
    _translationTable[132] = {register_type::number, 13, 0};
    _translationTable[133] = {register_type::number, 13, 1};
    _translationTable[134] = {register_type::number, 13, 2};
    _translationTable[135] = {register_type::number, 13, 3};
    _translationTable[137] = {register_type::number, 13, 4};
    _translationTable[139] = {register_type::number, 13, 5};
    _translationTable[138] = {register_type::number, 13, 6};
    _translationTable[129] = {register_type::number, 13, 7};
    _translationTable[130] = {register_type::number, 13, 8};
    _translationTable[131] = {register_type::number, 13, 9};
    _translationTable[136] = {register_type::decimal_separator, 13, 0};
    _translationTable[128] = {register_type::minus_sign, 0, 0};
    _translationTable[155] = {register_type::exp_minus_sign, 0, 0};
    _translationTable[156] = {register_type::not_connected, 0, 0};
    _translationTable[157] = {register_type::not_connected, 0, 0};
    _translationTable[158] = {register_type::not_connected, 0, 0};
    _translationTable[159] = {register_type::not_connected, 0, 0};
  }
};
