axtar/Nixie-Calculator/Firmware/Controller/include/SettingDefs.h

// SettingDefs.h

// settings related enums and definitions

// Copyright (C) 2020-2026 highvoltglow
// Licensed under the MIT License

#pragma once

#include <Arduino.h>

// define upper numeric limit for RGB and time settings
constexpr int32_t MAX_RGB_INT = 16777215;
constexpr int32_t MAX_TIME_INT = 1439;

// elements of a RGB setting
typedef struct
{
  uint8_t red;
  uint8_t green;
  uint8_t blue;
} RGBCOLOR;

// elements of a time setting, used for both start and stop times
typedef struct
{
  uint8_t hour;
  uint8_t minute;
} SCHEDULETIME;

// enums
// using namespaces to avoid ambiguities

// settings
namespace setting_id
{
  // don't change without updating the manual
  enum setting_id
  {
    startupmode = 1, // Start in calculator or in clock mode
    showversion,     // Show version during start-up
    autooffmode,     // Shutdown high voltage or switch to clock mode after a period of no keyboard activity
    autooffdelay,    // Delay in minutes for auto off mode
    offstarttime,    // Start time of the scheduled off window, independent of autooffmode
    offstoptime,     // Stop time of the scheduled off window, independent of autooffmode
    offdays,         // Days of the week the HV is off for the entire day
    clockmode,       // Predefined display format in clock mode
    hourmode,        // 12 or 24 hours mode
    leadingzero,     // Hours leading zero off or on
    timeseparator,   // separator mode in compact time format
    timeeffects,     // Time digit effects
    dateformat,      // Date format
    pirmode,         // PIR off or on
    pirdelay,        // PIR delay time in minutes before shutting down the high voltage
    gpsmode,         // GPS time sync off or on
    gpsspeed,        // GPS communication baud rate
    gpssyncinterval, // GPS time sync interval in minutes
    temperaturemode, // Temperature sensor off or on
    temperaturecf,   // Temperature in C or F
    ledmode,         // LEDs on by time or always
    ledbrightness,   // General brightness of the LED lighting in percent
    calcrgbmode,     // Fixed colors or random colors in calculator mode
    clockrgbmode,    // Fixed colors or random colors in clock mode
    breathingmode,   // Breathing (pulsing brightness) effect for LED lighting off or on
    trigcolorchange, // Trigger color change event for random RGB modes in clock mode
    ledstarttime,    // Start time of LED lighting
    ledstoptime,     // Stop time of LED lighting
    ledstarttime2,   // Start time of LED lighting
    ledstoptime2,    // Stop time of LED lighting
    acpstarttime,    // Start time of cathode poisoning prevention
    acpduration,     // Duration in minutes of cathode poisoning prevention
    acpforceon,      // Force turning nixies on during cathode poisoning prevention
    negativecolor,   // RGB LED color for negative numbers in calculator mode
    positivecolor,   // RGB LED color for positive numbers in calculator mode
    errorcolor,      // RGB LED color for error in calculator mode
    negexpcolor,     // RGB LED color for negative exponents in calculator mode
    posexpcolor,     // RGB LED color for positive exponents in calculator mode
    fixedcalccolor,  // RGB LED fixed color in calculator mode
    timecolor,       // RGB LED color for time in clock mode
    timecolor2,      // RGB LED color for time in clock mode, dual time
    datecolor,       // RGB LED color for date in clock mode
    tempcolor,       // RGB LED color for temperature in clock mode
    fixedcolor,      // RGB LED fixed color in clock mode
    dstweek,         // Daylight saving time change, week of month
    dstdow,          // Daylight saving time change, day of week
    dstmonth,        // Daylight saving time change, month
    dsthour,         // Daylight saving time change, hour
    dstoffset,       // Daylight saving time change, offset to UTC in minutes
    stdweek,         // Standard time change, week of month
    stddow,          // Standard time change, day of week
    stdmonth,        // Standard time change, month
    stdhour,         // Standard time change, hour
    stdoffset,       // Standard time change, offset to UTC in minutes
    dstweek2,        // Dual time daylight saving time change, week of month
    dstdow2,         // Dual time daylight saving time change, day of week
    dstmonth2,       // Dual time daylight saving time change, month
    dsthour2,        // Dual time daylight saving time change, hour
    dstoffset2,      // Dual time daylight saving time change, offset to UTC in minutes
    stdweek2,        // Dual time standard time change, week of month
    stddow2,         // Dual time standard time change, day of week
    stdmonth2,       // Dual time standard time change, month
    stdhour2,        // Dual time standard time change, hour
    stdoffset2,      // Dual time standard time change, offset to UTC in minutes
    gpsnotifysync,   // Notify GPS time sync with a short LED flash off or on
    gpssynccolor,    // RGB LED color for notifying GPS time sync
    notifytimer,     // notify end of timer off or on
    timercolor,      // RGB LED color for notifying end of timer
    fixeddecimals,   // Number of fixed decimals, 0 = floating
    anglemode,       // Startup angle mode
    showbusycalc,    // Show animation during long calculations
    maxexpdigits,    // Max exponent digits
    scrolldelay,     // Interval while scrolling result in 1/10 of seconds
    calcprecision,   // Precision of the calculations
    roundingmode,    // Rounding mode for calculator results, 5/4 or cut
    calcinputdirec,  // Calculator input direction and output format
    inputblinking,   // Input blinking off or on
    brightness,      // Display brightness (LED intensity or nixie blank-line PWM)
    dimbrightness,   // Display brightness during the dimming period
    dimlbrightness,  // LED lighting brightness in percent during the dimming period
    dimstarttime,    // Start time of display dimming
    dimstoptime,     // Stop time of display dimming
    apautostart,     // Automatically start the WiFi access point off or on
    rtcdriftcorr,    // RTC drift compensation in seconds per month
    exttempcorr      // External temperature sensor correction, in 0.1 degrees (Celsius)
  };
}

namespace startup_mode
{
  enum startup_mode
  {
    calculator,
    clock
  };
}
namespace show_version
{
  enum show_version
  {
    off,
    on
  };
}

namespace auto_off_mode
{
  enum auto_off_mode
  {
    off,
    on,
    clock
  };
}

namespace clock_mode
{
  enum clock_mode
  {
    time,
    time_no_seconds,
    time_moving,
    time_or_date,
    time_and_date,
    time_and_temp,
    time_and_date_and_temp,
    time_centiseconds,
    dual_time,
    date_and_time_raw,
    timer,
    stopwatch
  };
}

namespace hour_mode
{
  enum hour_mode
  {
    h12,
    h24
  };
}

namespace leading_zero
{
  enum leading_zero
  {
    off,
    on
  };
}

namespace time_separator
{
  enum time_separator
  {
    off,
    blink,
    on
  };
}

namespace date_format
{
  enum date_format
  {
    ddmmyy,
    yymmdd,
    mmddyy,
    yyddmm
  };
}

namespace pir_mode
{
  enum pir_mode
  {
    off,
    on
  };
}

namespace gps_mode
{
  enum gps_mode
  {
    off,
    on
  };
}

namespace gps_notify_sync
{
  enum gps_notify_sync
  {
    off,
    on
  };
}

namespace gps_speed
{
  enum gps_speed
  {
    br_2400,
    br_4800,
    br_9600,
    br_19200,
    br_38400,
    br_57600,
    br_115200
  };
}

namespace temperature_mode
{
  enum temperature_mode
  {
    off,
    on
  };
}

namespace temperature_cf
{
  enum temperature_cf
  {
    celsius,
    fahrenheit
  };
}

namespace led_mode
{
  enum led_mode
  {
    scheduled,
    always
  };
}

namespace calc_rgb_mode
{
  enum calc_rgb_mode
  {
    off,
    by_content,
    by_content_all,
    random_on_only,
    full_random_on_only,
    fixed_all,
    random_all,
    full_random_all,
    wheel_on_only,
    wheel_all,
    rainbow_on_only,
    rainbow_all
  };
}

namespace clock_rgb_mode
{
  enum clock_rgb_mode
  {
    off,
    by_content,
    random_on_only,
    full_random_on_only,
    fixed_all,
    random_all,
    full_random_all,
    wheel_on_only,
    wheel_all,
    rainbow_on_only,
    rainbow_all
  };
}

namespace acp_force_on
{
  enum acp_force_on
  {
    off,
    on
  };
}

namespace breathing_mode
{
  enum breathing_mode
  {
    off,
    on
  };
}

namespace rounding_mode
{
  enum rounding_mode
  {
    five_four,
    cut
  };
}

namespace fixed_decimals
{
  enum fixed_decimals
  {
    off,
    one,
    two,
    three,
    four,
    five,
    six,
    seven,
    eight
  };
}

namespace notify_timer
{
  enum notify_timer
  {
    off,
    on
  };
}

namespace angle_mode
{
  enum angle_mode
  {
    degrees,
    radians
  };
}

namespace show_busy_calc
{
  enum show_busy_calc
  {
    off,
    moving_decimal_separator,
    digit_flickering
  };
}

namespace time_effects
{
  enum time_effects
  {
    off,
    crossfade,
    rolling1,
    rolling2,
    rolling3
  };
}

namespace calc_input_direc
{
  enum calc_input_direc
  {
    ltr,
    rtl,
    rtl_zero_padding
  };
}

namespace input_blinking
{
  enum input_blinking
  {
    off,
    on
  };
}

namespace ap_auto_start
{
  enum ap_auto_start
  {
    off,
    on
  };
}

namespace trig_color_change
{
  enum trig_color_change
  {
    off,
    every_second,
    every_minute,
    every_hour
  };
}
