axtar/Nixie-Calculator/Firmware/Controller/include/Config.h

// Config.h

// Firmware configuration

// Copyright (C) 2020-2026 highvoltglow
// Licensed under the MIT License

#pragma once

#include <DisplayTypes.h>

// -------------------------------------------------------------------------------
// Display type
// -------------------------------------------------------------------------------
// display_type::in12a -> IN-12A or IN-12B nixie display using neon decimal points
// display_type::in12b -> IN-12B nixie display using nixie decimal points
// display_type::in16  -> IN-16 nixie display
// display_type::in17  -> IN-17 nixie display
// display_type::b5870 -> B5870 nixie display
// display_type::led   -> 7-segment LED display
// -------------------------------------------------------------------------------
constexpr auto DISPLAY_TYPE = display_type::undefined;

// -------------------------------------------------------------------------------
// RPN mode
// -------------------------------------------------------------------------------
// false -> algebraic
// true  -> reverse polish notation
// -------------------------------------------------------------------------------
#define RPN_MODE true

// -------------------------------------------------------------------------------
// Web server support for the calculator web interface
// -------------------------------------------------------------------------------
// false -> disable
// true -> enable
// -------------------------------------------------------------------------------
#define WEB_SUPPORT true

// -------------------------------------------------------------------------------
// Calculator access point SSID and password
// -------------------------------------------------------------------------------
// Please note that this applies to the AP provided by the calculator.
// The calculator itself does not connect to any AP.
// -------------------------------------------------------------------------------
constexpr auto AP_SSID = "NixieCALC";
constexpr auto AP_PWD = "NIXIESareGreat!";

// -------------------------------------------------------------------------------
// OTA (over-the-air) firmware update support
// -------------------------------------------------------------------------------
// false -> disable
// true  -> enable (requires WEB_SUPPORT)
// -------------------------------------------------------------------------------
#define OTA_SUPPORT true

// -------------------------------------------------------------------------------
// Firmware update (OTA) password
// -------------------------------------------------------------------------------
// Separate pasword to flash new firmware using the web interface
// -------------------------------------------------------------------------------
constexpr auto OTA_PWD = "FeedMeWithBytes!";

// -------------------------------------------------------------------------------
// ratpak/calculator self-test page
// -------------------------------------------------------------------------------
// false -> disable
// true  -> enable (requires WEB_SUPPORT) 
// -------------------------------------------------------------------------------
#define CALC_TESTS false

// -------------------------------------------------------------------------------

// compile time configuration checks
static_assert(DISPLAY_TYPE == display_type::in12a ||
                  DISPLAY_TYPE == display_type::in12b ||
                  DISPLAY_TYPE == display_type::in16 ||
                  DISPLAY_TYPE == display_type::in17 ||
                  DISPLAY_TYPE == display_type::b5870 ||
                  DISPLAY_TYPE == display_type::led,
              "Display type configuration incorrect");

#if RPN_MODE != false && RPN_MODE != true
#error "CALC_TYPE configuration incorrect"
#endif

#if WEB_SUPPORT != false && WEB_SUPPORT != true
#error "WEB_SUPPORT configuration incorrect"
#endif

#if OTA_SUPPORT != false && OTA_SUPPORT != true
#error "OTA_SUPPORT configuration incorrect"
#endif

#if CALC_TESTS != false && CALC_TESTS != true
#error "CALC_TESTS configuration incorrect"
#endif

#if OTA_SUPPORT && !WEB_SUPPORT
#error "OTA_SUPPORT requires WEB_SUPPORT"
#endif

#if CALC_TESTS && !WEB_SUPPORT
#error "CALC_TESTS requires WEB_SUPPORT"
#endif
