axtar/Nixie-Calculator/Firmware/Controller/main/SettingsCache.hpp

// SettingsCache.hpp

// allows fast access to the current values of the settings

// Copyright (C) 2020-2026 highvoltglow
// Licensed under the MIT License

#pragma once

#include <Arduino.h>
#include <SettingDefs.h>
#include <Timezone.hpp>

class SettingsCache
{
public:
  SettingsCache() = delete;

  inline static startup_mode::startup_mode startupMode;
  inline static show_version::show_version showVersion;
  inline static auto_off_mode::auto_off_mode autoOffMode;
  inline static unsigned long autoOffDelay;
  inline static SCHEDULETIME offStartTime;
  inline static SCHEDULETIME offStopTime;
  inline static int offDays;
  inline static clock_mode::clock_mode clockMode;
  inline static hour_mode::hour_mode hourMode;
  inline static time_separator::time_separator timeSeparator;
  inline static leading_zero::leading_zero leadingZero;
  inline static time_effects::time_effects timeEffects;
  inline static date_format::date_format dateFormat;
  inline static pir_mode::pir_mode pirMode;
  inline static unsigned long pirDelay;
  inline static gps_mode::gps_mode gpsMode;
  inline static gps_speed::gps_speed gpsSpeed;
  inline static unsigned long gpsSyncInterval;
  inline static temperature_mode::temperature_mode temperatureMode;
  inline static temperature_cf::temperature_cf temperatureCF;
  inline static led_mode::led_mode ledMode;
  inline static int ledBrightness;
  inline static calc_rgb_mode::calc_rgb_mode calcRGBMode;
  inline static clock_rgb_mode::clock_rgb_mode clockRGBMode;
  inline static breathing_mode::breathing_mode breathingMode;
  inline static trig_color_change::trig_color_change trigColorChange;
  inline static SCHEDULETIME ledStartTime;
  inline static SCHEDULETIME ledStopTime;
  inline static SCHEDULETIME ledStartTime2;
  inline static SCHEDULETIME ledStopTime2;
  inline static SCHEDULETIME acpStartTime;
  inline static int acpDuration;
  inline static acp_force_on::acp_force_on acpForceOn;
  inline static RGBCOLOR negativeColor;
  inline static RGBCOLOR positiveColor;
  inline static RGBCOLOR errorColor;
  inline static RGBCOLOR negExpColor;
  inline static RGBCOLOR posExpColor;
  inline static RGBCOLOR fixedCalcColor;
  inline static RGBCOLOR timeColor;
  inline static RGBCOLOR timeColor2;
  inline static RGBCOLOR dateColor;
  inline static RGBCOLOR tempColor;
  inline static RGBCOLOR fixedColor;
  inline static timezoneRule dstRule;
  inline static timezoneRule stdRule;
  inline static timezoneRule dstRule2;
  inline static timezoneRule stdRule2;
  inline static gps_notify_sync::gps_notify_sync gpsNotifySync;
  inline static RGBCOLOR gpsSyncColor;
  inline static notify_timer::notify_timer notifyTimer;
  inline static RGBCOLOR timerColor;
  inline static fixed_decimals::fixed_decimals fixedDecimals;
  inline static angle_mode::angle_mode angleMode;
  inline static show_busy_calc::show_busy_calc showBusyCalc;
  inline static int maxExpDigits;
  inline static int scrollDelay;
  inline static int calcPrecision;
  inline static rounding_mode::rounding_mode roundingMode;
  inline static calc_input_direc::calc_input_direc calcInputDirec;
  inline static input_blinking::input_blinking inputBlinking;
  inline static int brightness;
  inline static int dimBrightness;
  inline static int dimLedBrightness;
  inline static SCHEDULETIME dimStartTime;
  inline static SCHEDULETIME dimStopTime;
  inline static ap_auto_start::ap_auto_start apAutoStart;
  inline static int rtcDriftCorr;
  inline static int extTempCorr;
};
