axtar/Nixie-Calculator/Firmware/Controller/include/FirmwareInfo.h

// FirmwareInfo.h

// Provides information about the firmware version

// Copyright (C) 2020-2026 highvoltglow
// Licensed under the MIT License

#pragma once

#include <Arduino.h>

//- VERSION
constexpr uint8_t MAJOR_VERSION = 0;
constexpr uint8_t MINOR_VERSION = 11;
constexpr uint8_t REVISION = 3;
constexpr auto FW_STATUS = "beta";
