axtar/Nixie-Calculator/Firmware/Controller/include/DisplayTypes.h

// DisplayTypes.h

// Display types

// Copyright (C) 2020-2026 highvoltglow
// Licensed under the MIT License

#pragma once

// available display types
enum class display_type
{
  undefined,
  in12a, // if using neon bulbs as decimal point
  in12b, // if using IN-12B decimal point
  in16,
  in17,
  b5870,
  led
};
