axtar/Nixie-Calculator/Firmware/Controller/main/MemRegister.hpp

// MemRegister.hpp

// internal memory register

// Copyright (C) 2020-2026 highvoltglow
// Licensed under the MIT License

#pragma once

#include <Arduino.h>
#include <ratpak.h>

class MemRegister
{
public:
  MemRegister()
  {
    _reg = nullptr;
  }

  virtual ~MemRegister()
  {
  }

  // set memory register value, store 0 as nullptr to use less memory
  void set(PRAT p)
  {
    if (!zerrat(p))
    {
      DUPRAT(_reg, p);
    }
    else
    {
      destroyrat(_reg);
    }
  }

  // get memory register value
  PRAT get() const
  {
    if (_reg != nullptr)
    {
      return (_reg);
    }
    else
    {
      return (rat_zero);
    }
  }

  // clear memory register
  void clear()
  {
    destroyrat(_reg);
  }

private:
  PRAT _reg;
};
