axtar/Nixie-Calculator/Firmware/Controller/main/CalcTests.hpp

// CalcTests.hpp

// self-test suite for ratpak/CalcMath, exercised through the /tests web page.
// build with CALC_TESTS enabled in Config.h; excluded from release builds by default.

// Copyright (C) 2020-2026 highvoltglow
// Licensed under the MIT License

#pragma once

#include <Arduino.h>
#include <vector>
#include <functional>
#include <ratpak.h>
#include <CalcDefs.h>
#include <CalcError.hpp>
#include <CalcMath.hpp>
#include <CalcIO.hpp>
#include <SettingsCache.hpp>

class CalcTests
{
public:
  // run the correctness + regression suite and return the results as a JSON array
  static String runCorrectnessJSON(uint32_t radix, int32_t precision)
  {
    std::vector<TestResult> results;
    for (const auto &test : correctnessTests())
    {
      execute(results, test, radix, precision);
    }
    return toJSON(results);
  }

  // run the known-slow cases (large root, factorial near the rat_max_fact limit) and
  // return the results as a JSON array; kept separate from the correctness suite since
  // it can take much longer and is only meant to be triggered explicitly
  static String runPerformanceJSON(uint32_t radix, int32_t precision)
  {
    std::vector<TestResult> results;
    for (const auto &test : performanceTests())
    {
      execute(results, test, radix, precision);
    }
    return toJSON(results);
  }

private:
  struct Outcome
  {
    bool pass;
    String detail;
  };

  struct TestResult
  {
    const char *name;
    const char *category;
    bool pass;
    String detail;
    unsigned long durationUs;
  };

  using TestFn = std::function<Outcome(uint32_t radix, int32_t precision)>;

  struct TestDef
  {
    const char *name;
    const char *category;
    TestFn fn;
  };

  // RAII wrapper around a PRAT so test bodies don't need explicit destroyrat()
  // bookkeeping; addr() hands out the PRAT* that ratpak's in/out functions expect,
  // and since those only ever replace *pa in place (never the outer PRAT* itself)
  // it stays valid to use after the call.
  class Rat
  {
  public:
    Rat() : _p(nullptr) {}
    explicit Rat(PRAT p) : _p(p) {}
    Rat(const Rat &) = delete;
    Rat &operator=(const Rat &) = delete;
    Rat(Rat &&other) noexcept : _p(other._p) { other._p = nullptr; }
    Rat &operator=(Rat &&other) noexcept
    {
      if (this != &other)
      {
        if (_p)
        {
          destroyrat(_p);
        }
        _p = other._p;
        other._p = nullptr;
      }
      return *this;
    }
    ~Rat()
    {
      if (_p)
      {
        destroyrat(_p);
      }
    }
    PRAT get() const { return _p; }
    PRAT *addr() { return &_p; }

    static Rat fromInt(int32_t v) { return Rat(i32torat(v)); }
    static Rat dup(PRAT src)
    {
      PRAT d = nullptr;
      DUPRAT(d, src);
      return Rat(d);
    }

  private:
    PRAT _p;
  };

  // parses a decimal literal such as "3248.7" or "-4", with an optional separate
  // exponent (e.g. mantissa "9", exponent "9999" -> 9e+9999)
  static Rat fromDecimal(const char *mantissa, uint32_t radix, int32_t precision, const char *exponent = nullptr)
  {
    bool mantissaNegative = (mantissa[0] == '-');
    std::string_view m(mantissaNegative ? mantissa + 1 : mantissa);
    std::string_view e(exponent ? exponent : "");
    return Rat(StringToRat(mantissaNegative, m, false, e, radix, precision));
  }

  static String ratStr(PRAT a, uint32_t radix, int32_t precision)
  {
    Rat t = Rat::dup(a);
    PRAT p = t.get();
    return String(RatToScientificString(p, radix, precision).c_str());
  }

  // ratpak's Taylor-series results (trig/log/exp) carry a few noisy tail digits at
  // full precision and are never bit-exact even for "nice" angles, so compare after
  // formatting both sides to a reduced number of significant digits instead of
  // using rat_equ()
  static bool approxEqual(PRAT a, PRAT b, uint32_t radix, int32_t precision)
  {
    int32_t comparePrecision = precision - 8;
    if (comparePrecision < 6)
    {
      comparePrecision = 6;
    }
    Rat ta = Rat::dup(a);
    Rat tb = Rat::dup(b);
    PRAT pa = ta.get();
    PRAT pb = tb.get();
    String sa(RatToString(pa, NumberFormat::Scientific, radix, comparePrecision).c_str());
    String sb(RatToString(pb, NumberFormat::Scientific, radix, comparePrecision).c_str());
    return sa == sb;
  }

  static Outcome expectEqual(PRAT actual, PRAT expected, uint32_t radix, int32_t precision, bool exact)
  {
    bool ok = exact ? rat_equ(actual, expected, precision) : approxEqual(actual, expected, radix, precision);
    if (ok)
    {
      return {true, String()};
    }
    return {false, "expected " + ratStr(expected, radix, precision) + " but got " + ratStr(actual, radix, precision)};
  }

  // runs body() and checks that it throws exactly expectedCode
  static Outcome expectThrow(const std::function<void()> &body, uint32_t expectedCode, const char *description)
  {
    try
    {
      body();
    }
    catch (uint32_t error)
    {
      if (error == expectedCode)
      {
        return {true, String()};
      }
      return {false, String("expected ") + description + " but got a different error code (0x" + String(error, HEX) + ")"};
    }
    return {false, String("expected ") + description + " but no error was thrown"};
  }

  // runs a CalcMath::calculate() call and checks the returned operation_return_code
  static Outcome expectCalcError(operation_return_code actual, operation_return_code expected)
  {
    if (actual == expected)
    {
      return {true, String()};
    }
    String actualText = (actual == operation_return_code::success) ? String("success") : CalcError::getErrorText(actual);
    return {false, "expected error \"" + CalcError::getErrorText(expected) + "\" but got \"" + actualText + "\""};
  }

  static void execute(std::vector<TestResult> &results, const TestDef &test, uint32_t radix, int32_t precision)
  {
    unsigned long start = micros();
    Outcome outcome{false, String()};
    try
    {
      outcome = test.fn(radix, precision);
    }
    catch (uint32_t error)
    {
      outcome.pass = false;
      outcome.detail = "unexpected error: " + CalcError::getErrorText(CalcError::toOperationReturnCode(error));
    }
    catch (...)
    {
      outcome.pass = false;
      outcome.detail = "unexpected exception";
    }
    unsigned long durationUs = micros() - start;
    results.push_back({test.name, test.category, outcome.pass, outcome.detail, durationUs});
  }

  // builds the maxTrig bound the same way Calculator::begin() -> setMaxTrig() does (10^100)
  static Rat maxTrigBound(uint32_t radix, int32_t precision)
  {
    Rat bound = Rat::fromInt(10);
    ratpowi32(bound.addr(), 100, precision);
    return bound;
  }

  // CalcIO::setNumber() reads SettingsCache::roundingMode directly (a live global the
  // running calculator also uses), so display-formatting tests that depend on rounding
  // behavior must pin it for the duration of the test and restore it afterward rather
  // than assume, or leave mutated, the user's actual setting.
  class RoundingModeGuard
  {
  public:
    explicit RoundingModeGuard(rounding_mode::rounding_mode mode) : _previous(SettingsCache::roundingMode)
    {
      SettingsCache::roundingMode = mode;
    }
    ~RoundingModeGuard()
    {
      SettingsCache::roundingMode = _previous;
    }

  private:
    rounding_mode::rounding_mode _previous;
  };

  struct ExpectedNumber
  {
    const char *base;
    bool baseNegative;
    const char *exponent; // "" means no exponent shown
    bool exponentNegative;
  };

  static String describeNumber(const String &base, bool baseNegative, bool exponentMode, const String &exponent, bool exponentNegative)
  {
    String s = baseNegative ? "-" : "";
    s += base;
    if (exponentMode)
    {
      s += "e";
      s += exponentNegative ? "-" : "+";
      s += exponent;
    }
    return s;
  }

  // runs CalcIO::setNumber() on value and compares the resulting CALC_NUMBER fields
  // (what actually drives the display) against the expected base/exponent/signs
  static Outcome expectFormatted(PRAT value, uint32_t radix, int32_t precision, uint8_t digitCount, uint8_t maxExpLength,
                                 uint8_t fixedDecimals, bool forceScientific, const ExpectedNumber &expected)
  {
    CalcIO cio(digitCount, maxExpLength);
    uint32_t result = cio.setNumber(value, radix, precision, fixedDecimals, forceScientific);
    if (result != 0)
    {
      return {false, "setNumber returned error 0x" + String(result, HEX)};
    }
    CALC_NUMBER n = cio.getNumber();
    bool expectExponent = (expected.exponent[0] != '\0');
    bool ok = (n.base == expected.base) && (n.baseNegative == expected.baseNegative) &&
              (n.exponentMode == expectExponent) &&
              (!expectExponent || ((n.exponent == expected.exponent) && (n.exponentNegative == expected.exponentNegative)));
    if (ok)
    {
      return {true, String()};
    }
    String got = describeNumber(n.base, n.baseNegative, n.exponentMode, n.exponent, n.exponentNegative);
    String exp = describeNumber(String(expected.base), expected.baseNegative, expectExponent, String(expected.exponent), expected.exponentNegative);
    return {false, "expected " + exp + " but got " + got};
  }
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
